bfrigon/alarm-clock-v3/pictures/decals/applying-decals-back-panel.jpg

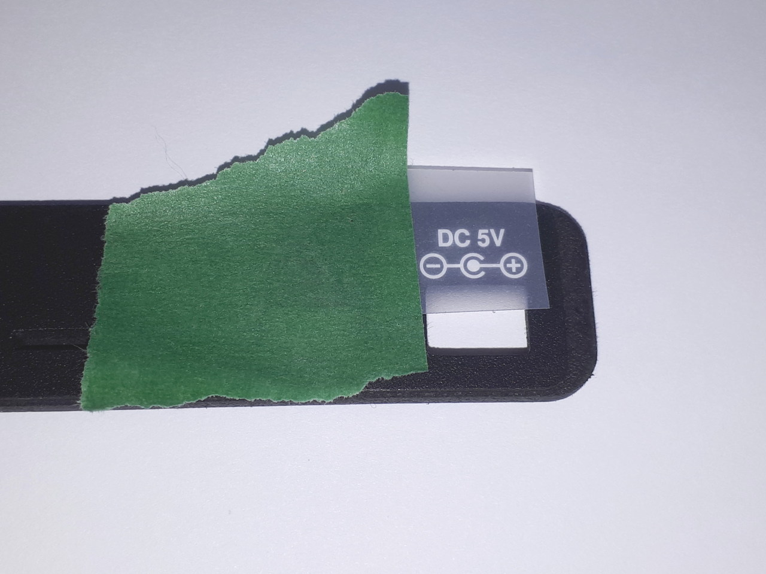
pictures/decals/applying-decals-back-panel.jpg
