bfrigon/alarm-clock-v3/pictures/decals/applying-decals-enclosure-bottom.jpg

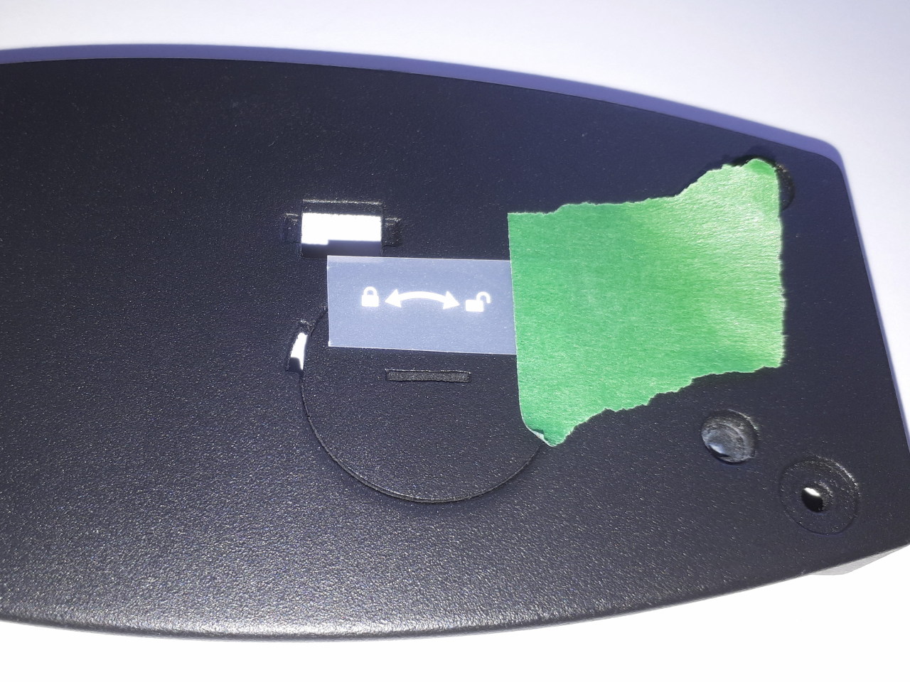
pictures/decals/applying-decals-enclosure-bottom.jpg
