bfrigon/alarm-clock-v3/pictures/decals/decals-back-panel-finished.jpg

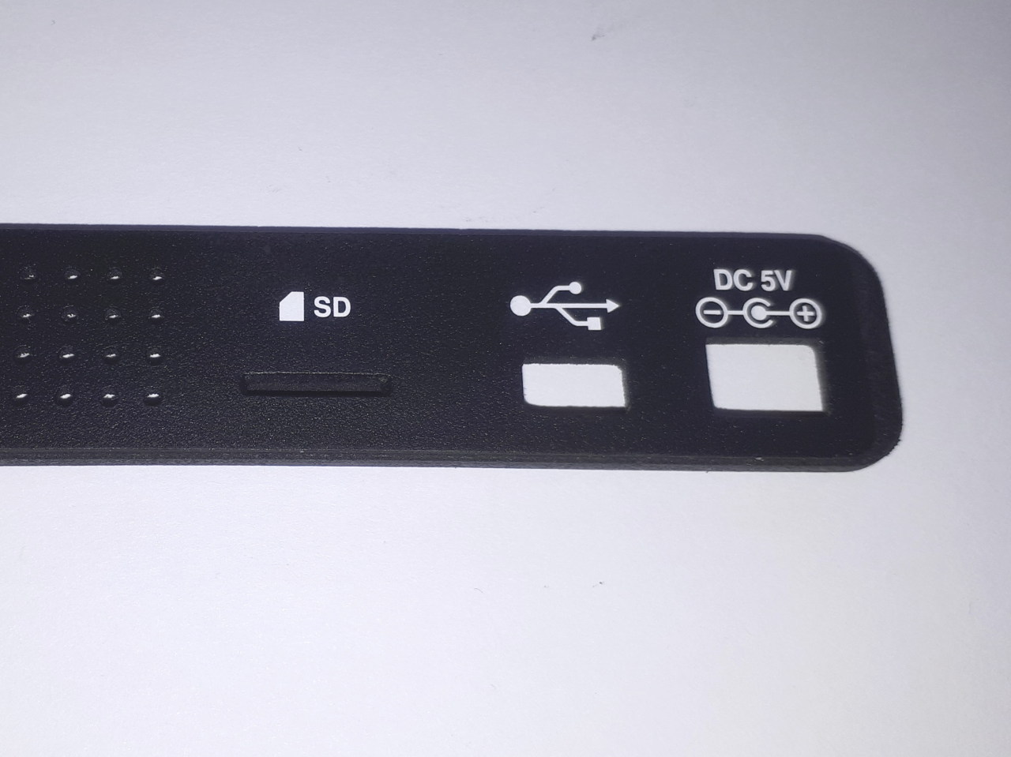
pictures/decals/decals-back-panel-finished.jpg
