bfrigon/alarm-clock-v3/pictures/decals/decals-back-panel.jpg

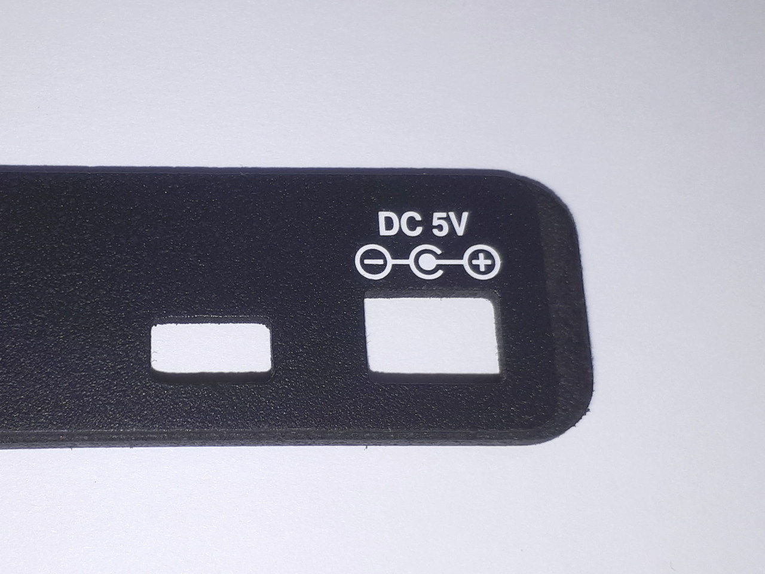
pictures/decals/decals-back-panel.jpg
