bfrigon/alarm-clock-v3/pictures/decals/decals-enclosure-back.jpg

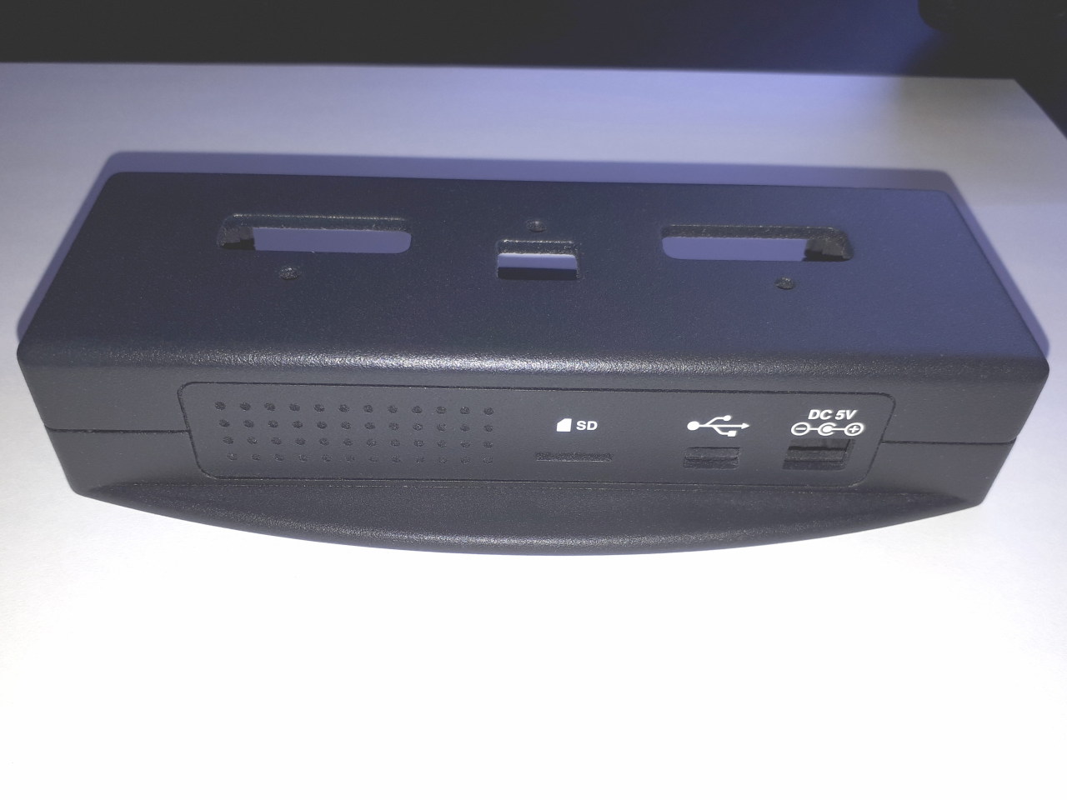
pictures/decals/decals-enclosure-back.jpg
