bfrigon/alarm-clock-v3/pictures/decals/decals-enclosure-bottom.jpg

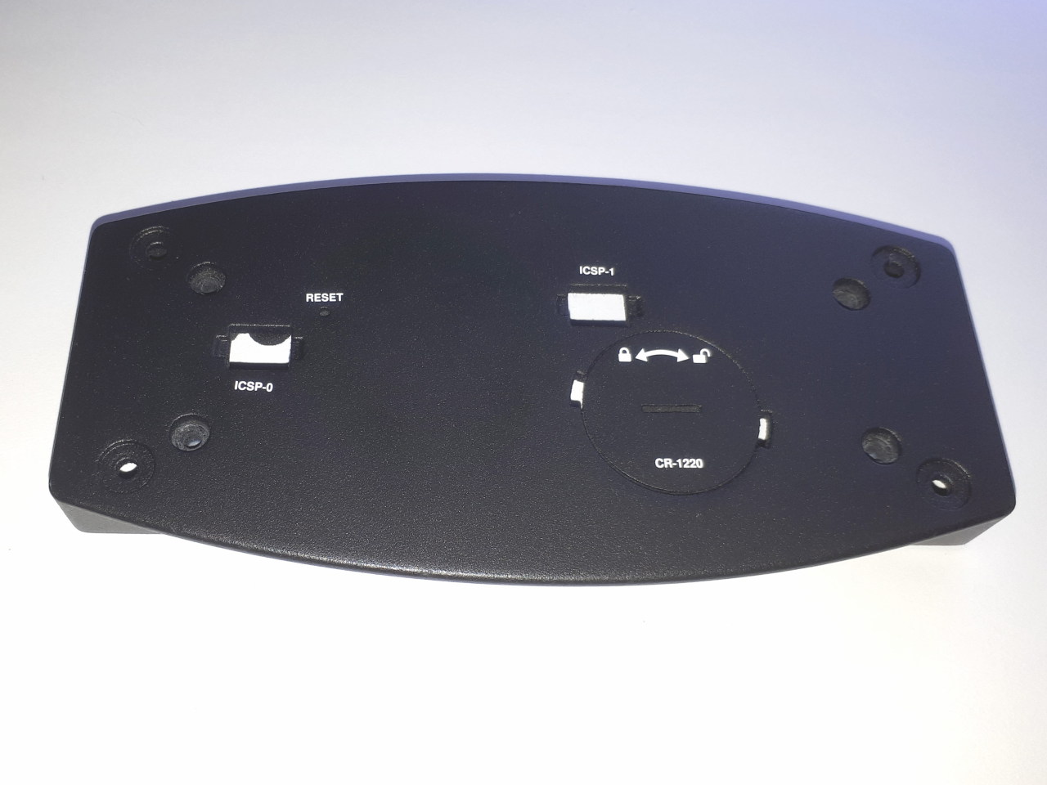
pictures/decals/decals-enclosure-bottom.jpg
