bfrigon/alarm-clock-v3/pictures/decals/decals-enclosure-io-openings.jpg

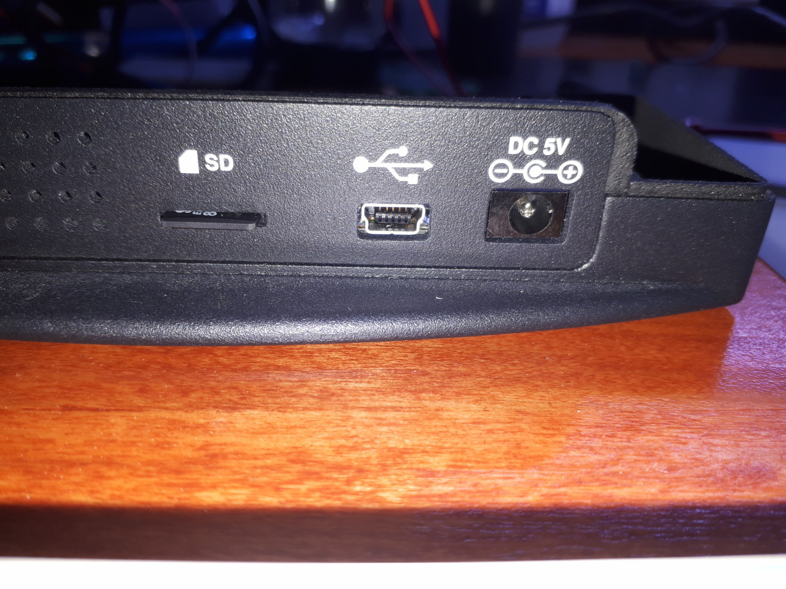
pictures/decals/decals-enclosure-io-openings.jpg
