bfrigon/alarm-clock-v3/pictures/decals/decals-enclosure-side.jpg

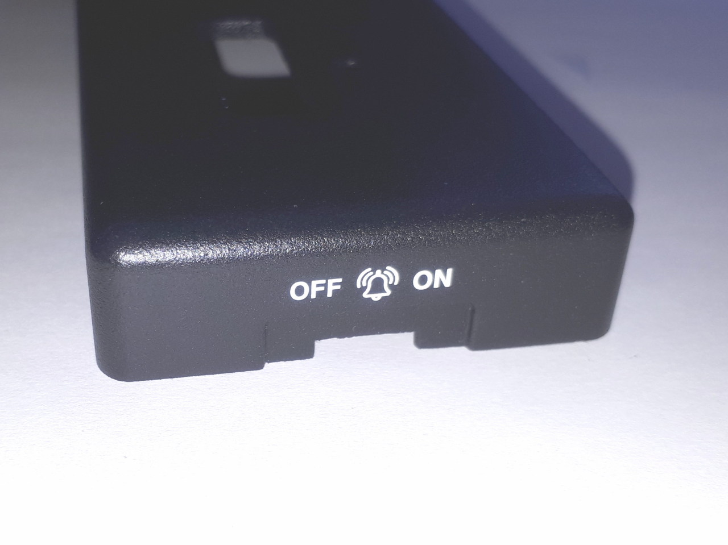
pictures/decals/decals-enclosure-side.jpg
