bfrigon/alarm-clock-v3/pictures/display-panel/diffuser-epoxy-finished.jpg

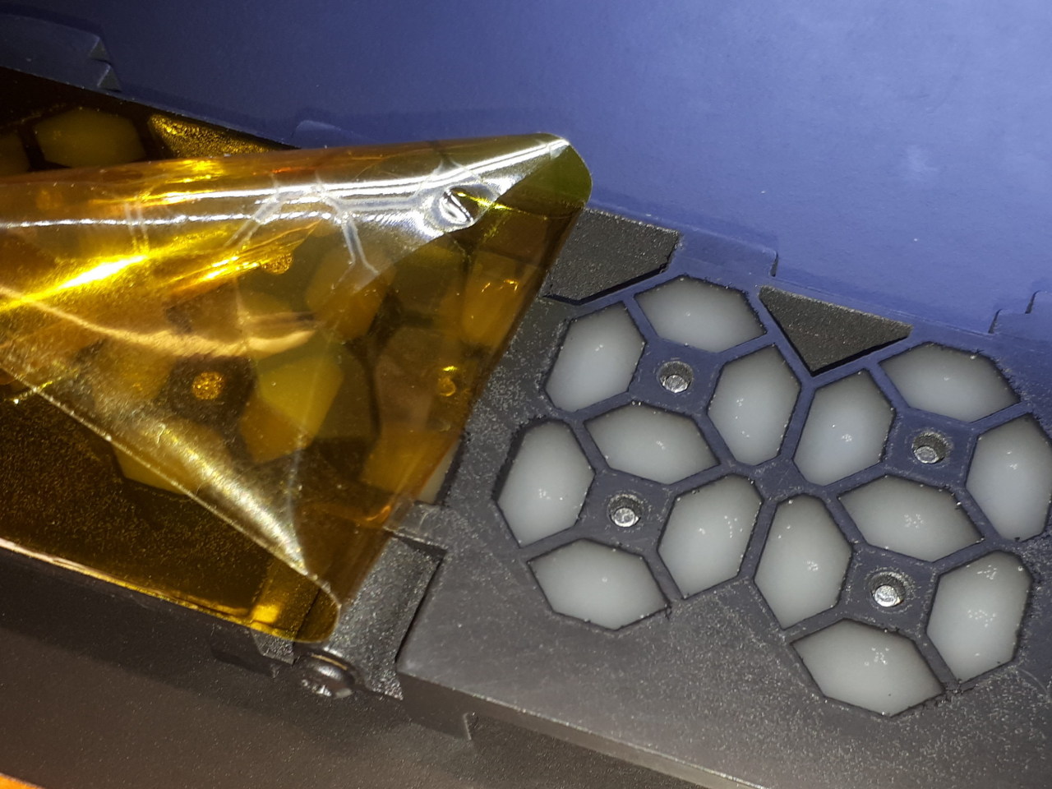
pictures/display-panel/diffuser-epoxy-finished.jpg
