bfrigon/alarm-clock-v3/pictures/display-panel/diffuser-epoxy-kapton-tape.jpg

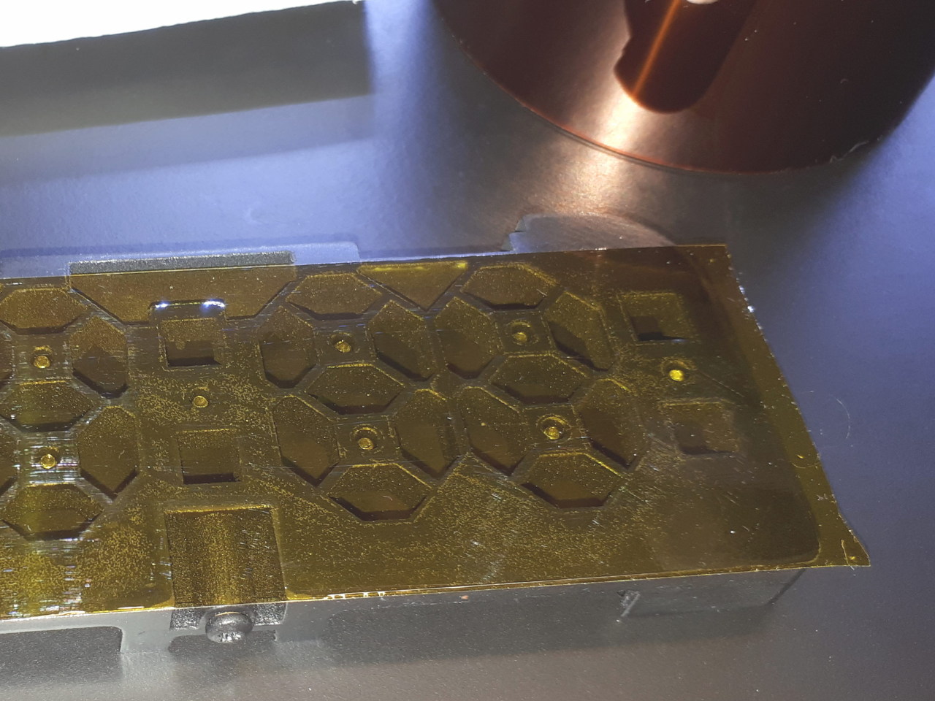
pictures/display-panel/diffuser-epoxy-kapton-tape.jpg
