bfrigon/alarm-clock-v3/pictures/display-panel/diffuser-epoxy-pour.jpg

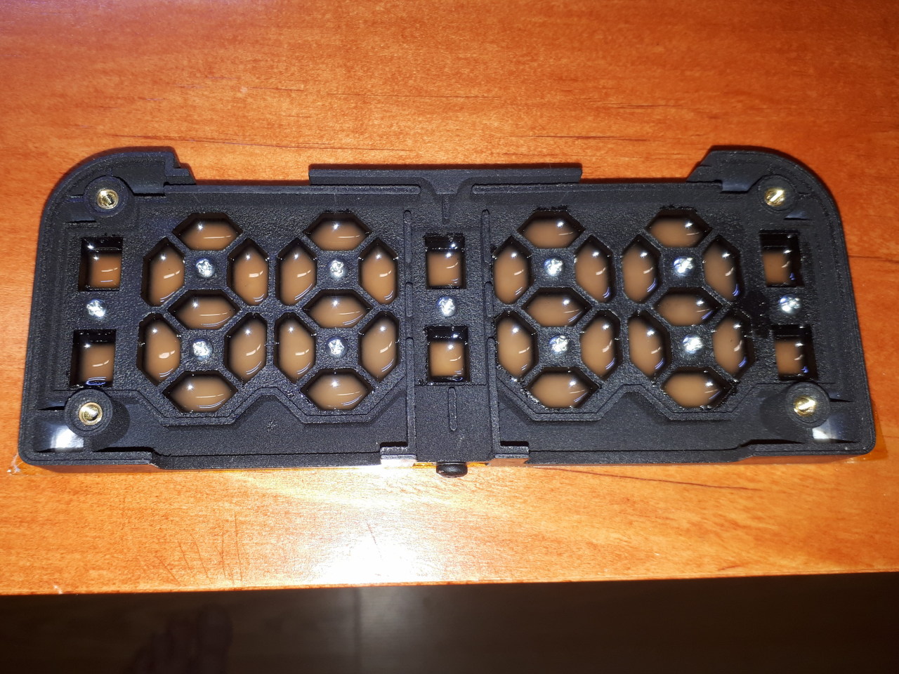
pictures/display-panel/diffuser-epoxy-pour.jpg
