bfrigon/alarm-clock-v3/pictures/display-panel/display-enclosure-first-sanding.jpg

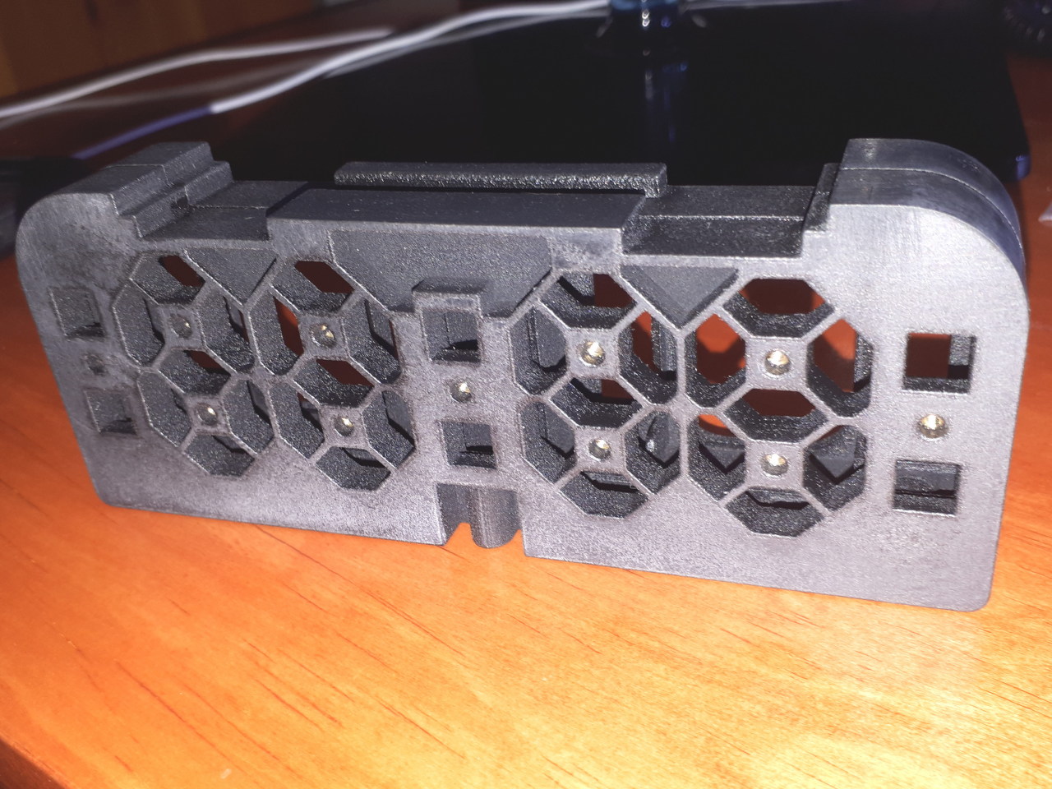
pictures/display-panel/display-enclosure-first-sanding.jpg
