bfrigon/alarm-clock-v3/pictures/display-panel/display-frame-back.jpg

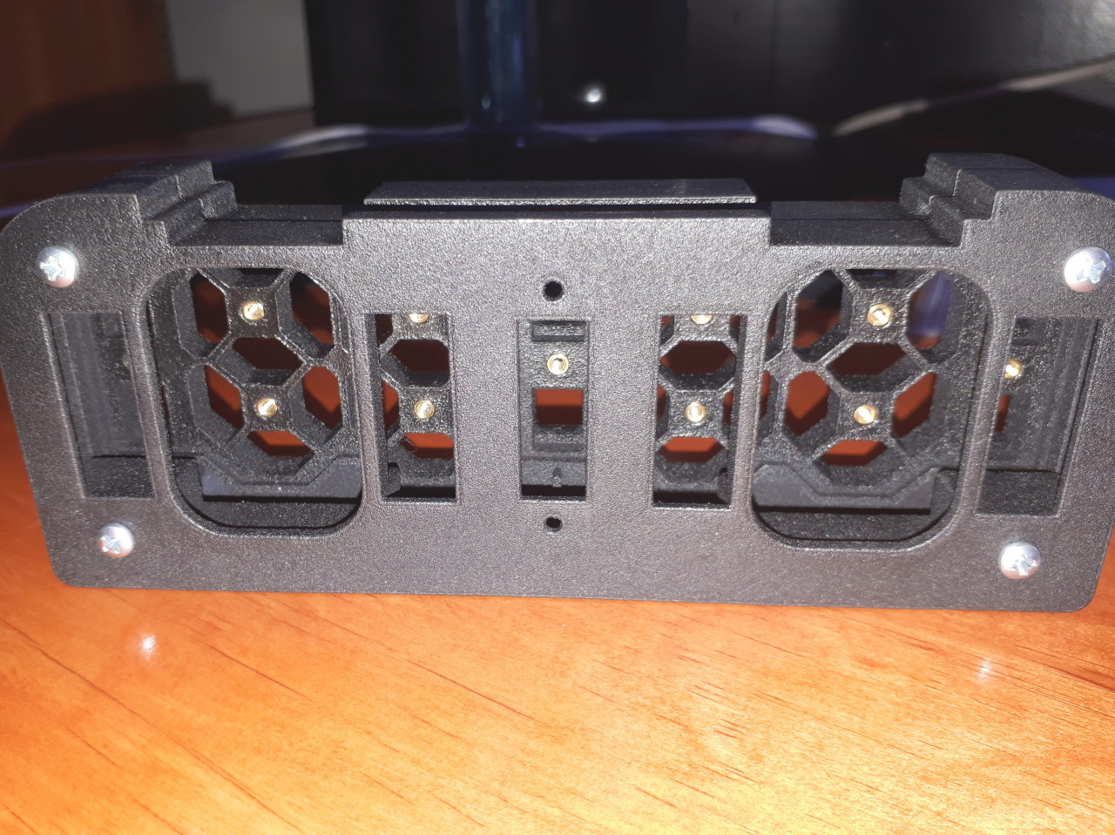
pictures/display-panel/display-frame-back.jpg
