bfrigon/alarm-clock-v3/pictures/display-panel/display-frame-final-sanding.jpg

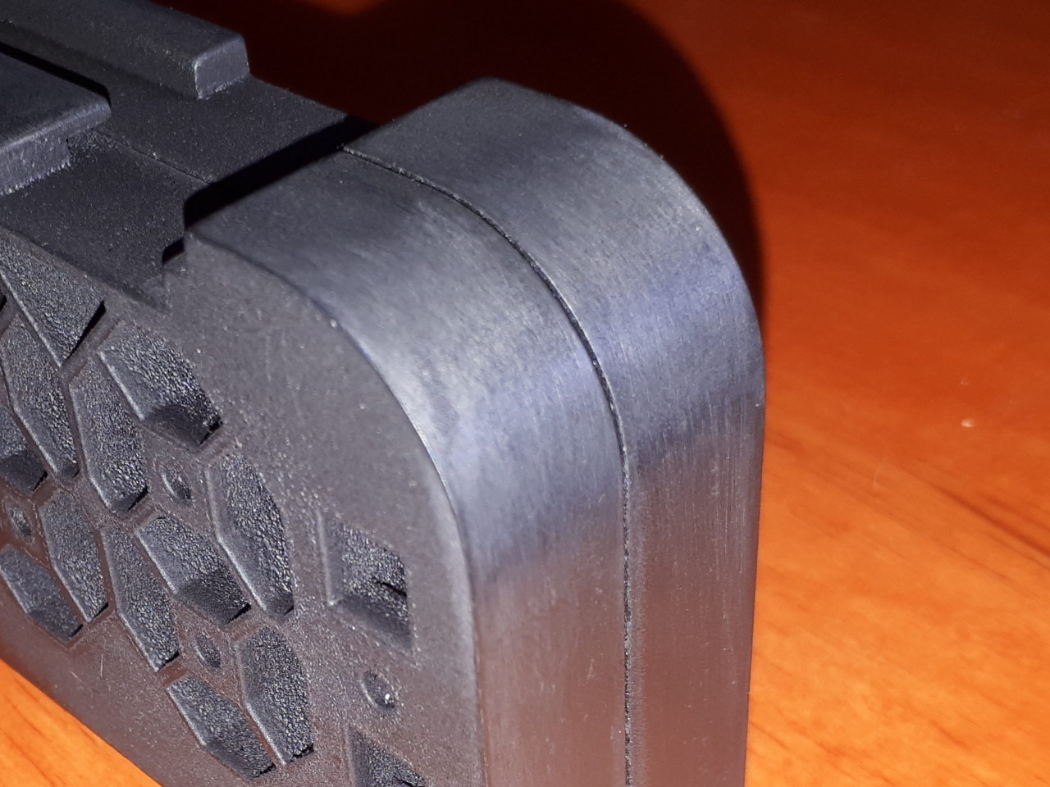
pictures/display-panel/display-frame-final-sanding.jpg
