bfrigon/alarm-clock-v3/pictures/display-panel/display-frame-first-sanding-closeup.jpg

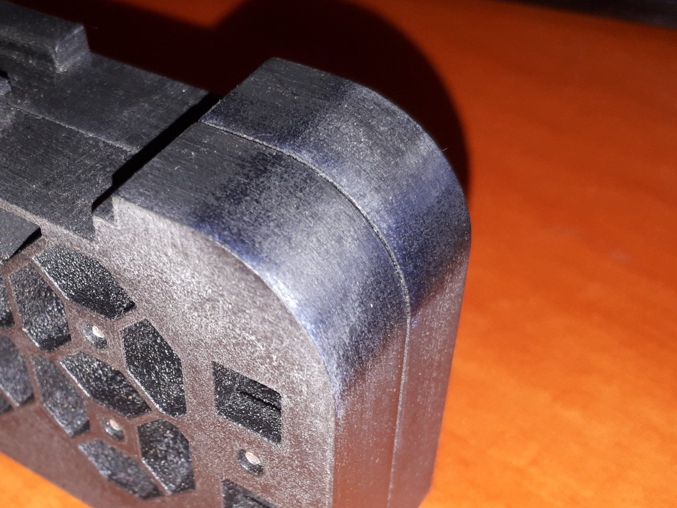
pictures/display-panel/display-frame-first-sanding-closeup.jpg
