bfrigon/alarm-clock-v3/pictures/display-panel/display-frame-front.jpg

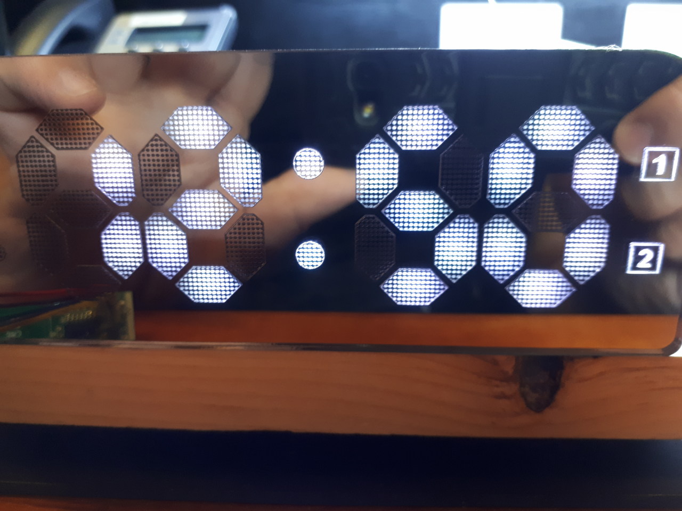
pictures/display-panel/display-frame-front.jpg
