bfrigon/alarm-clock-v3/pictures/display-panel/display-frame-paint-texture.jpg

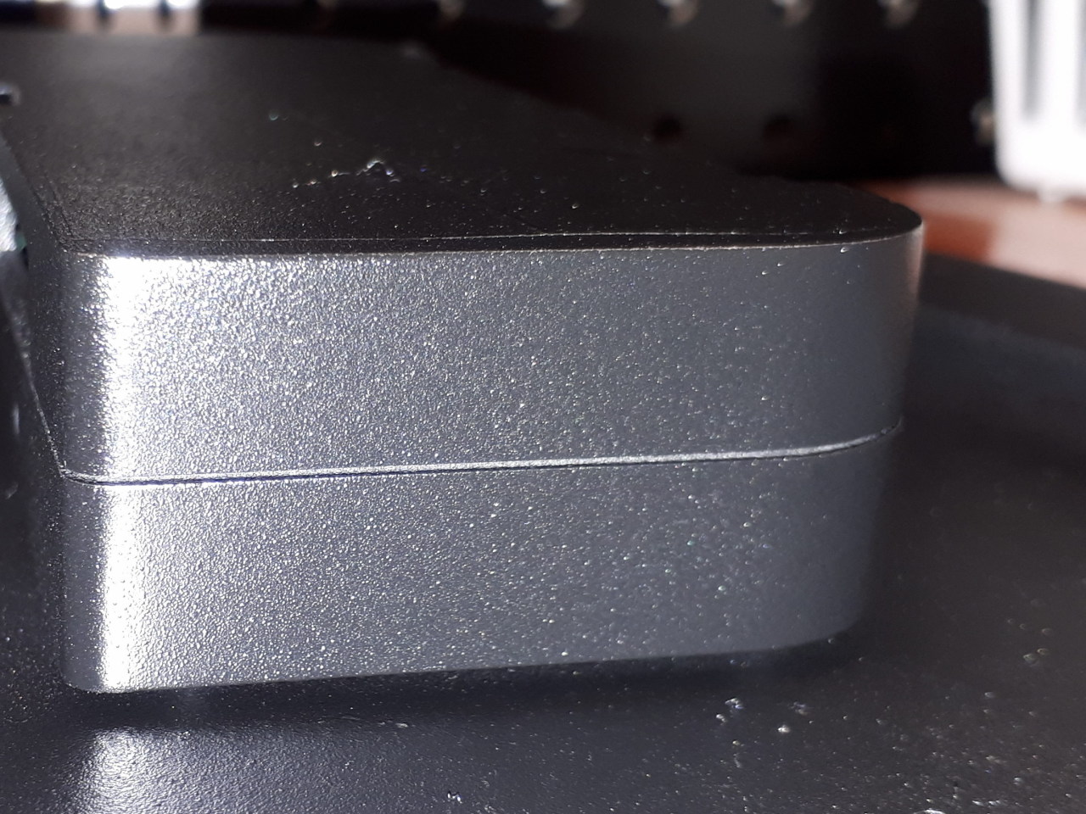
pictures/display-panel/display-frame-paint-texture.jpg
