bfrigon/alarm-clock-v3/pictures/display-panel/display-frame-raw-texture.jpg

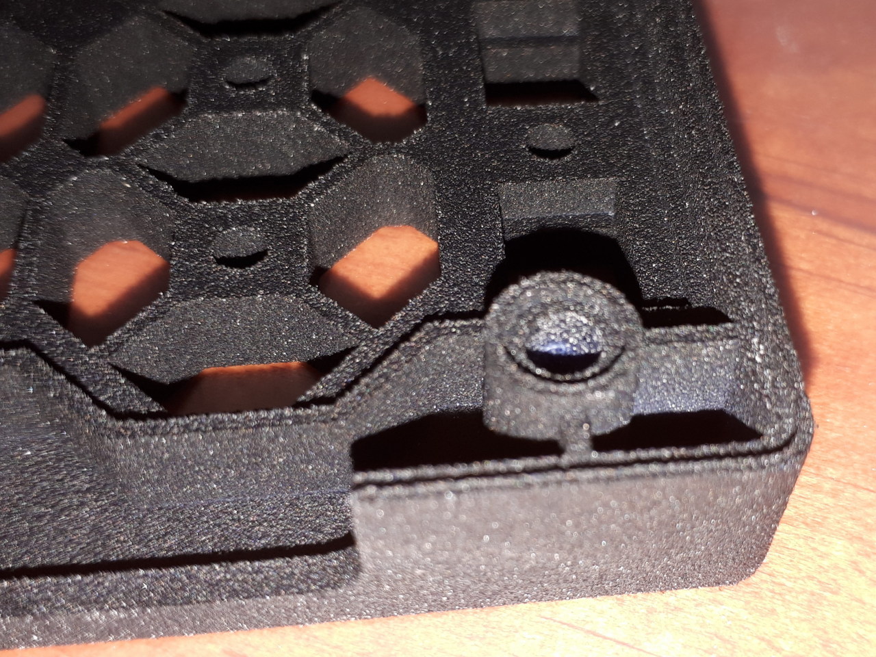
pictures/display-panel/display-frame-raw-texture.jpg
