bfrigon/alarm-clock-v3/pictures/display-panel/display-frame-shapeways.jpg

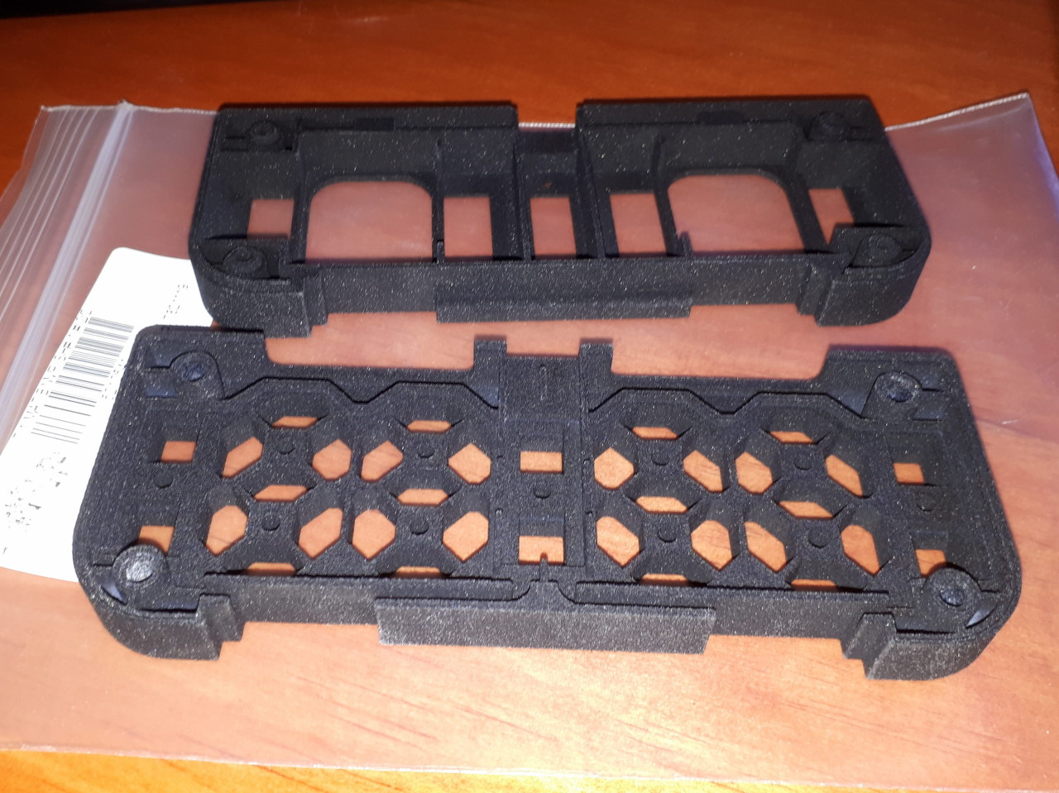
pictures/display-panel/display-frame-shapeways.jpg
