bfrigon/alarm-clock-v3/pictures/display-panel/display-touch-keypad.jpg

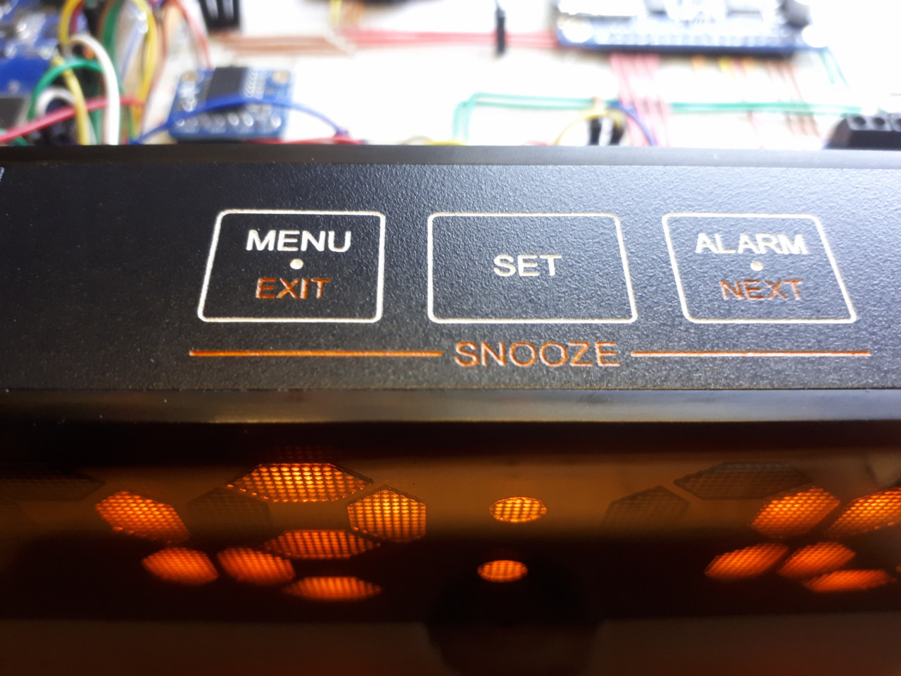
pictures/display-panel/display-touch-keypad.jpg
