bfrigon/alarm-clock-v3/pictures/display-panel/frame-front-with-touch-keypad.jpg

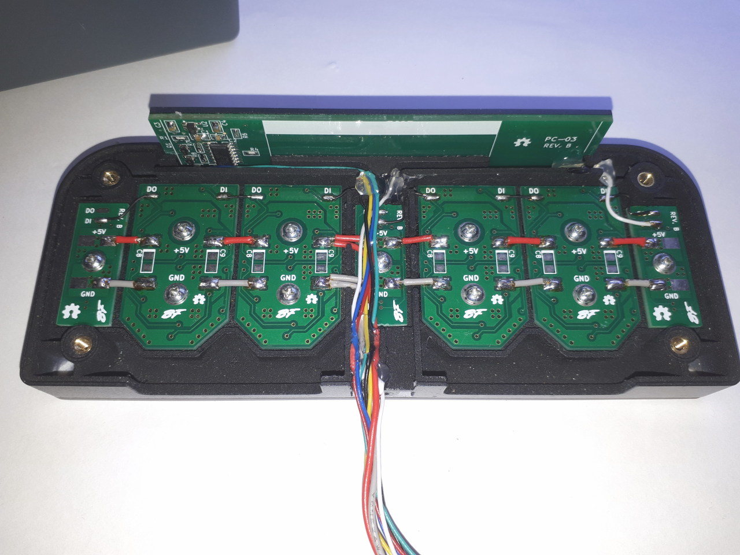
pictures/display-panel/frame-front-with-touch-keypad.jpg
