bfrigon/alarm-clock-v3/pictures/display-panel/front-frame-threaded-inserts.jpg

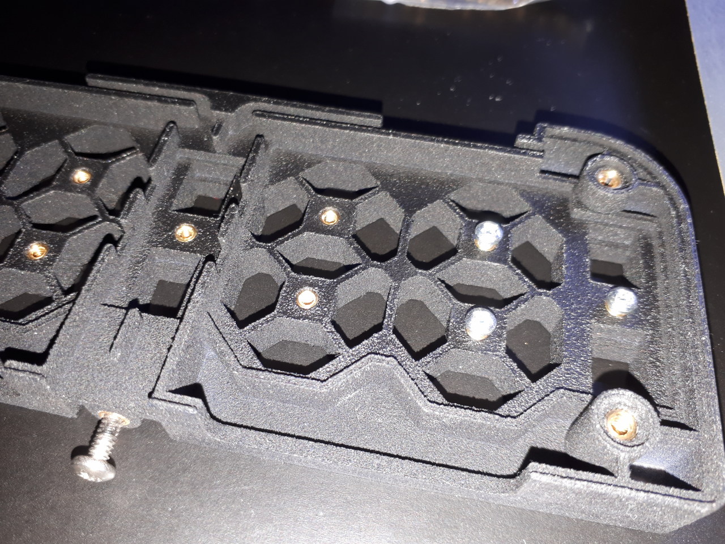
pictures/display-panel/front-frame-threaded-inserts.jpg
