bfrigon/alarm-clock-v3/pictures/display-panel/rgb-digits-pcb-panel.jpg

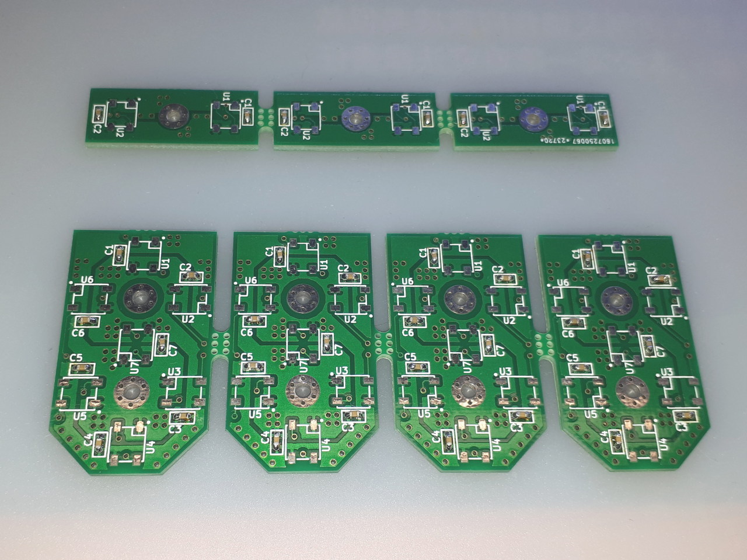
pictures/display-panel/rgb-digits-pcb-panel.jpg
