bfrigon/alarm-clock-v3/pictures/display-panel/rgb-lamp-pcb-back.jpg

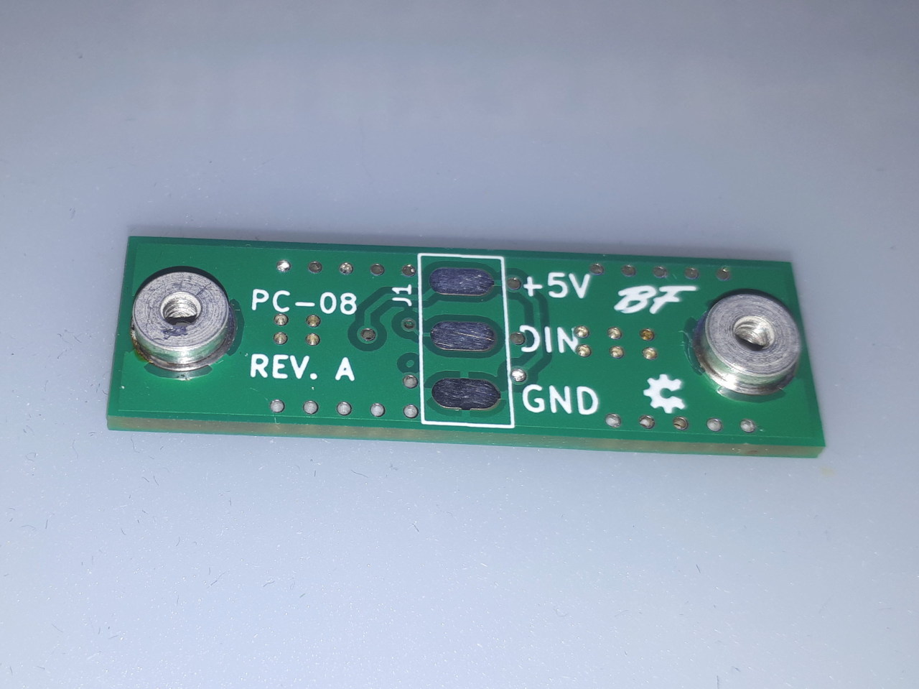
pictures/display-panel/rgb-lamp-pcb-back.jpg
