bfrigon/alarm-clock-v3/pictures/display-panel/rgb-lamp-pcb-front.jpg

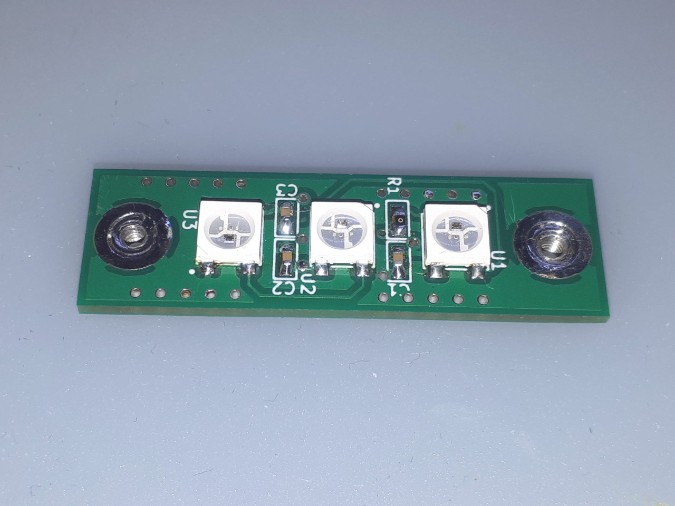
pictures/display-panel/rgb-lamp-pcb-front.jpg
