bfrigon/alarm-clock-v3/pictures/display-panel/touch-keypad-pcb.jpg

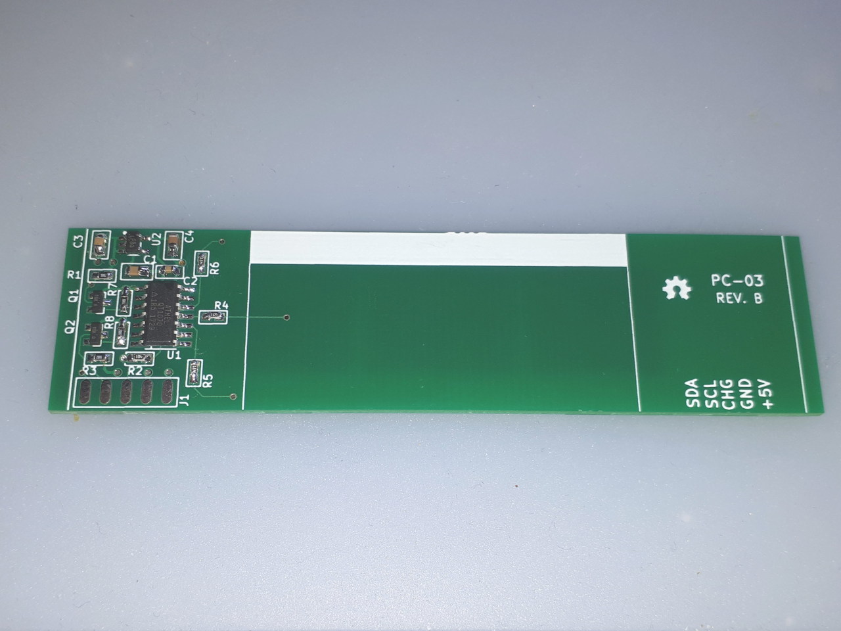
pictures/display-panel/touch-keypad-pcb.jpg
