bfrigon/alarm-clock-v3/pictures/enclosure/enclosure-first-sanding-bottom.jpg

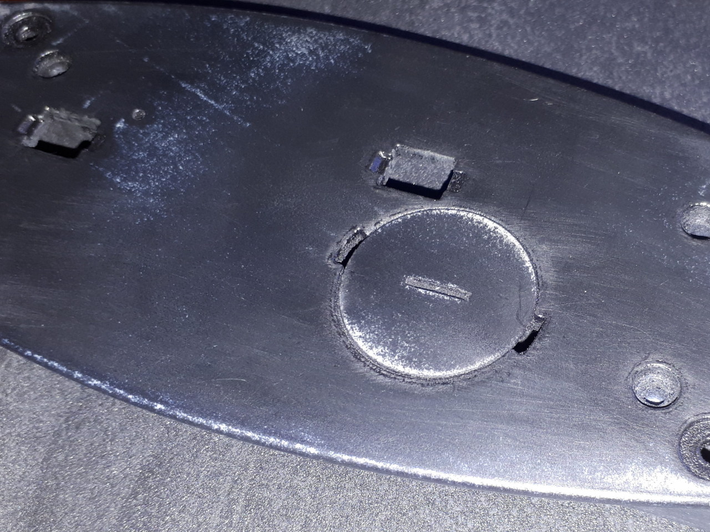
pictures/enclosure/enclosure-first-sanding-bottom.jpg
