bfrigon/alarm-clock-v3/pictures/enclosure/enclosure-first-sanding.jpg

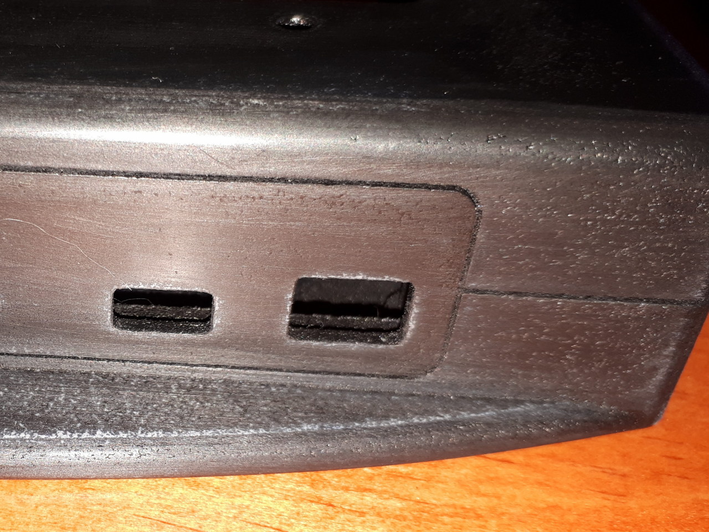
pictures/enclosure/enclosure-first-sanding.jpg
