bfrigon/alarm-clock-v3/pictures/enclosure/enclosure-raw-shapeways.jpg

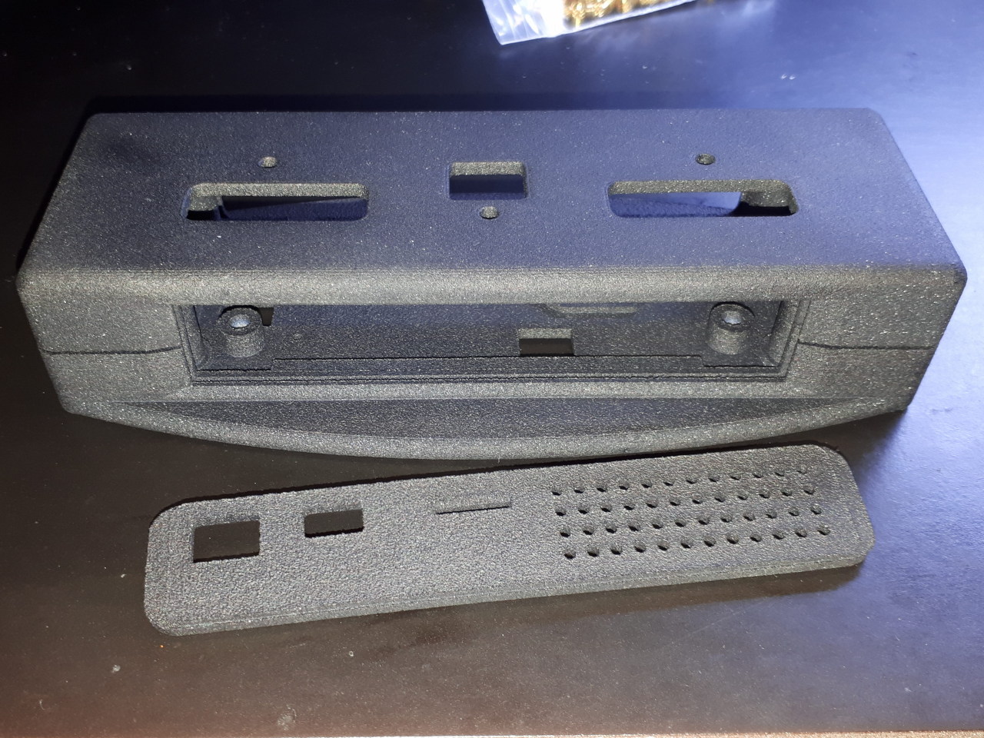
pictures/enclosure/enclosure-raw-shapeways.jpg
