bfrigon/alarm-clock-v3/pictures/enclosure/enclosure-varnish-layer-bottom.jpg

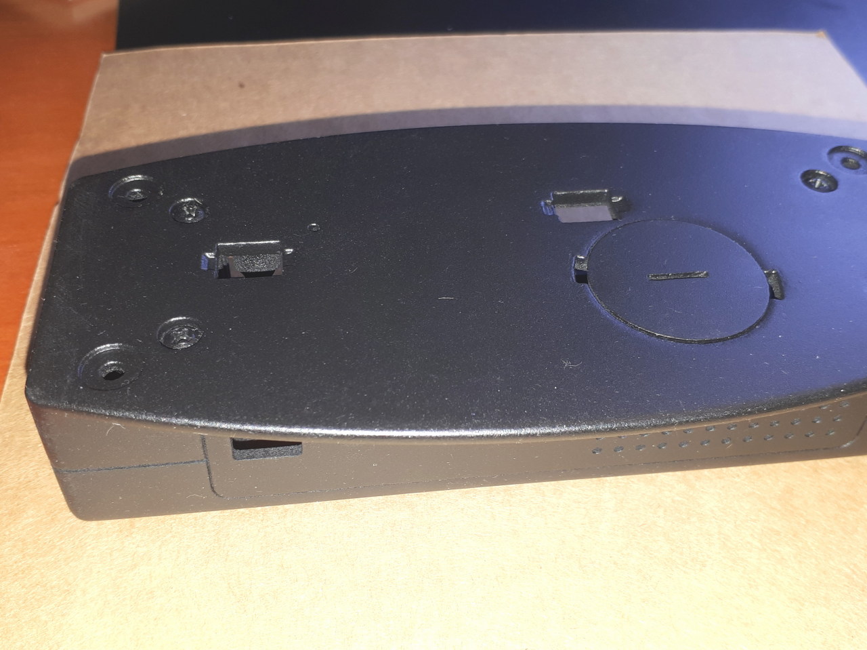
pictures/enclosure/enclosure-varnish-layer-bottom.jpg
