bfrigon/alarm-clock-v3/pictures/enclosure/enclosure-varnish-layer-front.jpg

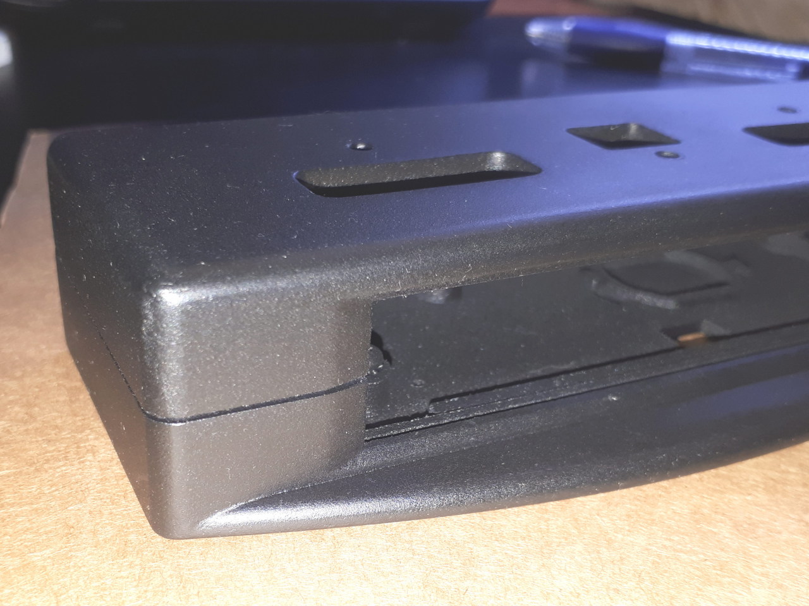
pictures/enclosure/enclosure-varnish-layer-front.jpg
