bfrigon/alarm-clock-v3/pictures/enclosure/threaded-inserts-fixing.jpg

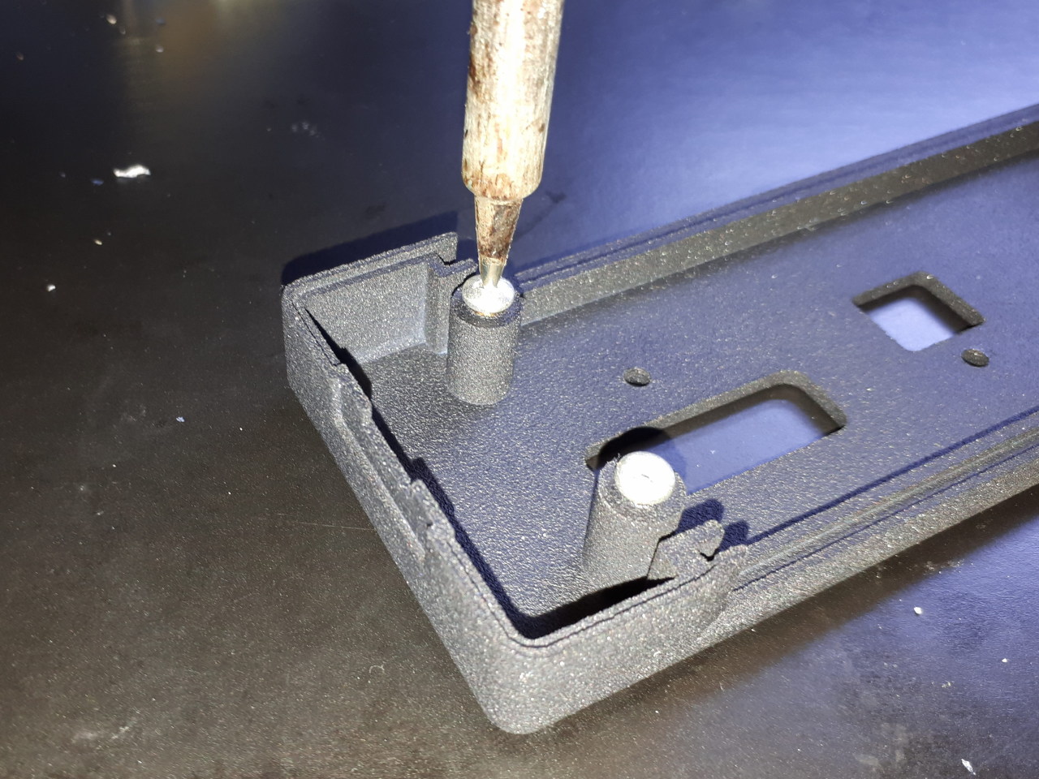
pictures/enclosure/threaded-inserts-fixing.jpg
