bfrigon/alarm-clock-v3/pictures/front-panel/20181004_022008.jpg

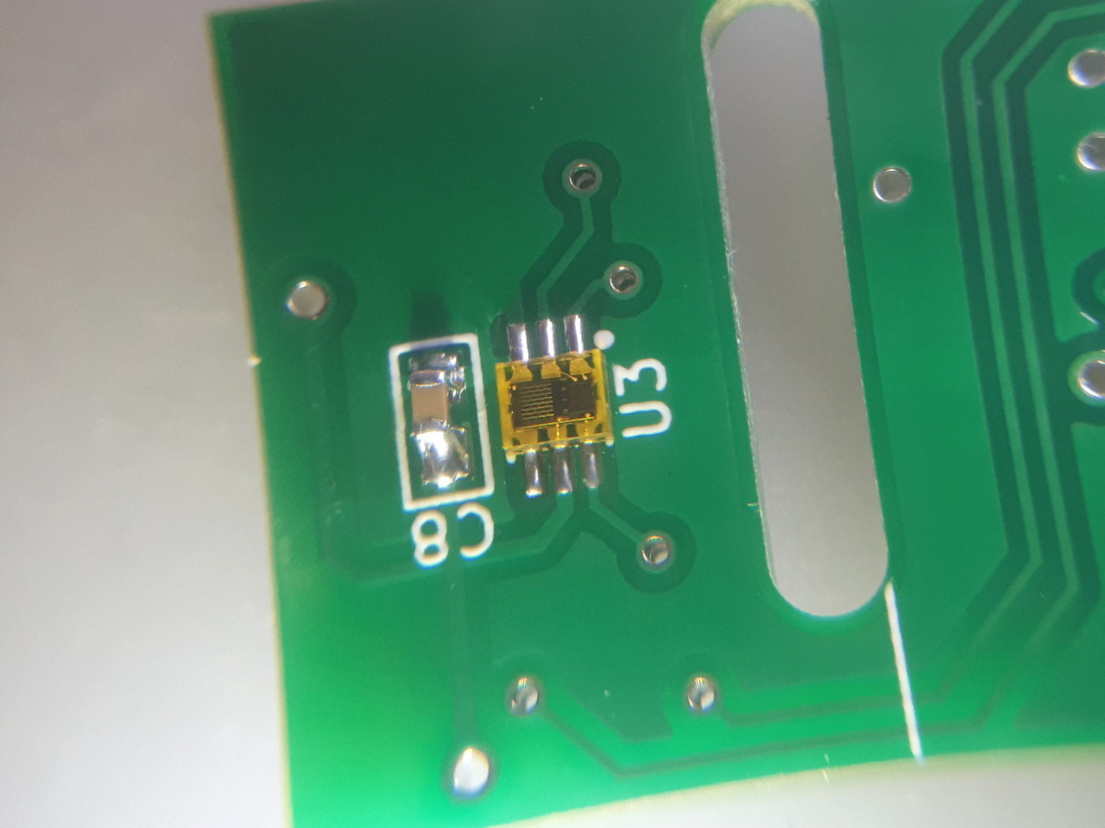
pictures/front-panel/20181004_022008.jpg
