bfrigon/alarm-clock-v3/pictures/front-panel/front-panel-pcb.jpg

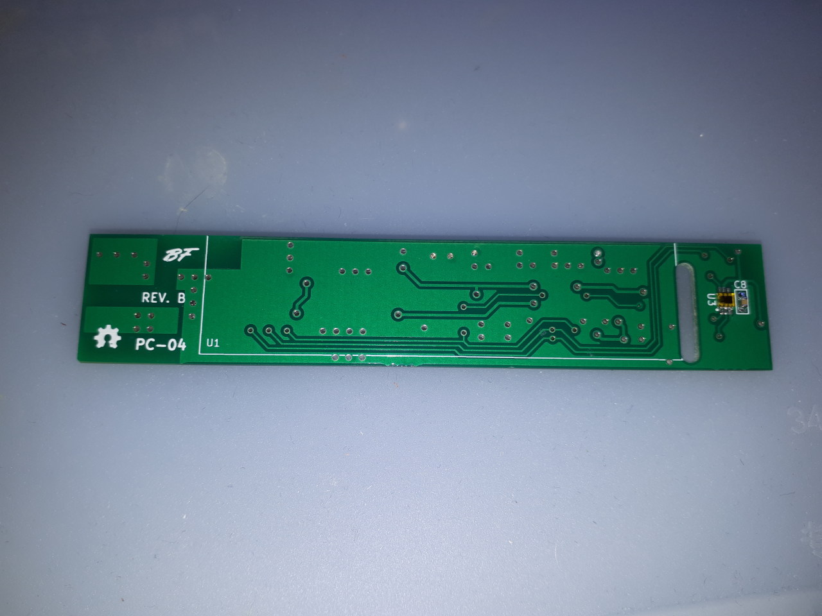
pictures/front-panel/front-panel-pcb.jpg
