bfrigon/alarm-clock-v3/pictures/keypad-overlay/acrylic-paint-orange.jpg

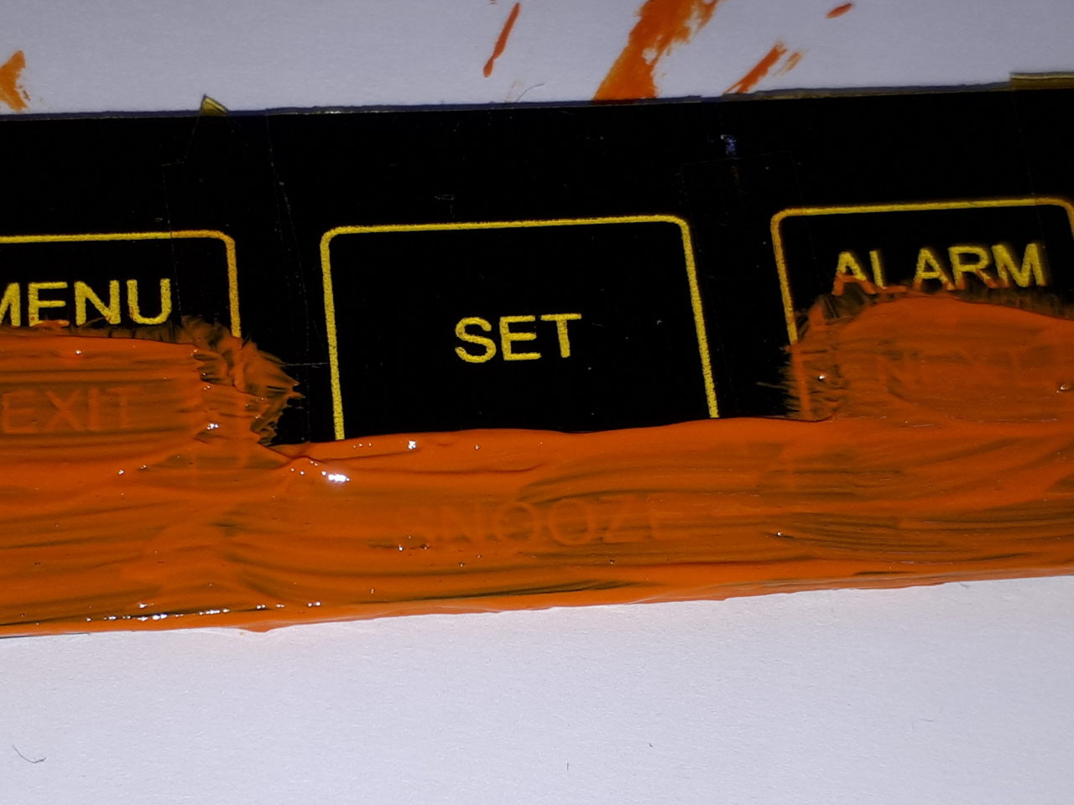
pictures/keypad-overlay/acrylic-paint-orange.jpg
