bfrigon/alarm-clock-v3/pictures/keypad-overlay/acrylic-paint-white.jpg

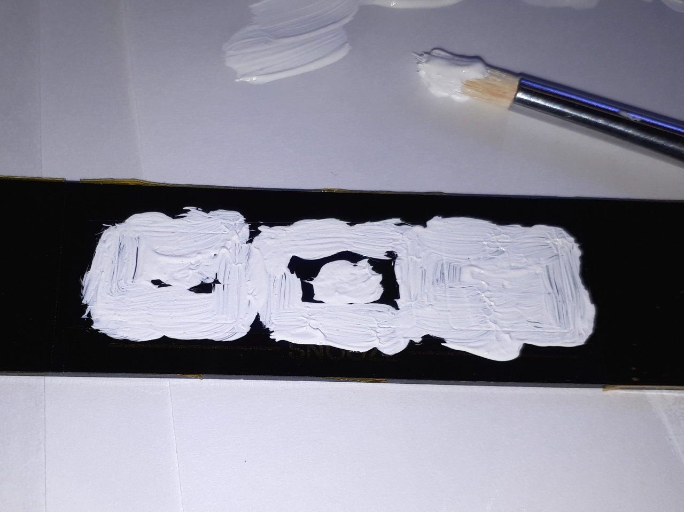
pictures/keypad-overlay/acrylic-paint-white.jpg
