bfrigon/alarm-clock-v3/pictures/keypad-overlay/clear-coated.jpg

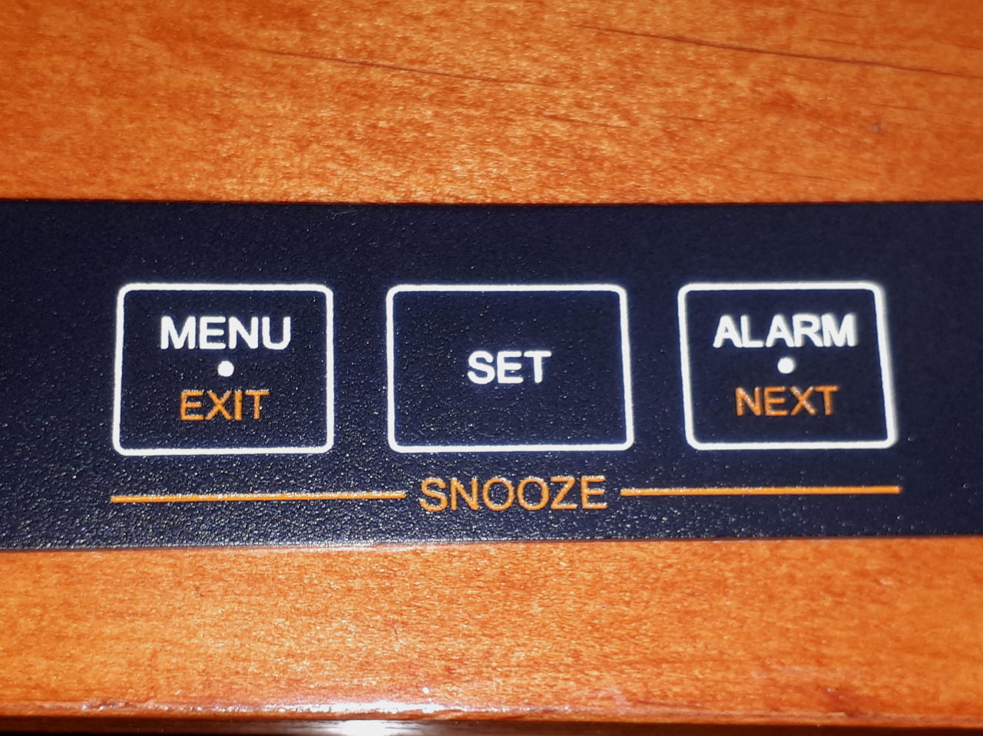
pictures/keypad-overlay/clear-coated.jpg
