bfrigon/alarm-clock-v3/pictures/keypad-overlay/dry-film-acrylic-paint.jpg

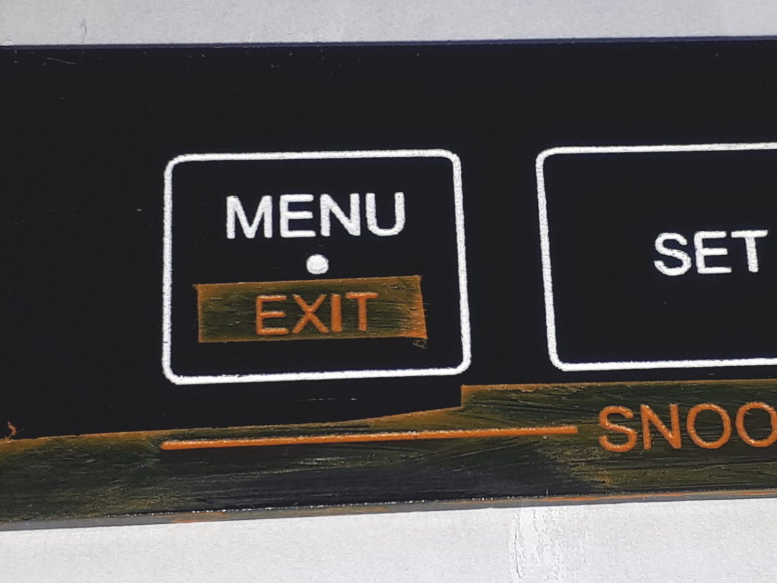
pictures/keypad-overlay/dry-film-acrylic-paint.jpg
