bfrigon/alarm-clock-v3/pictures/keypad-overlay/engraving-filled.jpg

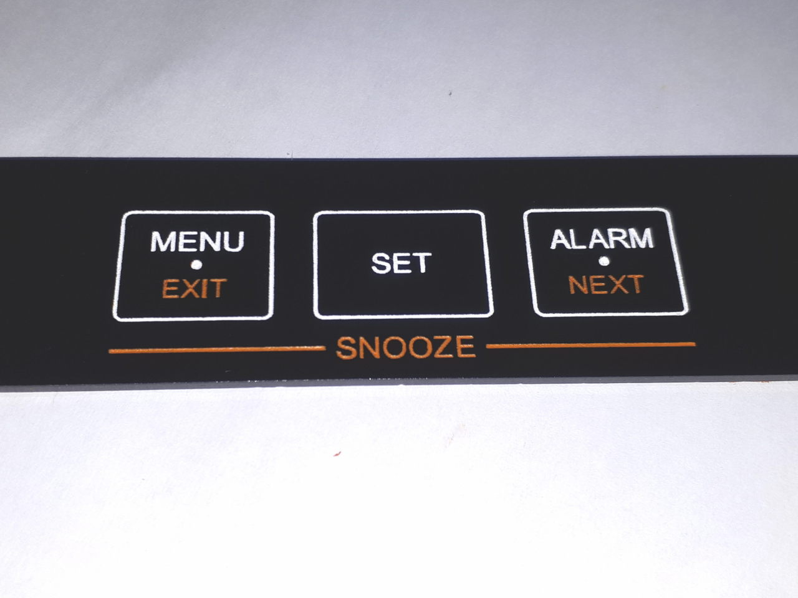
pictures/keypad-overlay/engraving-filled.jpg
