bfrigon/alarm-clock-v3/pictures/keypad-overlay/laser-engraving-overlay.jpg

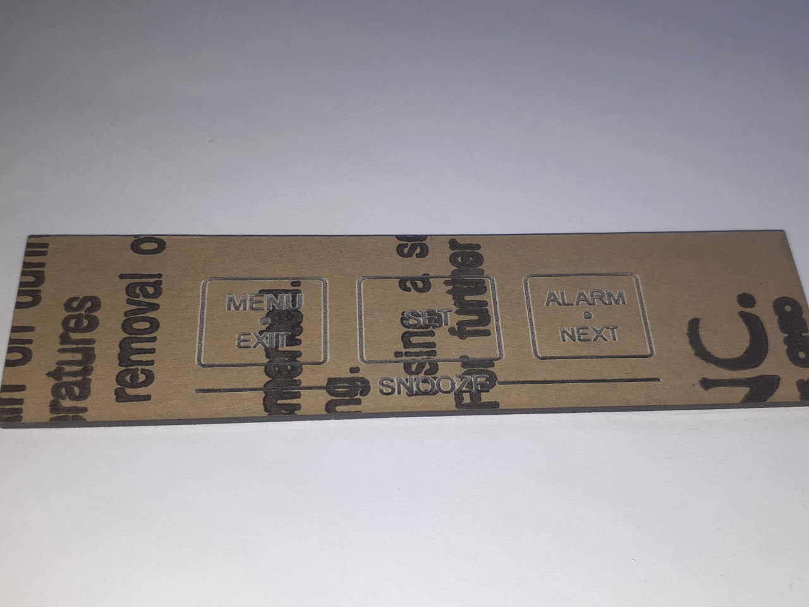
pictures/keypad-overlay/laser-engraving-overlay.jpg
