bfrigon/alarm-clock-v3/pictures/keypad-overlay/masking-orange-color.jpg

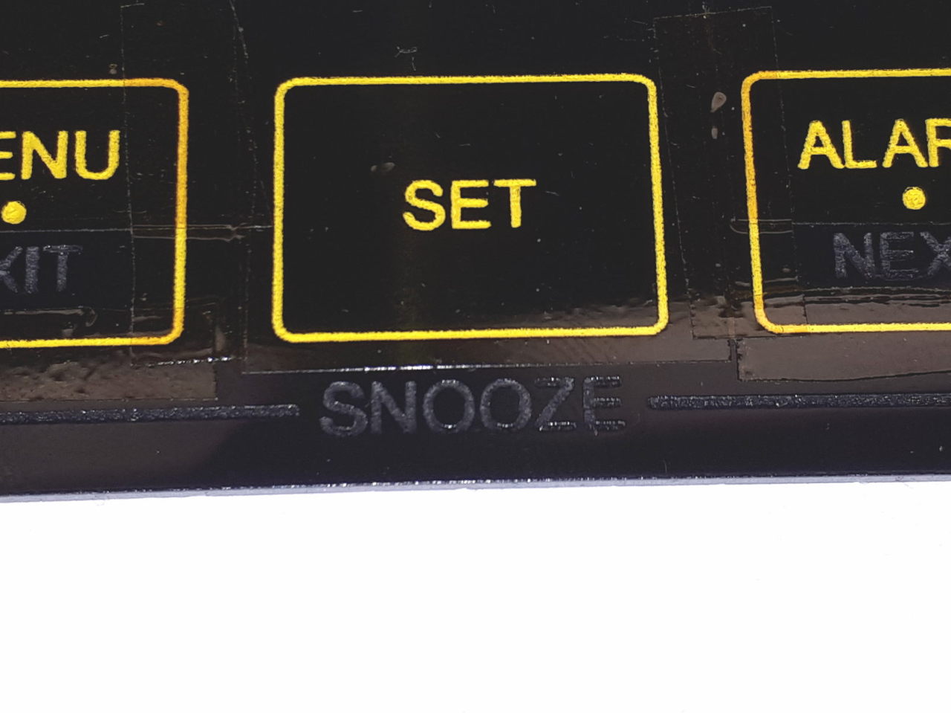
pictures/keypad-overlay/masking-orange-color.jpg
