bfrigon/alarm-clock-v3/pictures/keypad-overlay/masking-white-color.jpg

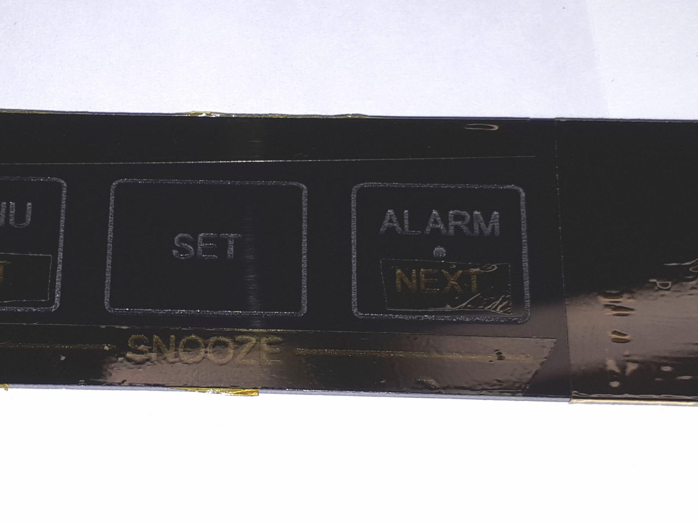
pictures/keypad-overlay/masking-white-color.jpg
