bfrigon/alarm-clock-v3/pictures/keypad-overlay/white-color-applied.jpg

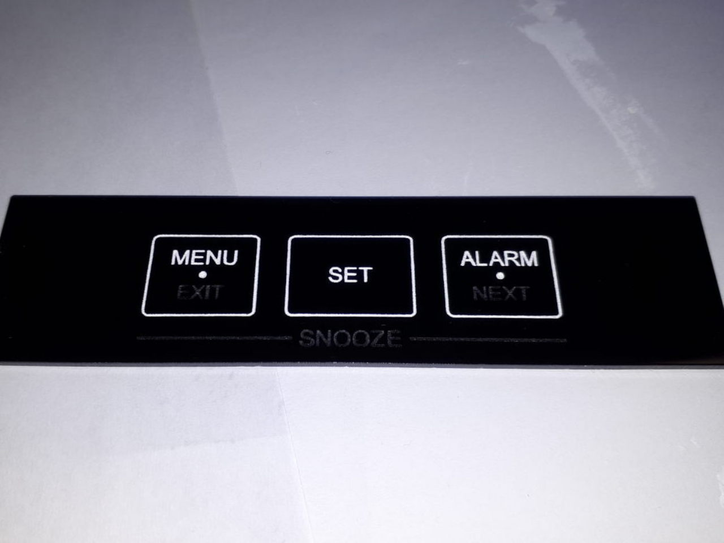
pictures/keypad-overlay/white-color-applied.jpg
