bfrigon/alarm-clock-v3/pictures/model-render/back.jpg

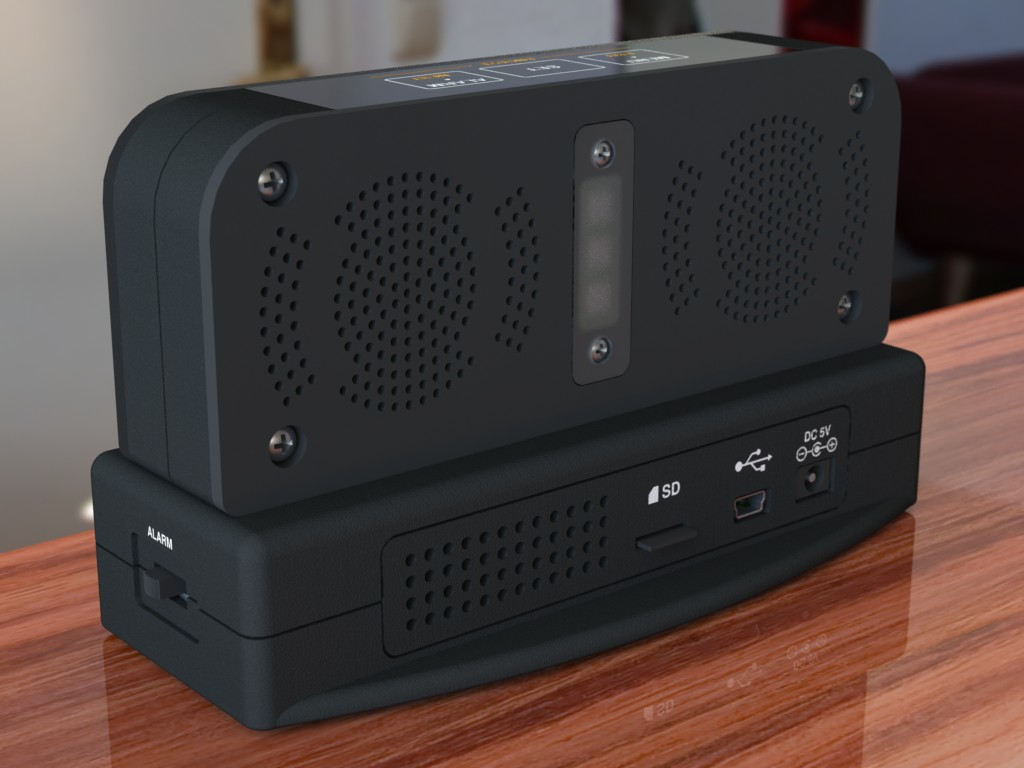
pictures/model-render/back.jpg
