bfrigon/alarm-clock-v3/pictures/model-render/front.jpg

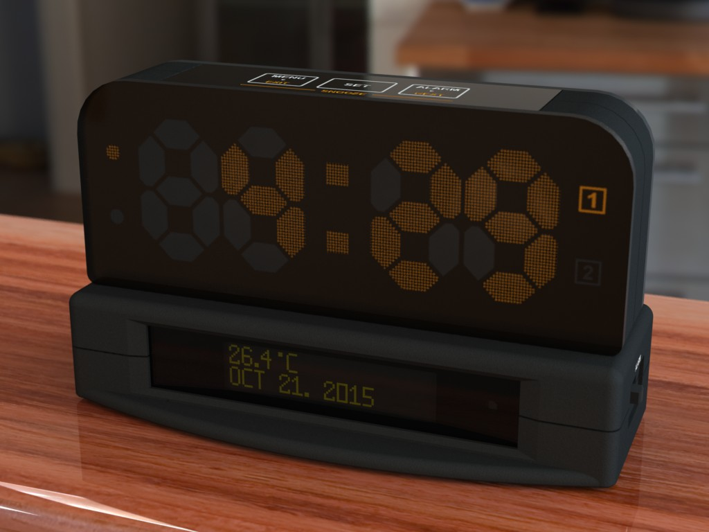
pictures/model-render/front.jpg
