bfrigon/alarm-clock-v3/pictures/model-render/mb.jpg

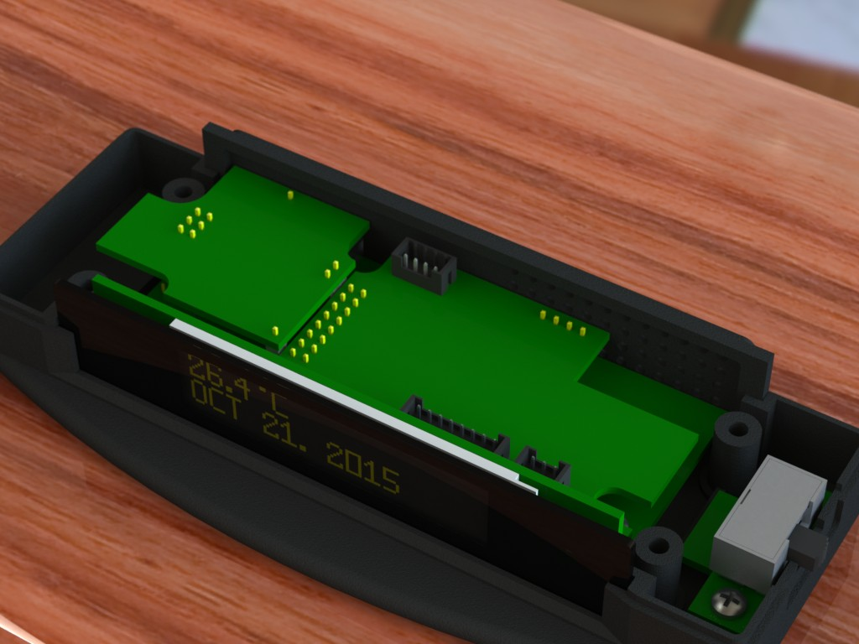
pictures/model-render/mb.jpg
