bfrigon/alarm-clock-v3/pictures/model-render/side.jpg

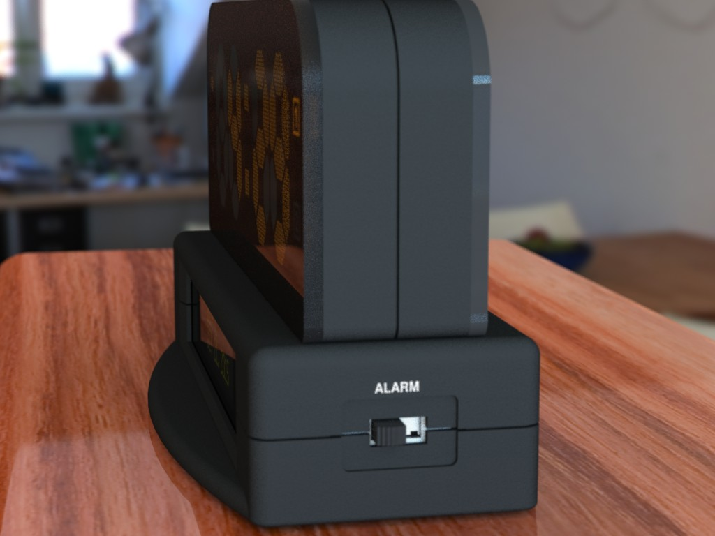
pictures/model-render/side.jpg
