bfrigon/alarm-clock-v3/pictures/psu/battery-holder.jpg

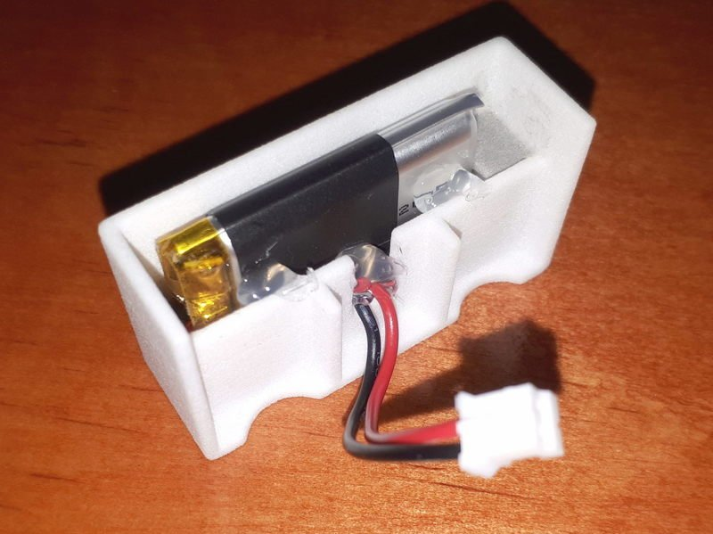
pictures/psu/battery-holder.jpg
