bfrigon/alarm-clock-v3/pictures/psu/psu-pcs-reflowed.jpg

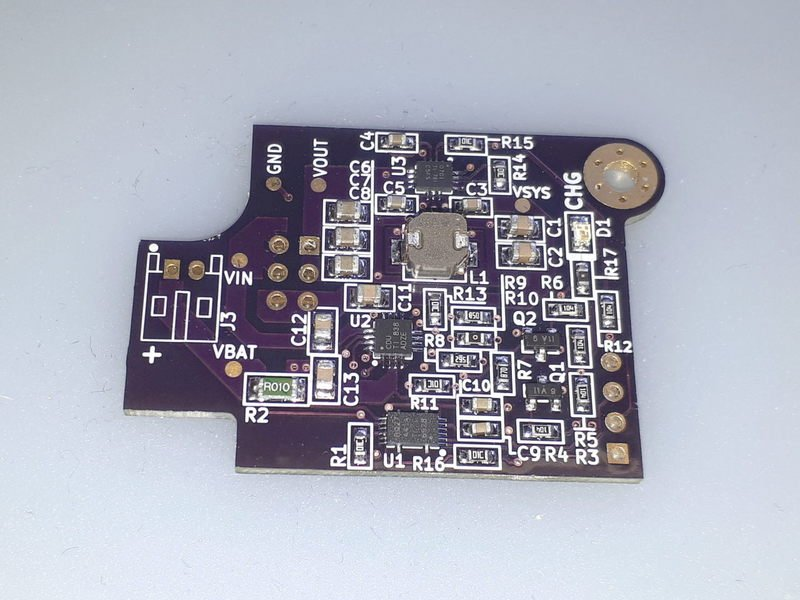
pictures/psu/psu-pcs-reflowed.jpg
