bfrigon/alarm-clock-v3/pictures/enclosure/enclosure-parts-washed.jpg

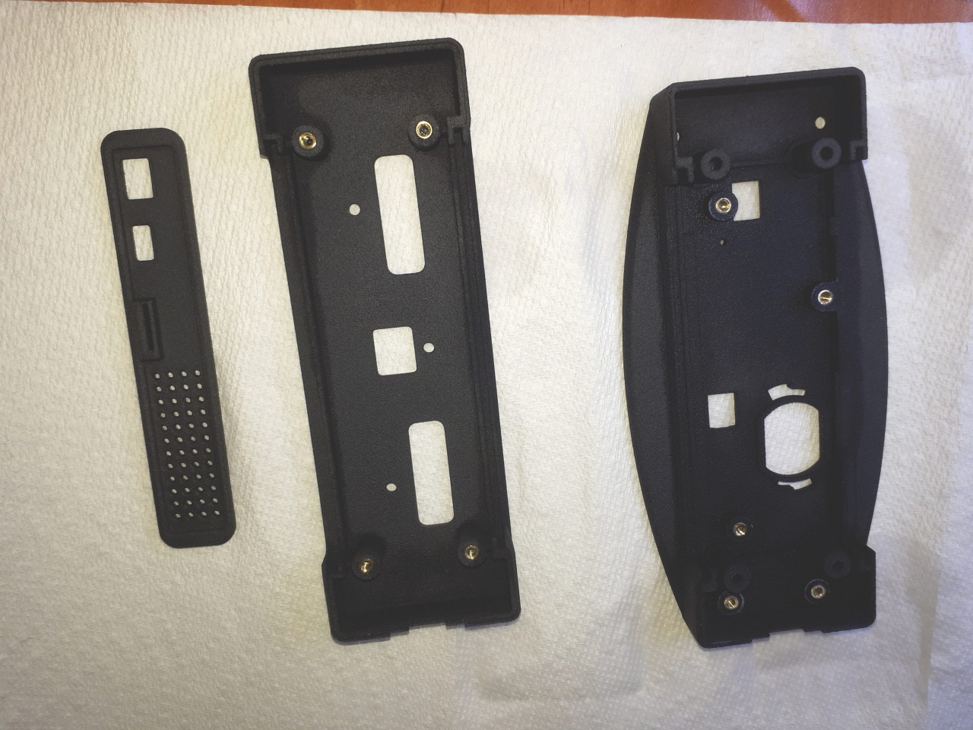
pictures/enclosure/enclosure-parts-washed.jpg
