bfrigon/alarm-clock-v3/pictures/motherboard/motherboard-parts.jpg

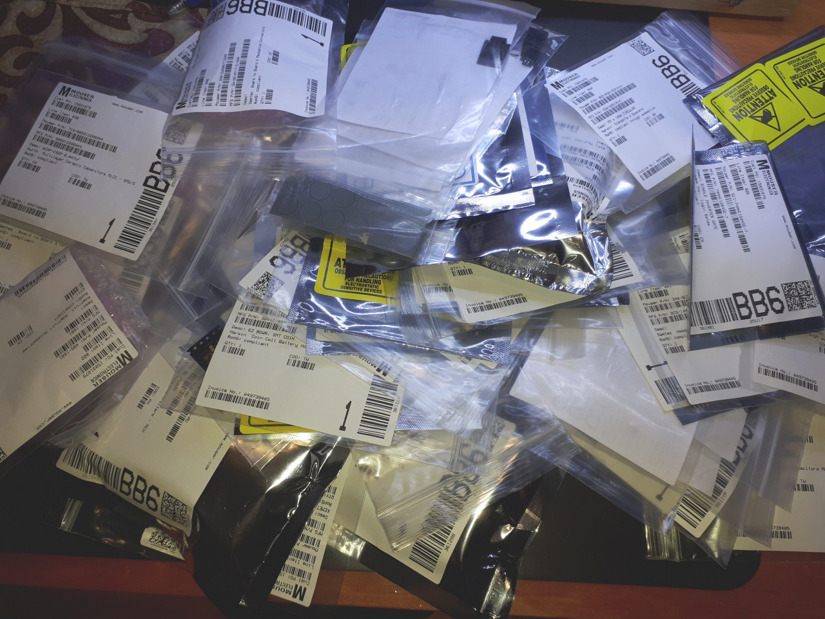
pictures/motherboard/motherboard-parts.jpg
