bfrigon/alarm-clock-v3/drawings/mechanical/clkv3-dwg-35_final-assembly.pdf

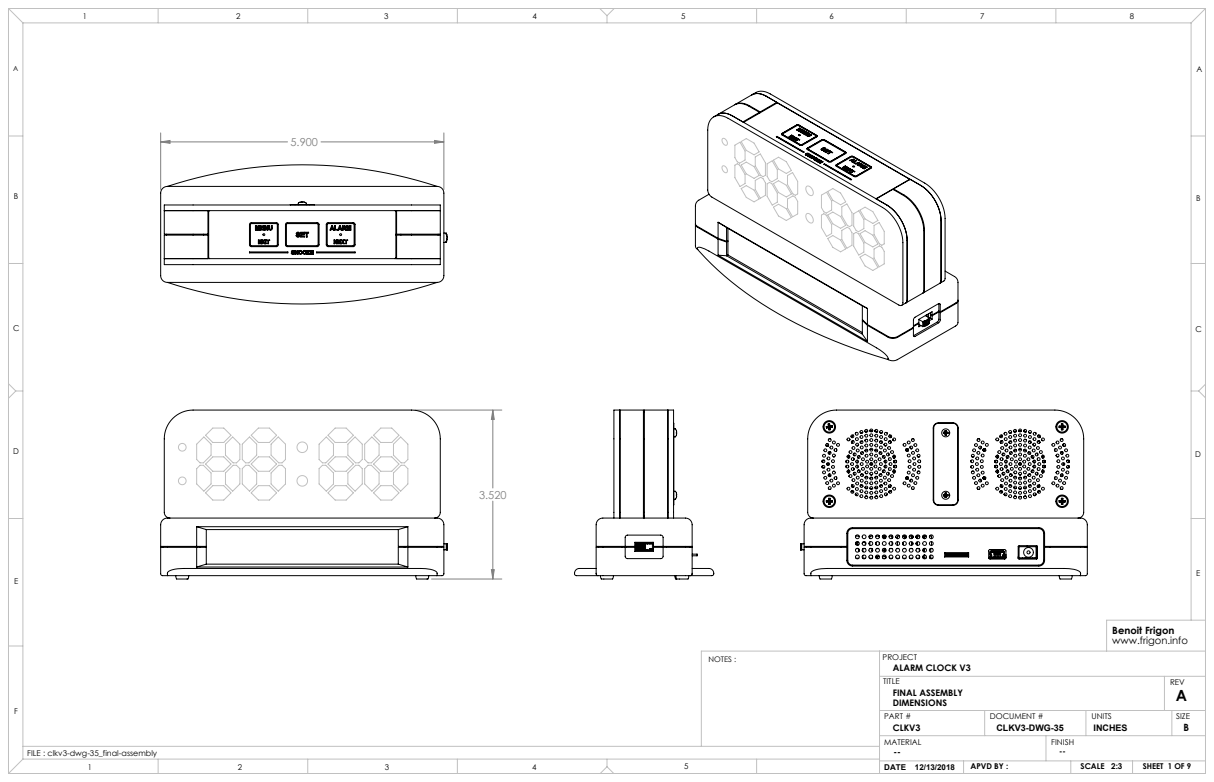
[picture p64: page 1]
SHEET 1 OF 9; ALARM CLOCK V3; FINAL ASSEMBLY; PART #; DOCUMENT #; UNITS; DATE 12/13/2018; SCALE 2:3; NOTES :; APVD BY :

Benoit Frigon
www.frigon.info

FILE : clkv3-dwg-35_final-assembly

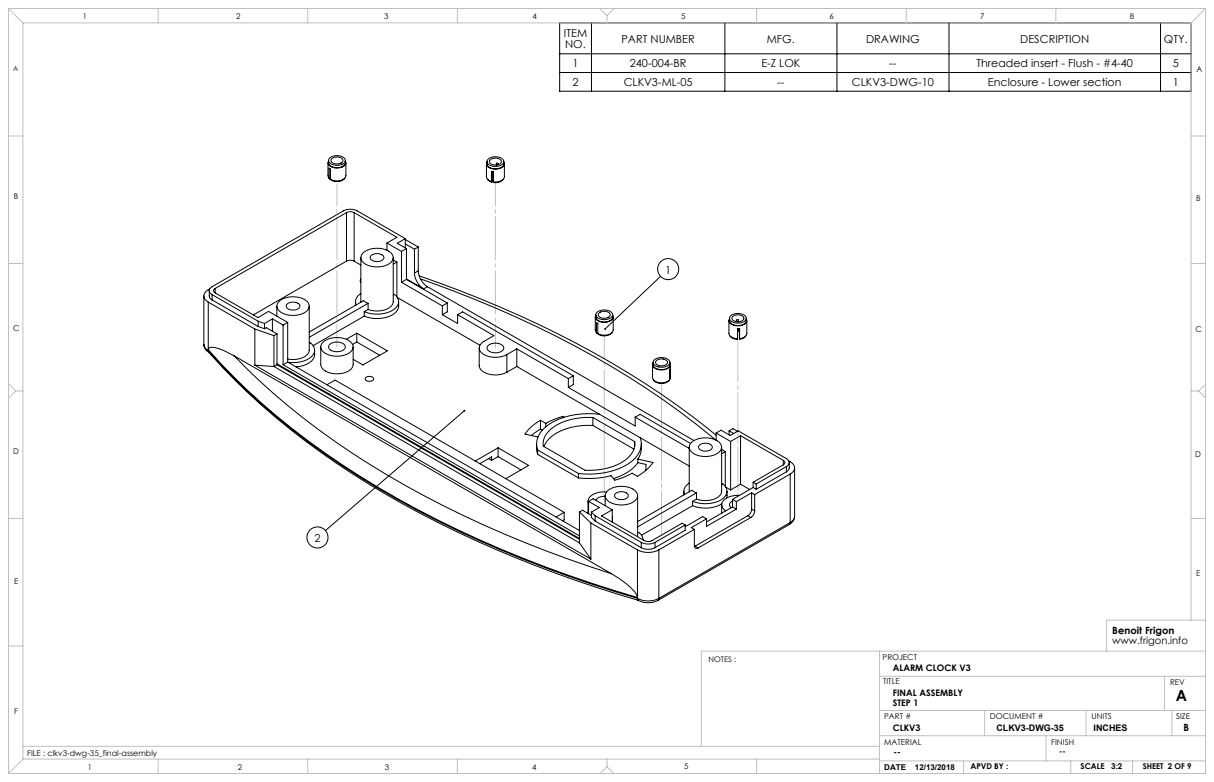
[picture p65: page 2]
SHEET 2 OF 9; ALARM CLOCK V3; FINAL ASSEMBLY; PART #; DOCUMENT #; UNITS; SCALE 3:2; NOTES :; STEP 1

ITEM NO. | PART NUMBER | MFG. | DRAWING | DESCRIPTION | QTY.

1 | 240-004-BR | E-Z LOK | -- | Threaded insert - Flush - #4-40 | 5
2 | CLKV3-ML-05 | -- | CLKV3-DWG-10 | Enclosure - Lower section | 1

Benoit Frigon
www.frigon.info

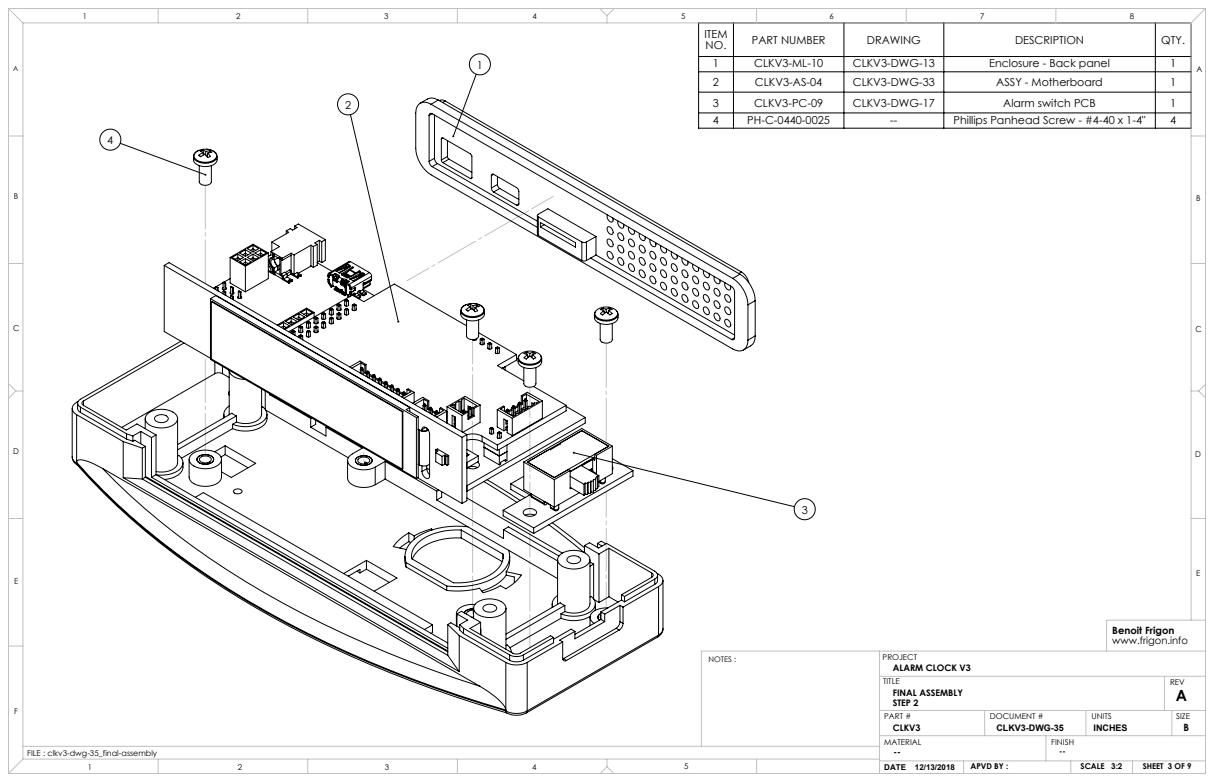
[picture p66: page 3]
SHEET 3 OF 9; ALARM CLOCK V3; FINAL ASSEMBLY; PART #; DOCUMENT #; UNITS; NOTES :; STEP 2

NO. | PART NUMBER | DRAWING | DESCRIPTION | QTY.
1 | CLKV3-ML-10 | CLKV3-DWG-13 | Enclosure - Back panel | 1
2 | CLKV3-AS-04 | CLKV3-DWG-33 | ASSY - Motherboard | 1
3 | CLKV3-PC-09 | CLKV3-DWG-17 | Alarm switch PCB | 1
4 | PH-C-0440-0025 | -- | Phillips Panhead Screw - #4-40 x 1-4" | 4

Benoit Frigon
www.frigon.info

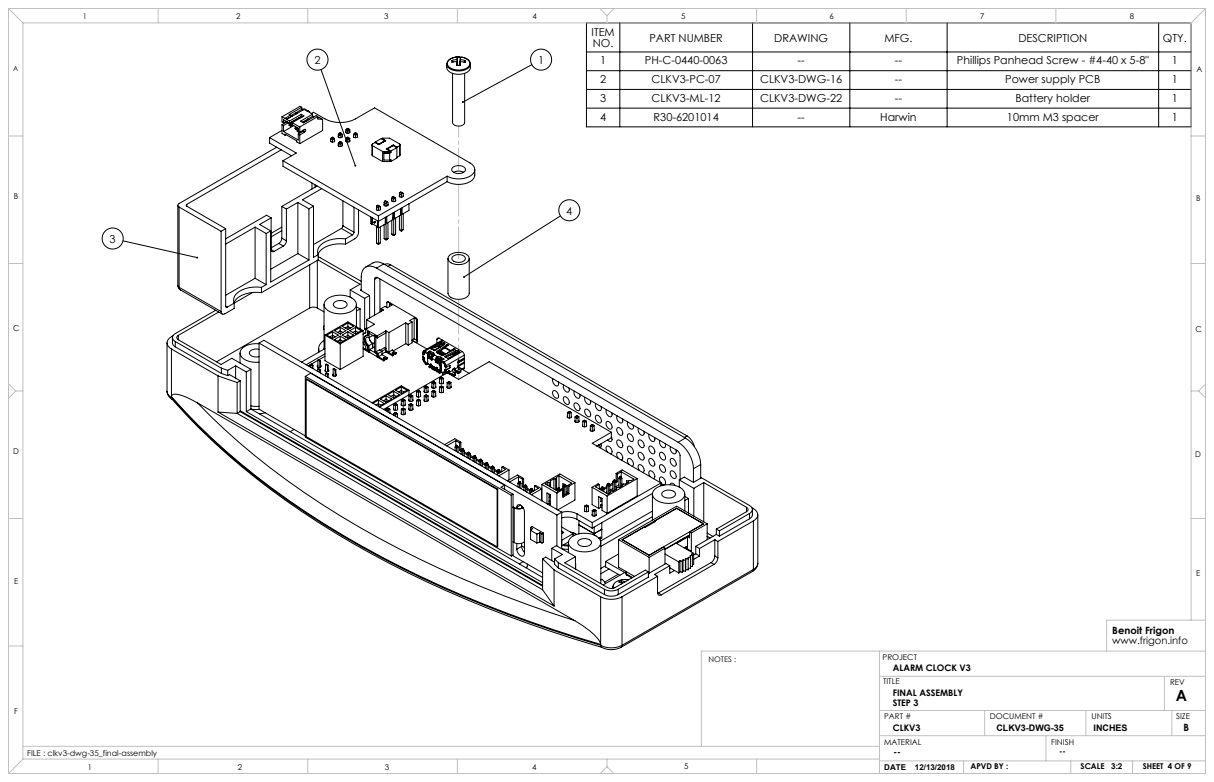
[picture p67: page 4]
SHEET 4 OF 9; ALARM CLOCK V3; FINAL ASSEMBLY; PART #; DOCUMENT #; UNITS; NOTES :; STEP 3

NO. | PART NUMBER | DRAWING | MFG. | DESCRIPTION | QTY.
1 | PH-C-0440-0063 | -- | -- | Phillips Panhead Screw - #4-40 x 5-8" | 1
2 | CLKV3-PC-07 | CLKV3-DWG-16 | -- | Power supply PCB | 1
3 | CLKV3-ML-12 | CLKV3-DWG-22 | -- | Battery holder | 1
4 | R30-6201014 | -- | Harwin | 10mm M3 spacer | 1

Benoit Frigon
www.frigon.info

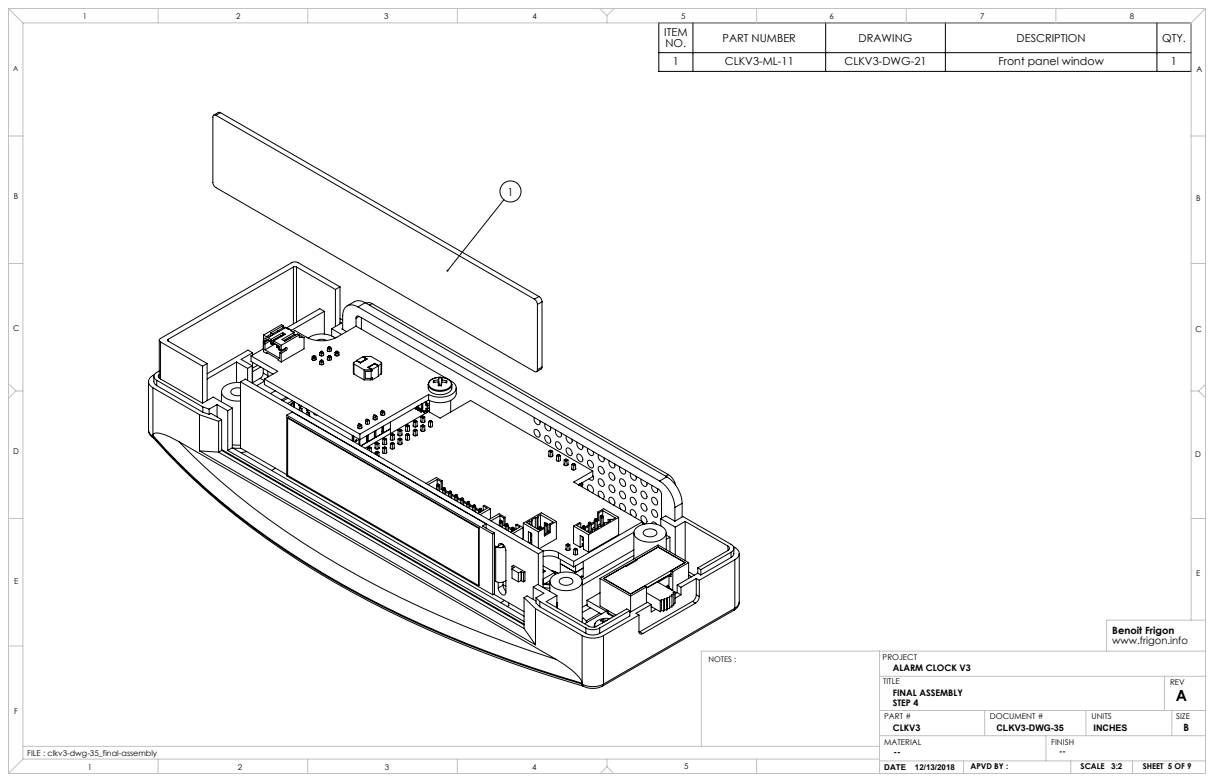
[picture p68: page 5]
SHEET 5 OF 9; ALARM CLOCK V3; FINAL ASSEMBLY; PART #; DOCUMENT #; UNITS; NOTES :; STEP 4

NO. | PART NUMBER | DRAWING | DESCRIPTION | QTY.
1 | CLKV3-ML-11 | CLKV3-DWG-21 | Front panel window | 1

Benoit Frigon
www.frigon.info

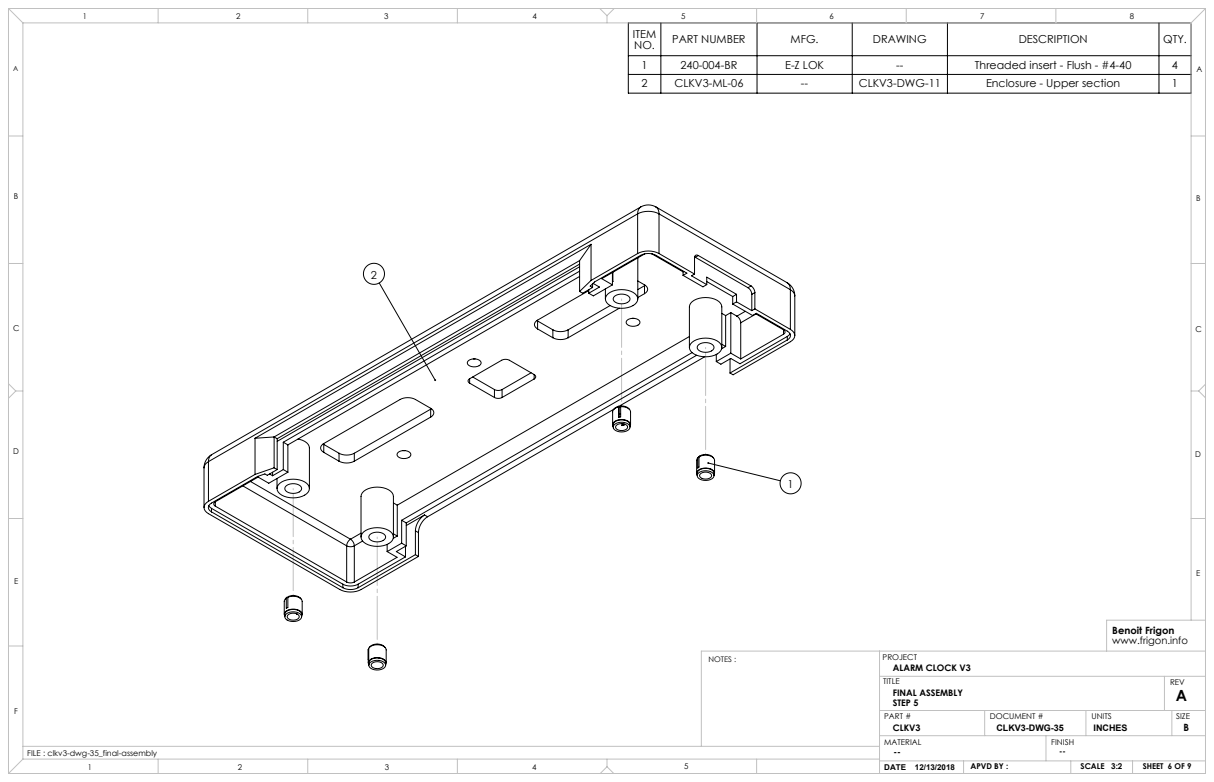
[picture p69: page 6]
SHEET 6 OF 9; ALARM CLOCK V3; FINAL ASSEMBLY; PART #; DOCUMENT #; UNITS; NOTES :; STEP 5

NO. | PART NUMBER | MFG. | DRAWING | DESCRIPTION | QTY.
1 | 240-004-BR | E-Z LOK | -- | Threaded insert - Flush - #4-40 | 4
2 | CLKV3-ML-06 | -- | CLKV3-DWG-11 | Enclosure - Upper section | 1

Benoit Frigon
www.frigon.info

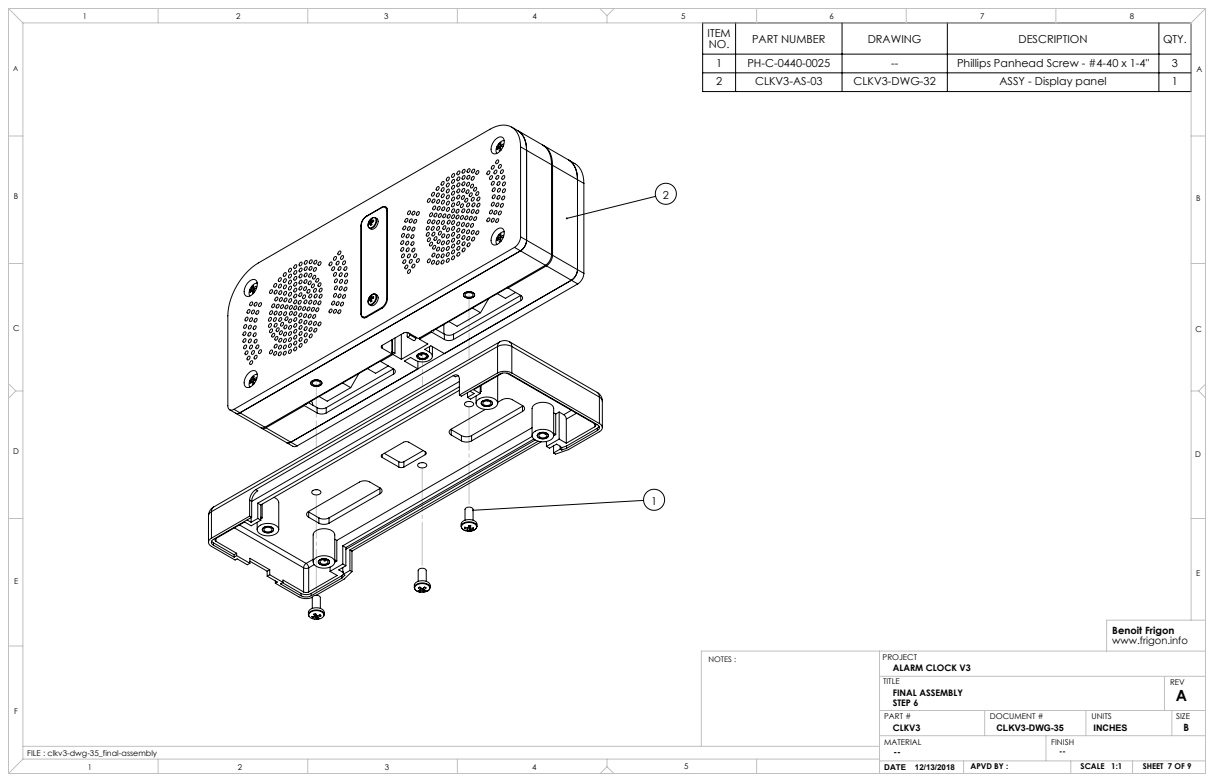
[picture p70: page 7]
SHEET 7 OF 9; ALARM CLOCK V3; FINAL ASSEMBLY; PART #; DOCUMENT #; UNITS; SCALE 1:1; NOTES :; STEP 6

NO. | PART NUMBER | DRAWING | DESCRIPTION | QTY.
1 | PH-C-0440-0025 | -- | Phillips Panhead Screw - #4-40 x 1-4" | 3
2 | CLKV3-AS-03 | CLKV3-DWG-32 | ASSY - Display panel | 1

Benoit Frigon
www.frigon.info

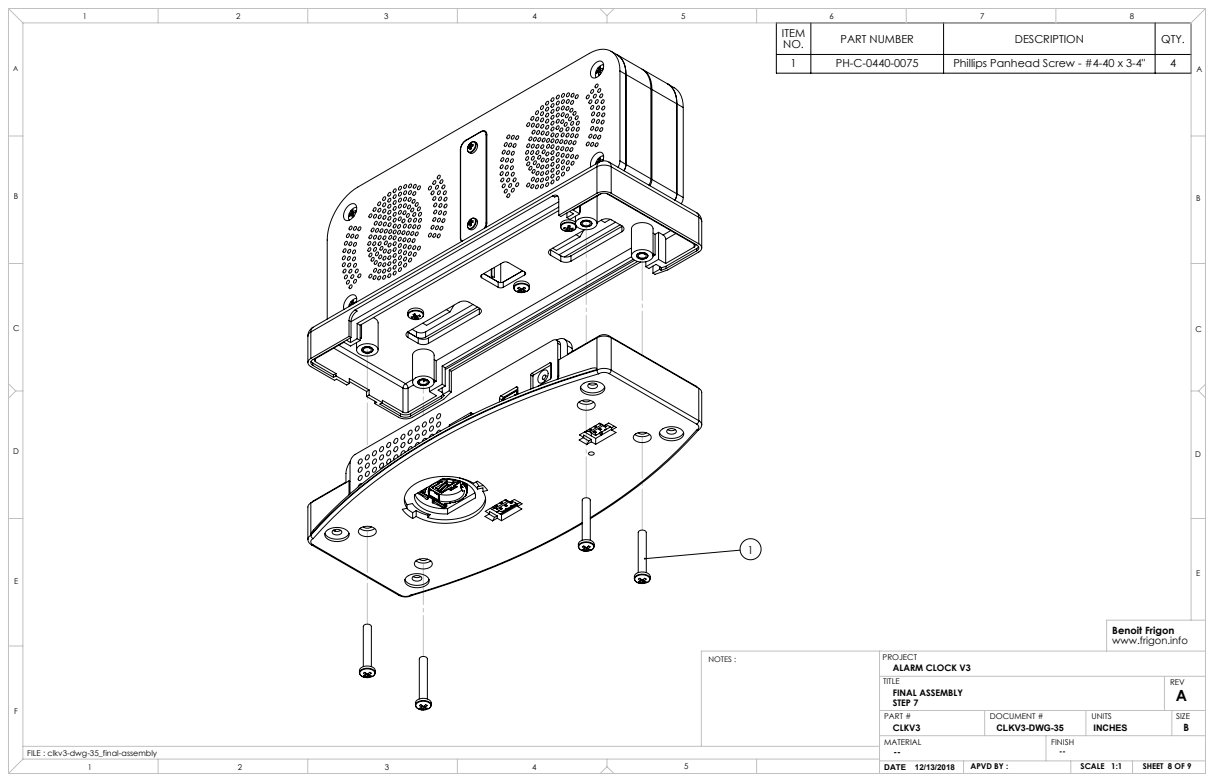
[picture p71: page 8]
SHEET 8 OF 9; ALARM CLOCK V3; FINAL ASSEMBLY; PART #; DOCUMENT #; UNITS; SCALE 1:1; NOTES :; STEP 7

NO. | PART NUMBER | DESCRIPTION | QTY.
1 | PH-C-0440-0075 | Phillips Panhead Screw - #4-40 x 3-4" | 4

Benoit Frigon
www.frigon.info

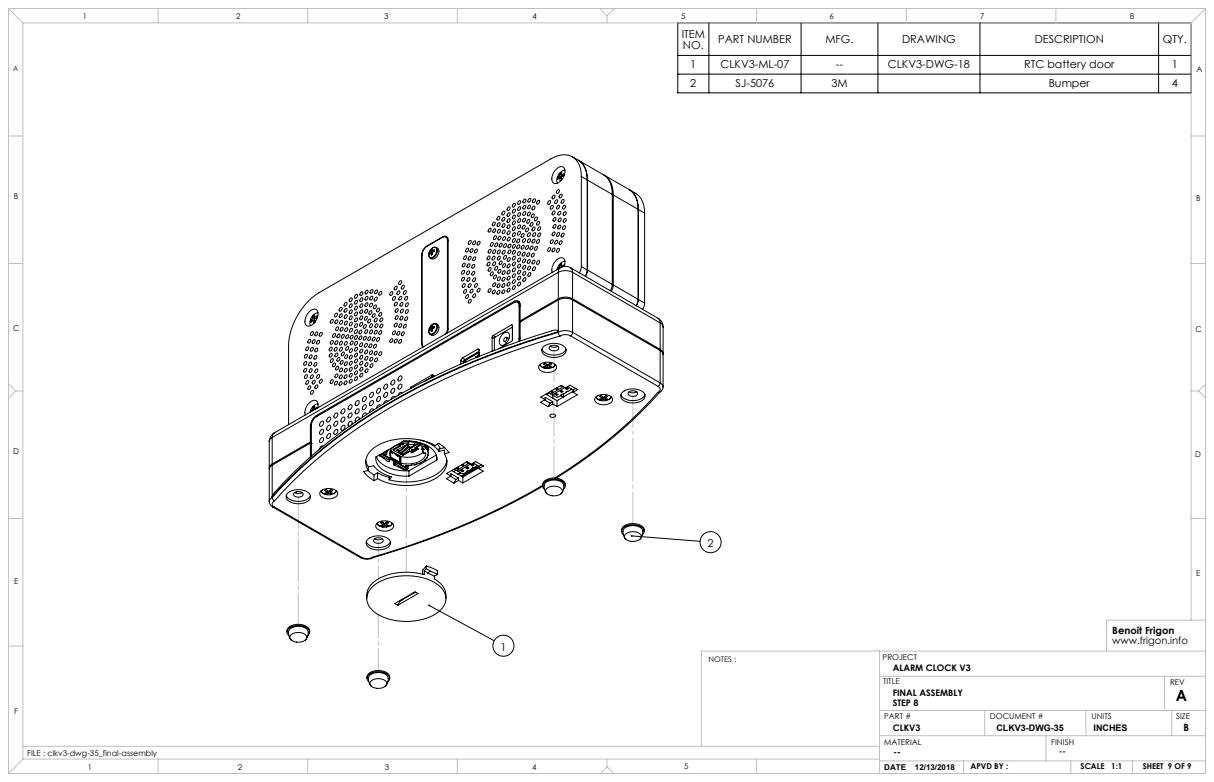
[picture p72: page 9]
SHEET 9 OF 9; ALARM CLOCK V3; FINAL ASSEMBLY; PART #; DOCUMENT #; UNITS; SCALE 1:1; NOTES :; STEP 8

NO. | PART NUMBER | MFG. | DRAWING | DESCRIPTION | QTY.
1 | CLKV3-ML-07 | -- | CLKV3-DWG-18 | RTC battery door | 1
2 | SJ-5076 | 3M | | Bumper | 4

Benoit Frigon
www.frigon.info
