bfrigon/alarm-clock-v3/pictures/display-panel/display-frame-assembly.jpg

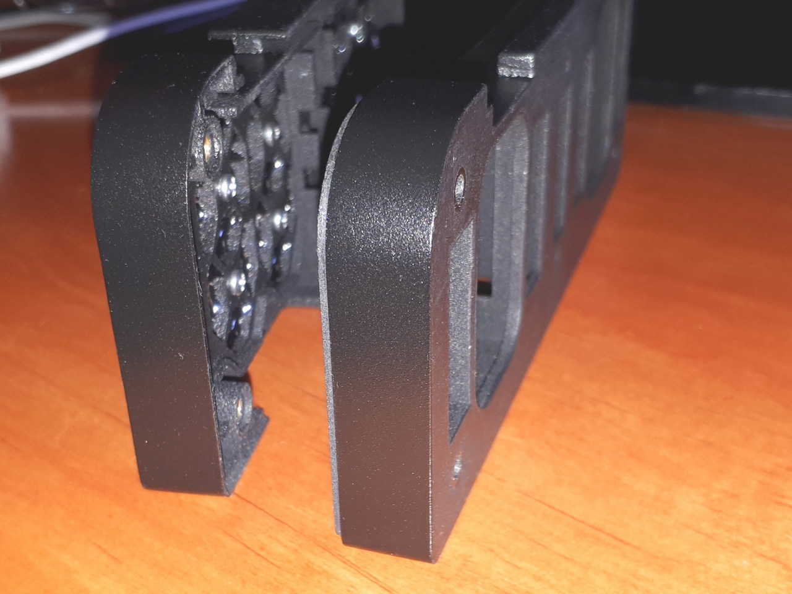
pictures/display-panel/display-frame-assembly.jpg
