bfrigon/alarm-clock-v3/pictures/display-panel/display-panel-assembled.jpg

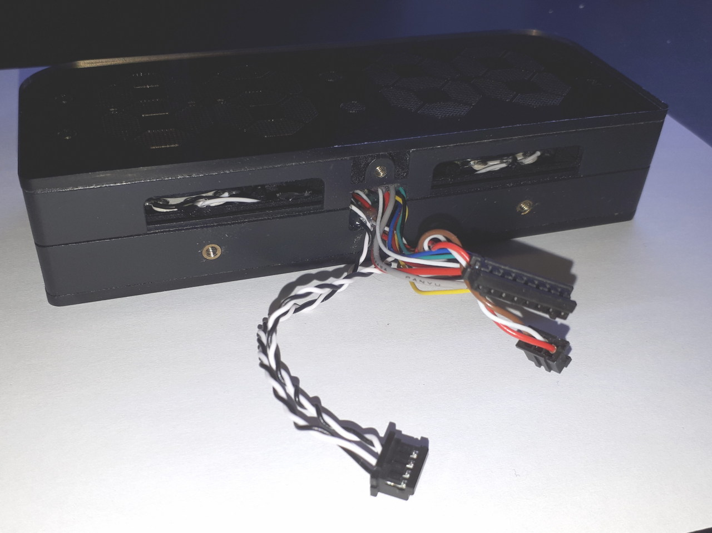
pictures/display-panel/display-panel-assembled.jpg
