bfrigon/alarm-clock-v3/pictures/display-panel/frame-back-assembled.jpg

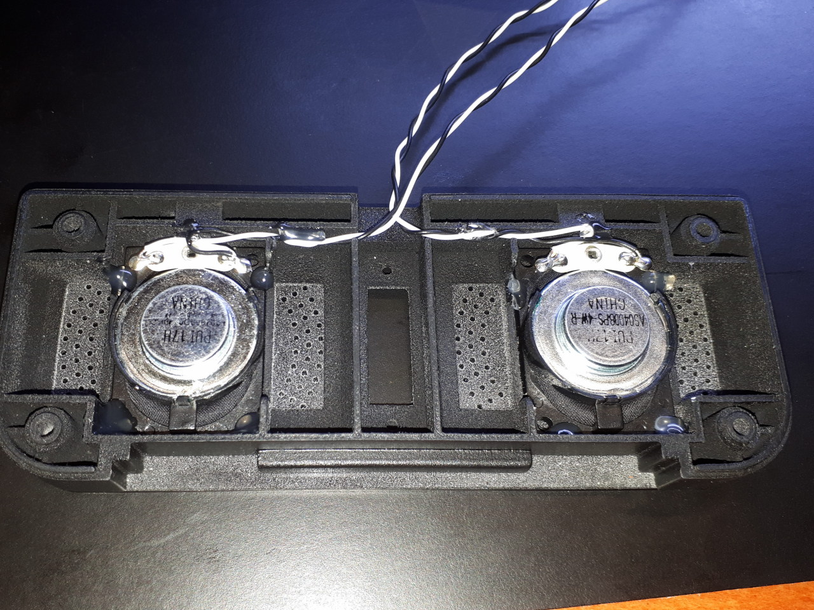
pictures/display-panel/frame-back-assembled.jpg
