bfrigon/alarm-clock-v3/pictures/display-panel/frame-back-cover-assembly-glue.jpg

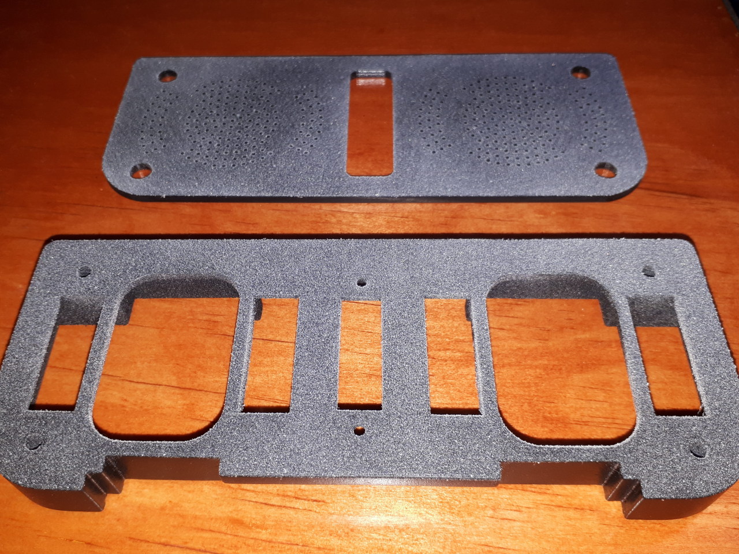
pictures/display-panel/frame-back-cover-assembly-glue.jpg
