bfrigon/alarm-clock-v3/pictures/display-panel/frame-front-assembled.jpg

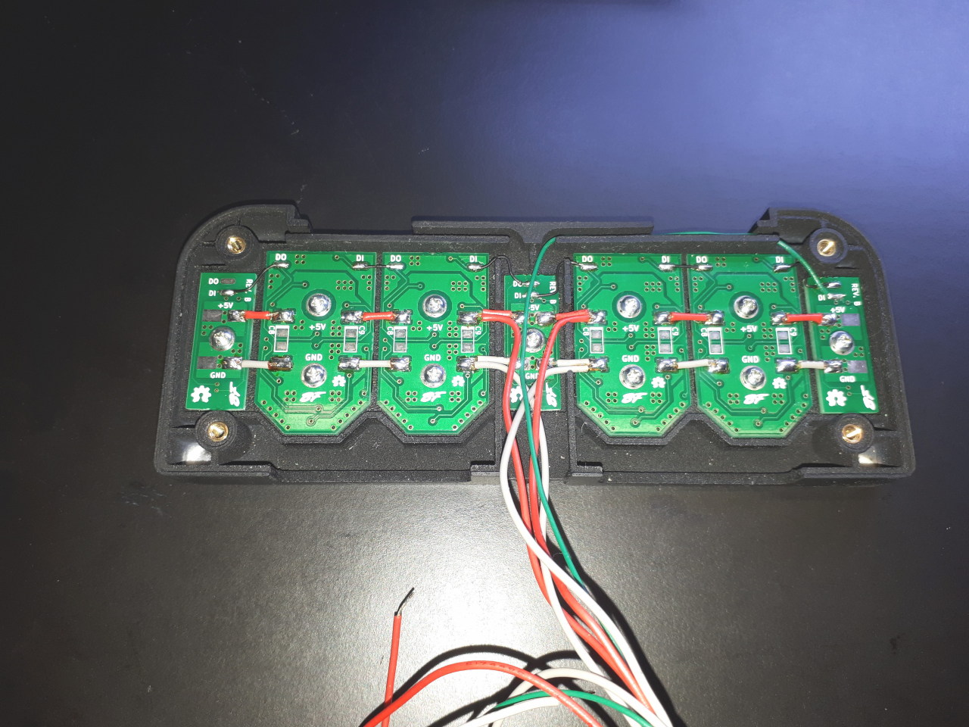
pictures/display-panel/frame-front-assembled.jpg
