bfrigon/alarm-clock-v3/pictures/display-panel/frame-front-assembly-glue.jpg

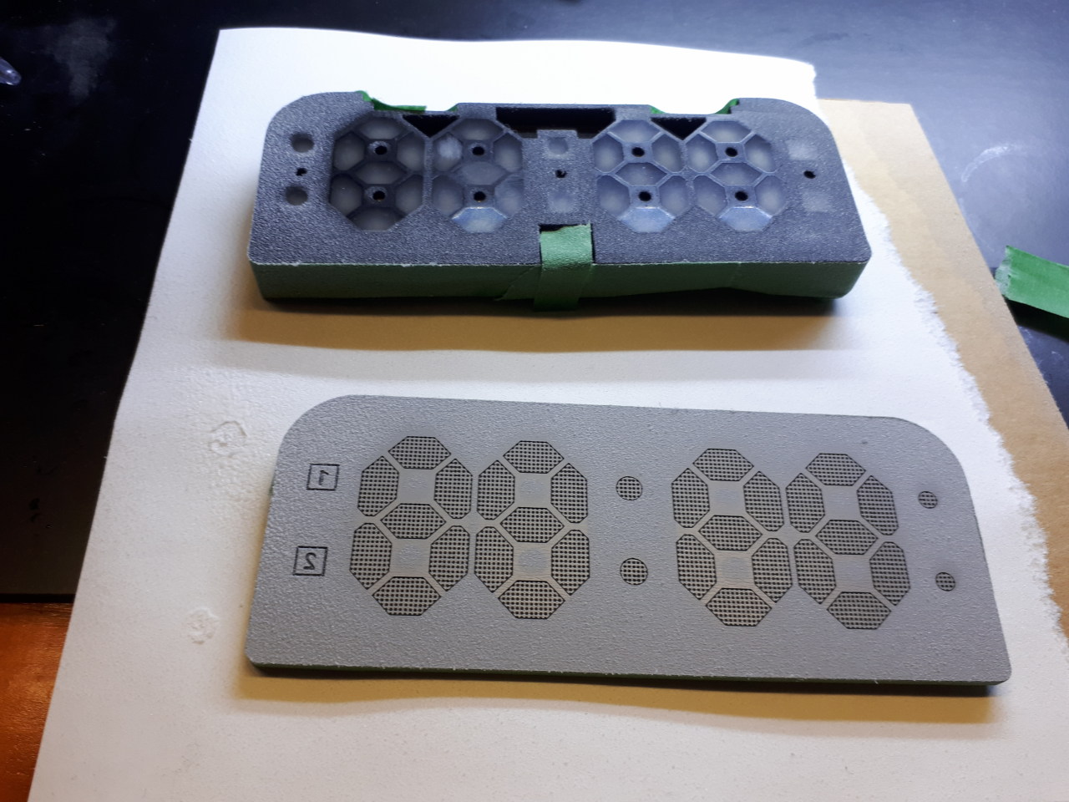
pictures/display-panel/frame-front-assembly-glue.jpg
