bfrigon/alarm-clock-v3/pictures/display-panel/rgb-digit-pcb-assembled.jpg

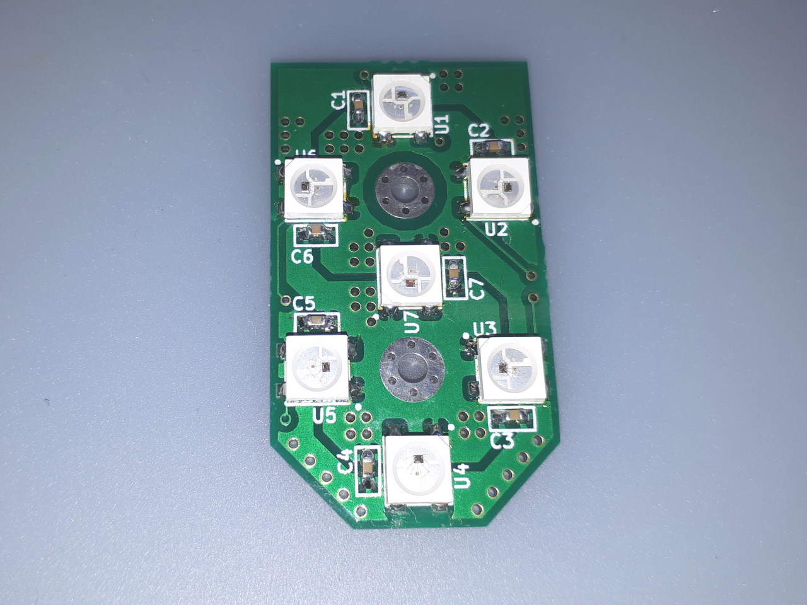
pictures/display-panel/rgb-digit-pcb-assembled.jpg
