bfrigon/alarm-clock-v3/pictures/enclosure/threaded-insert-installed.jpg

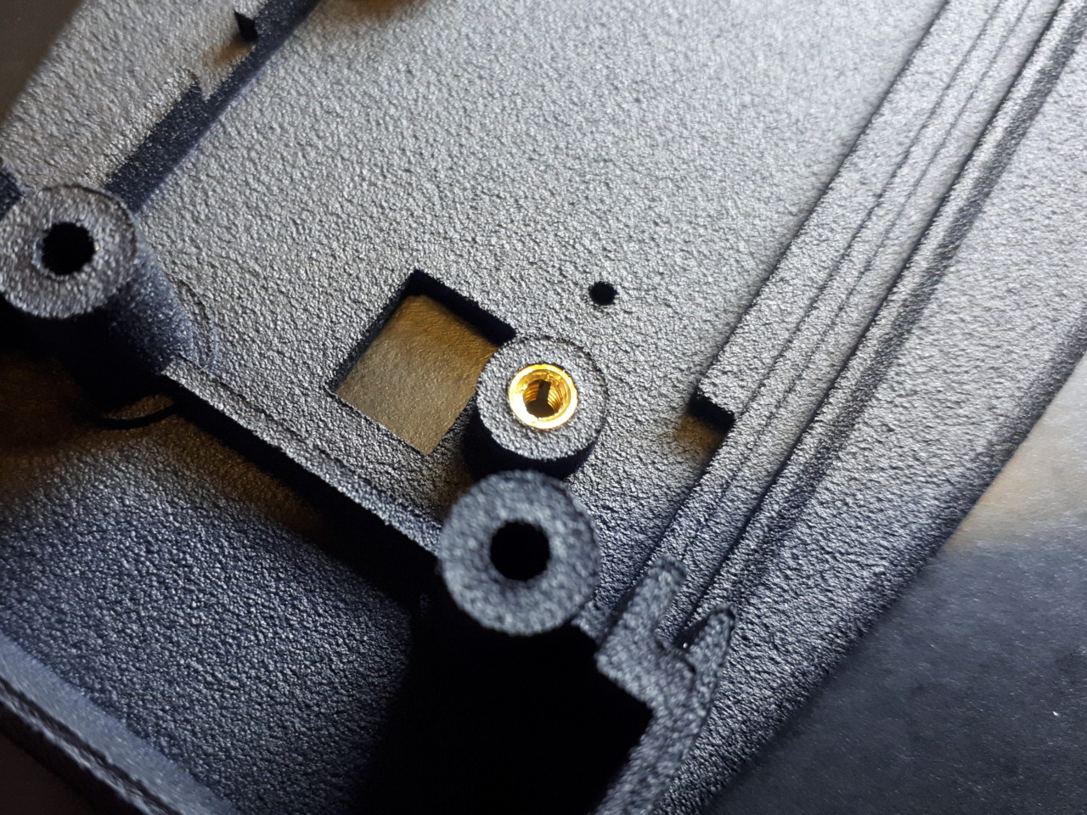
pictures/enclosure/threaded-insert-installed.jpg
