bfrigon/alarm-clock-v3/pictures/final-assembly/assembly-final.jpg

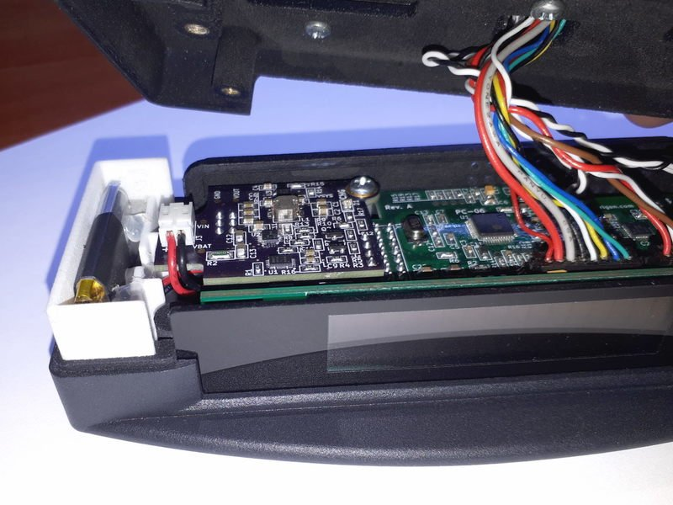
pictures/final-assembly/assembly-final.jpg
