bfrigon/alarm-clock-v3/pictures/front-panel/front-panel-lcd-installation.jpg

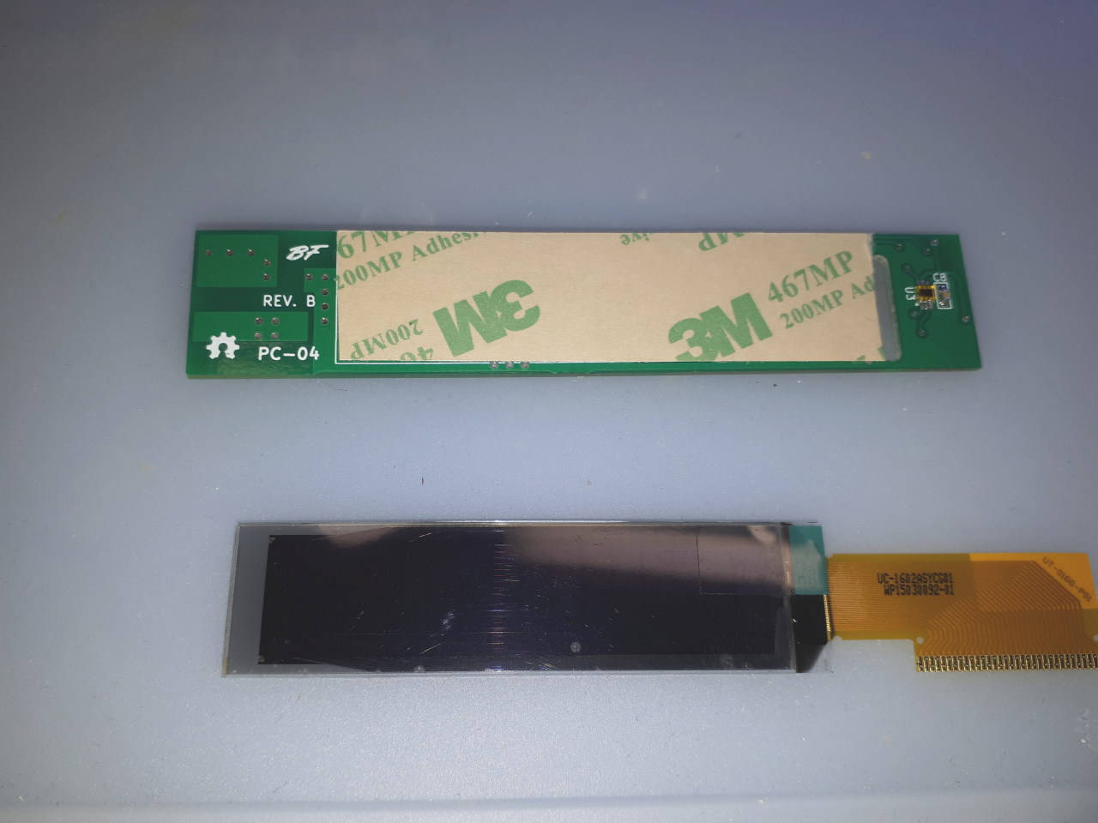
pictures/front-panel/front-panel-lcd-installation.jpg
