bfrigon/alarm-clock-v3/pictures/front-panel/front-panel-lcd-installed.jpg

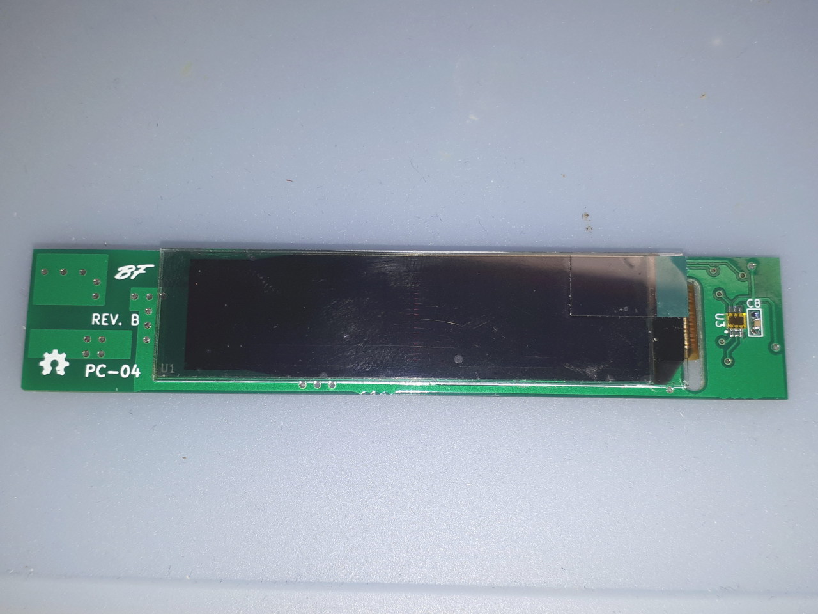
pictures/front-panel/front-panel-lcd-installed.jpg
