bfrigon/alarm-clock-v3/pictures/front-panel/front-panel-pcb-assembled.jpg

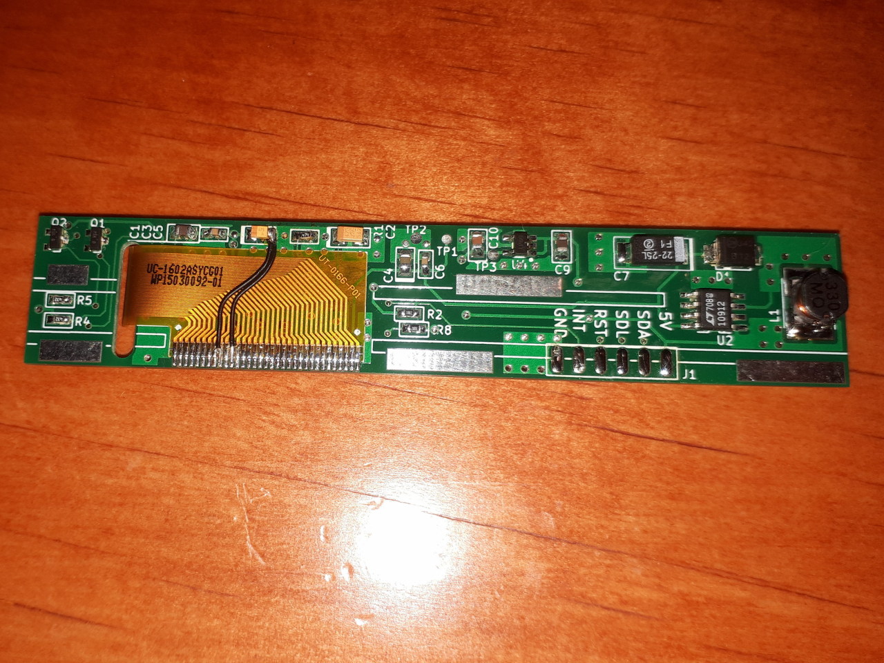
pictures/front-panel/front-panel-pcb-assembled.jpg
