bfrigon/alarm-clock-v3/pictures/motherboard/daughterboard-assembled-top.jpg

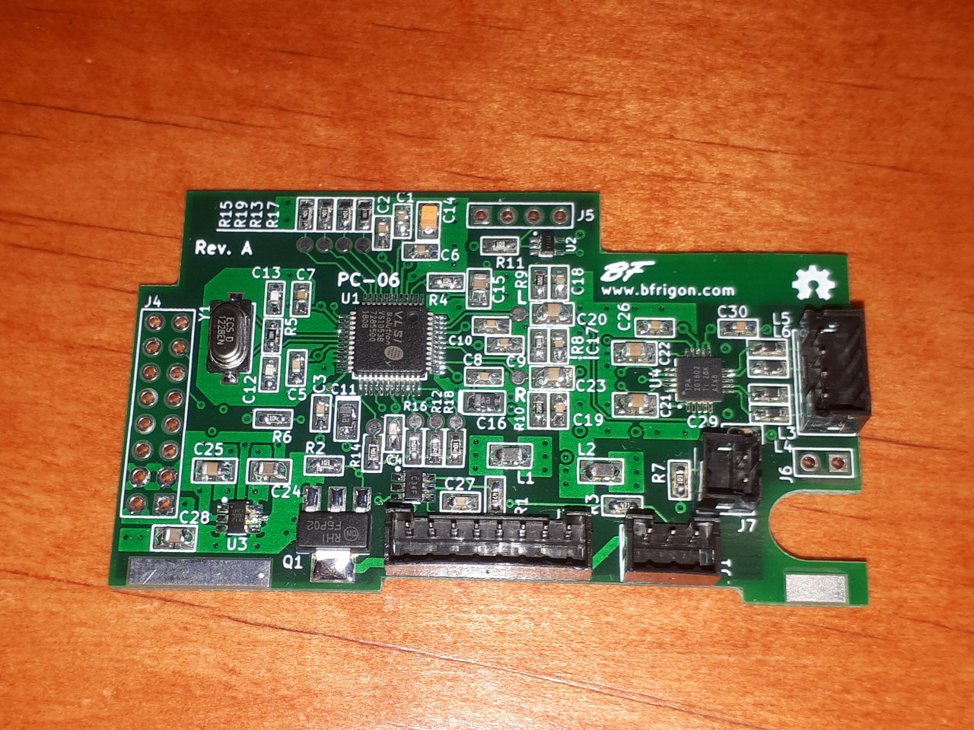
pictures/motherboard/daughterboard-assembled-top.jpg
