bfrigon/alarm-clock-v3/pictures/motherboard/motherboard-final-assembly-back.jpg

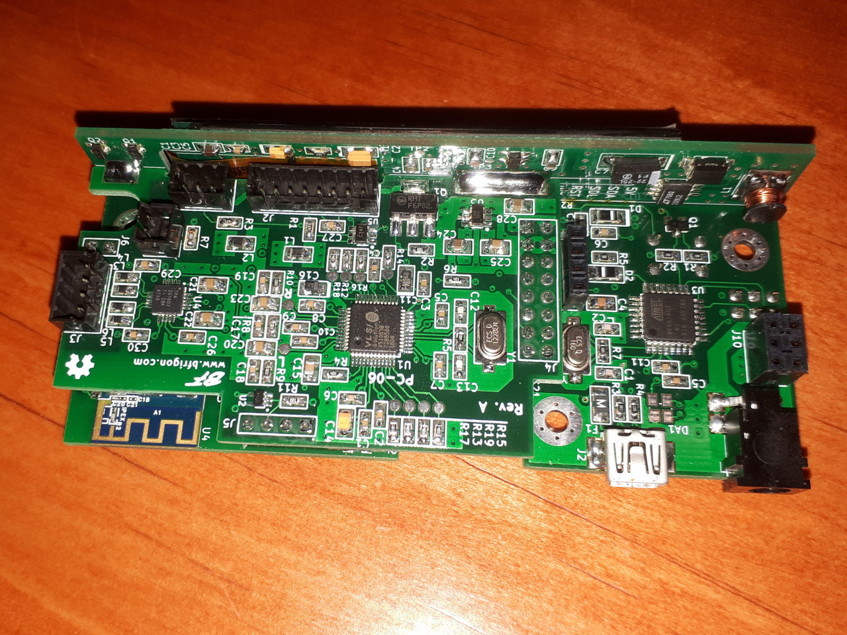
pictures/motherboard/motherboard-final-assembly-back.jpg
