bfrigon/alarm-clock-v3/pictures/psu/battery-holder-installed.jpg

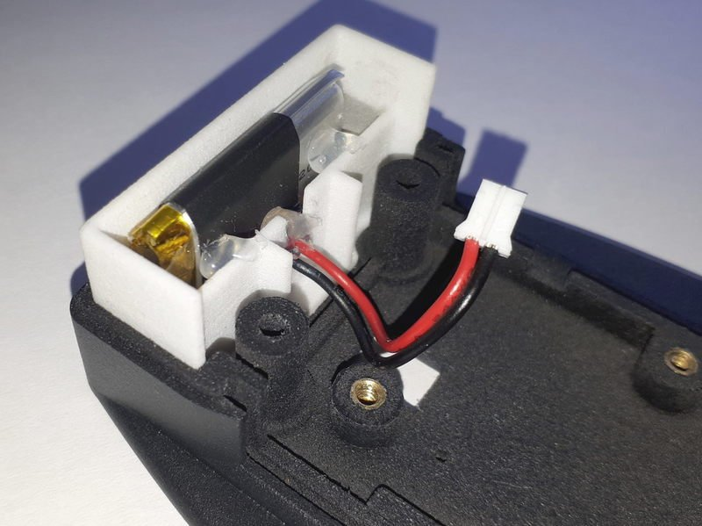
pictures/psu/battery-holder-installed.jpg
