bfrigon/alarm-clock-v3/pictures/psu/psu-pcb-assembled.jpg

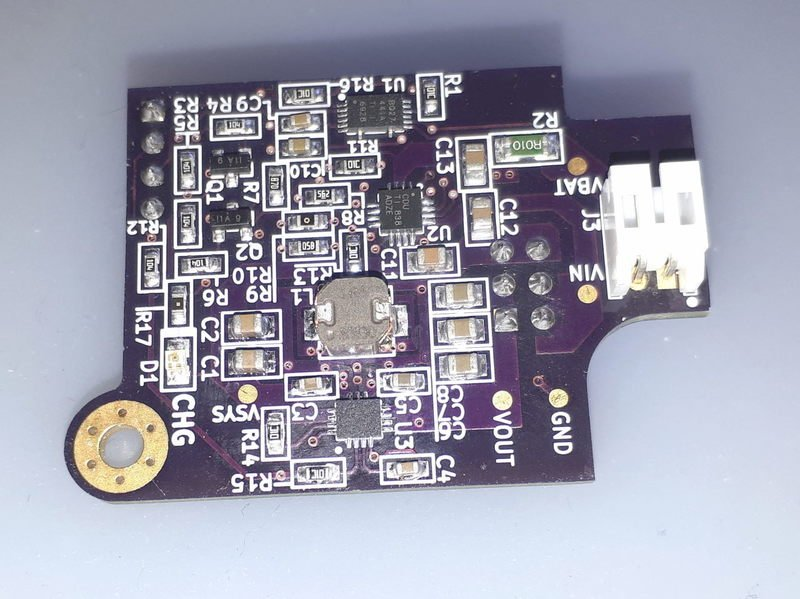
pictures/psu/psu-pcb-assembled.jpg
