bfrigon/alarm-clock-v3/pictures/psu/psu-pcb-installed.jpg

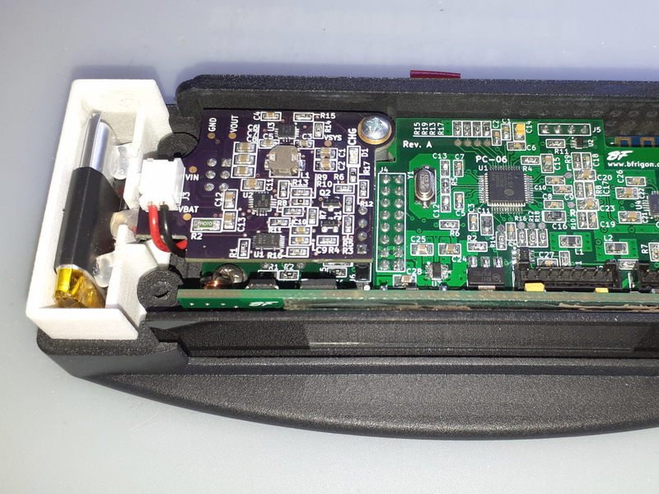
pictures/psu/psu-pcb-installed.jpg
