bfrigon/alarm-clock-v3/pictures/psu/psu-pcb-solder-paste.jpg

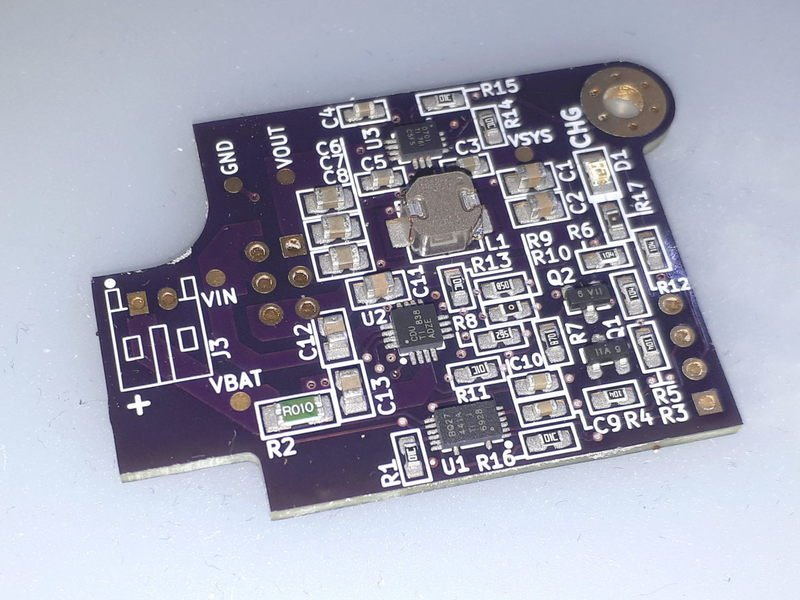
pictures/psu/psu-pcb-solder-paste.jpg
