bfrigon/alarm-clock-v3/drawings/mechanical/clkv3-dwg-12_front-panel-pcb.pdf

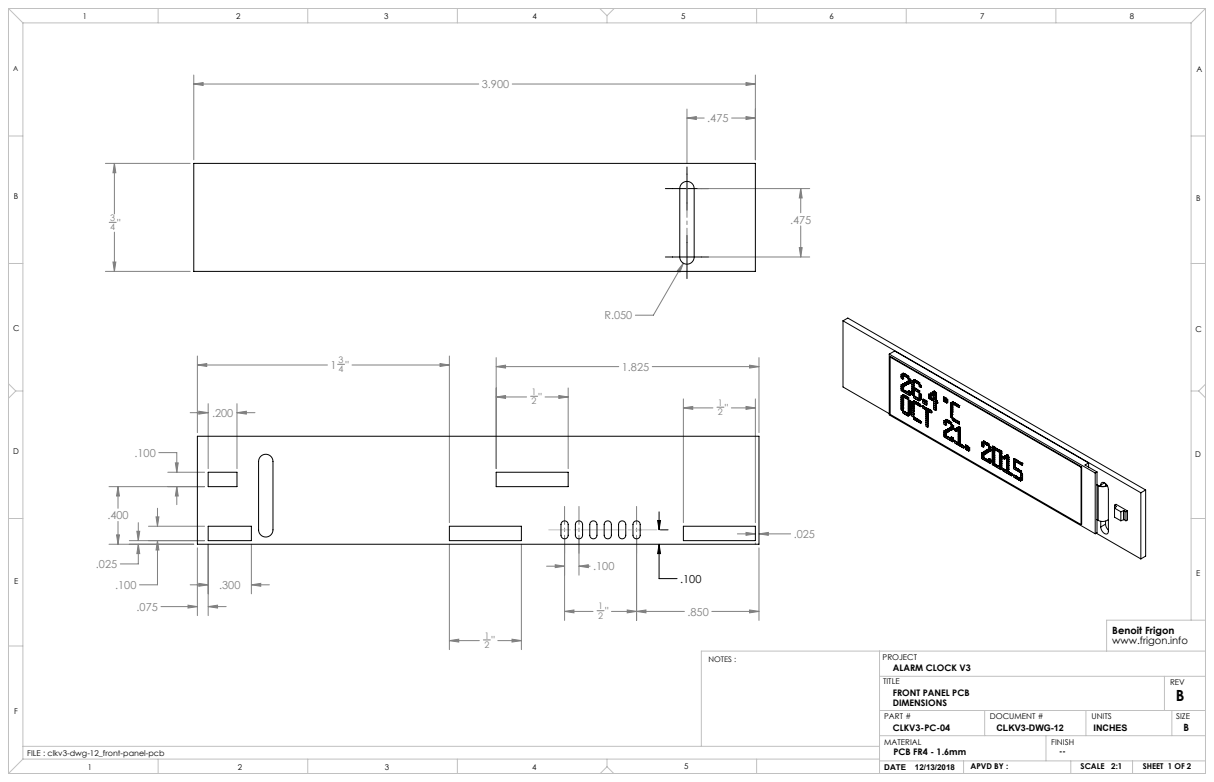
[picture p113: page 1]
SHEET 1 OF 2; ALARM CLOCK V3; FRONT PANEL PCB; PART #; DOCUMENT #; UNITS; DATE 12/13/2018; SCALE 2:1; PCB FR4 - 1.6mm; NOTES :; APVD BY :

Benoit Frigon
www.frigon.info

FILE : clkv3-dwg-12_front-panel-pcb

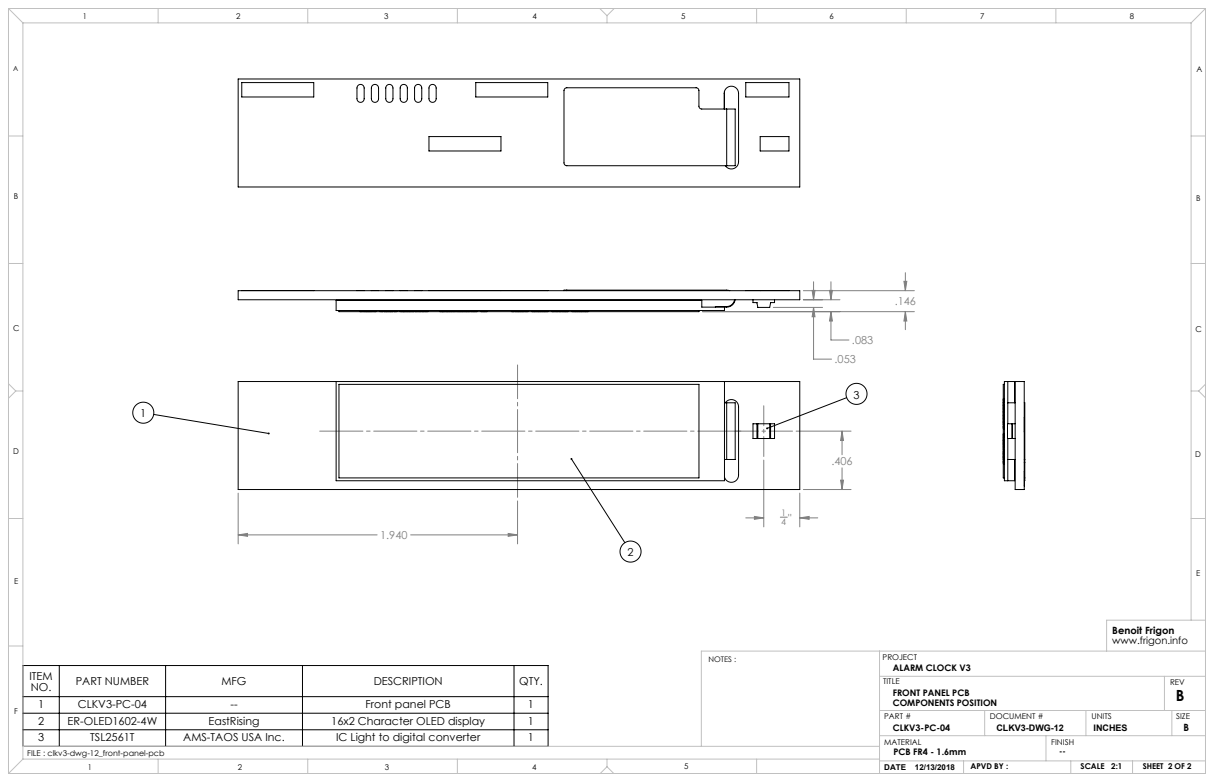
[picture p114: page 2]
SHEET 2 OF 2; ALARM CLOCK V3; FRONT PANEL PCB; PART #; DOCUMENT #; UNITS; DATE 12/13/2018; SCALE 2:1; PCB FR4 - 1.6mm; NOTES :; COMPONENTS POSITION; APVD BY :

Benoit Frigon
www.frigon.info

ITEM NO. | PART NUMBER | MFG | DESCRIPTION | QTY.
1 | CLKV3-PC-04 | -- | Front panel PCB | 1
2 | ER-OLED1602-4W | EastRising | 16x2 Character OLED display | 1
3 | TSL2561T | AMS-TAOS USA Inc. | IC Light to digital converter | 1

FILE : clkv3-dwg-12_front-panel-pcb
