bfrigon/alarm-clock-v3/drawings/mechanical/clkv3-dwg-13_enclosure-back-panel.pdf

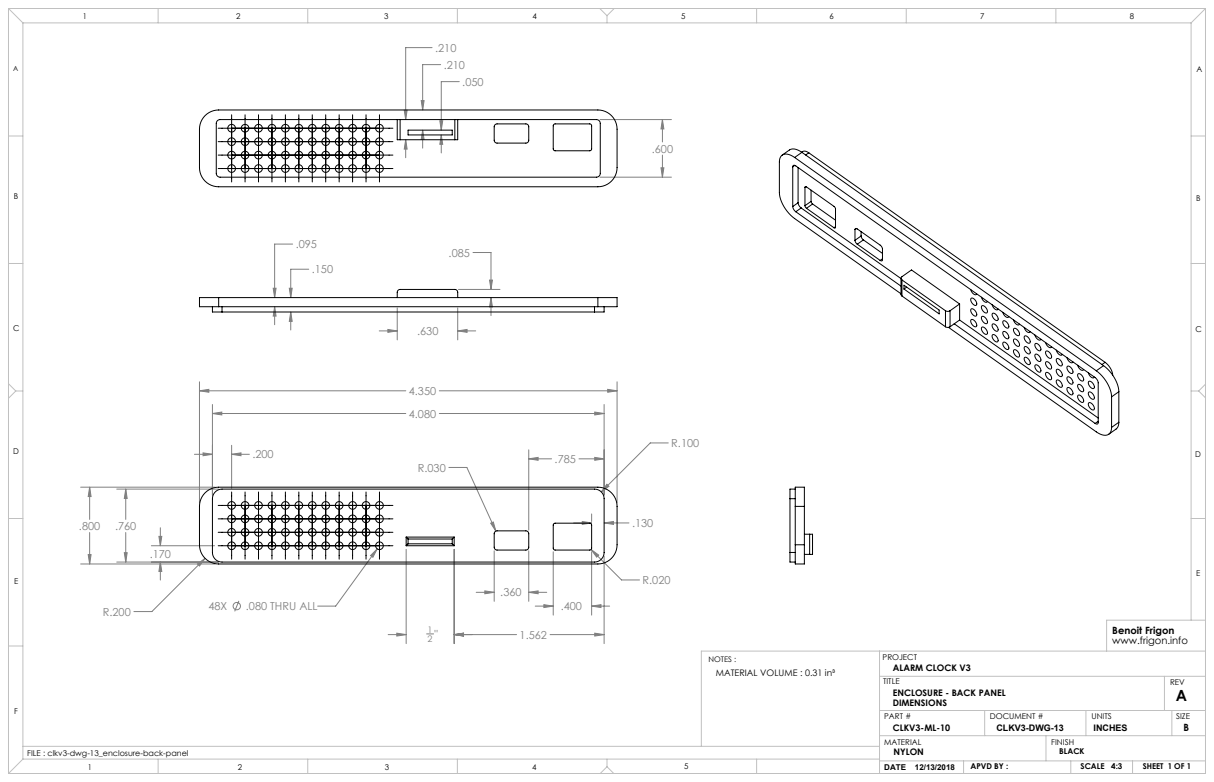
[picture p115: page 1]
.080 THRU ALL; SHEET 1 OF 1; ALARM CLOCK V3; ENCLOSURE - BACK PANEL; PART #; DOCUMENT #; UNITS; DATE 12/13/2018; SCALE 4:3; APVD BY :

Benoit Frigon
www.frigon.info

NOTES :
MATERIAL VOLUME : 0.31 in³

FILE : clkv3-dwg-13_enclosure-back-panel
