bfrigon/alarm-clock-v3/drawings/mechanical/clkv3-dwg-14_motherboard-pcb.pdf

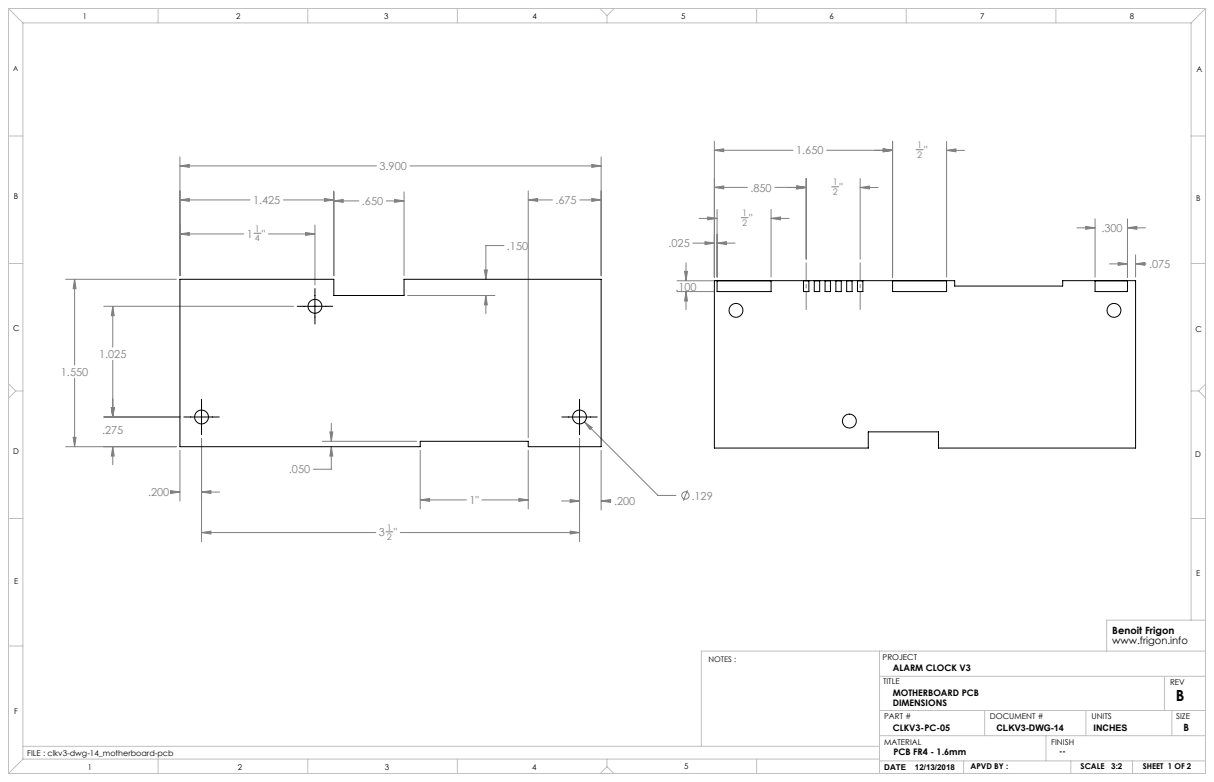
[picture p116: page 1]
SHEET 1 OF 2; ALARM CLOCK V3; MOTHERBOARD PCB; PART #; DOCUMENT #; UNITS; DATE 12/13/2018; SCALE 3:2; PCB FR4 - 1.6mm; NOTES :; APVD BY :

Benoit Frigon
www.frigon.info

FILE : clkv3-dwg-14_motherboard-pcb

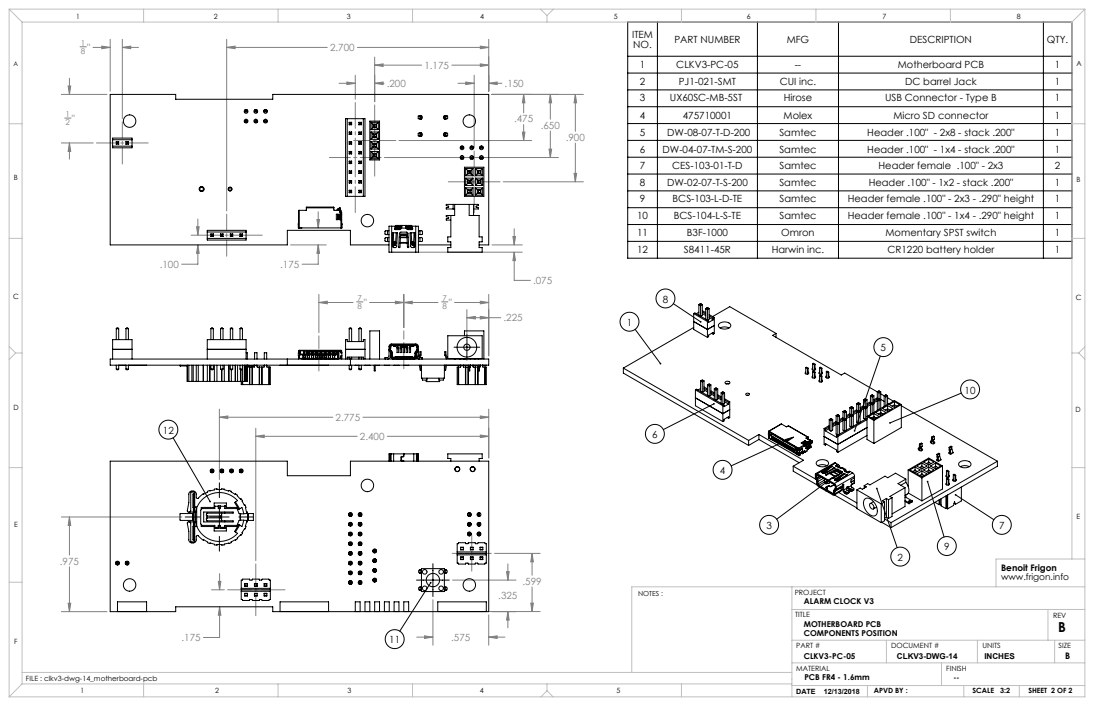
[picture p117: page 2]
SHEET 2 OF 2; ALARM CLOCK V3; MOTHERBOARD PCB; PART #; DOCUMENT #; UNITS; DATE 12/13/2018; SCALE 3:2; PCB FR4 - 1.6mm; NOTES :; COMPONENTS POSITION; APVD BY :

ITEM NO. | PART NUMBER | MFG | DESCRIPTION | QTY.

1 | CLKV3-PC-05 | -- | Motherboard PCB | 1
2 | PJ1-021-SMT | CUI inc. | DC barrel Jack | 1
3 | UX60SC-MB-5ST | Hirose | USB Connector - Type B | 1
4 | 475710001 | Molex | Micro SD connector | 1
5 | DW-08-07-T-D-200 | Samtec | Header .100" - 2x8 - stack .200" | 1
6 | DW-04-07-TM-S-200 | Samtec | Header .100" - 1x4 - stack .200" | 1
7 | CES-103-01-T-D | Samtec | Header female .100" - 2x3 | 2
8 | DW-02-07-T-S-200 | Samtec | Header .100" - 1x2 - stack .200" | 1
9 | BCS-103-L-D-TE | Samtec | Header female .100" - 2x3 - .290" height | 1
10 | BCS-104-L-S-TE | Samtec | Header female .100" - 1x4 - .290" height | 1
11 | B3F-1000 | Omron | Momentary SPST switch | 1
12 | S8411-45R | Harwin inc. | CR1220 battery holder | 1

Benoit Frigon
www.frigon.info

FILE : clkv3-dwg-14_motherboard-pcb
