bfrigon/alarm-clock-v3/drawings/mechanical/clkv3-dwg-15_daughterboard-pcb.pdf

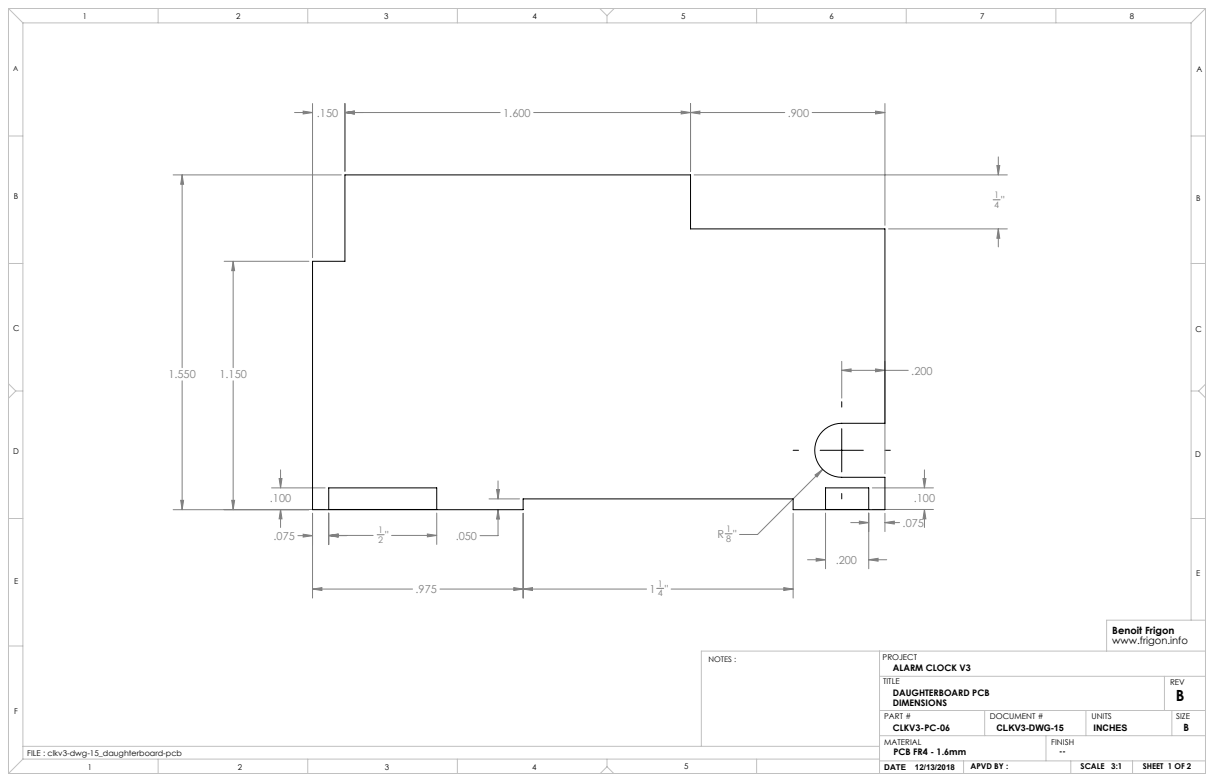
[picture p118: page 1]
SHEET 1 OF 2; ALARM CLOCK V3; DAUGHTERBOARD PCB; PART #; DOCUMENT #; UNITS; DATE 12/13/2018; SCALE 3:1; PCB FR4 - 1.6mm; NOTES :; APVD BY :

Benoit Frigon
www.frigon.info

FILE : clkv3-dwg-15_daughterboard-pcb

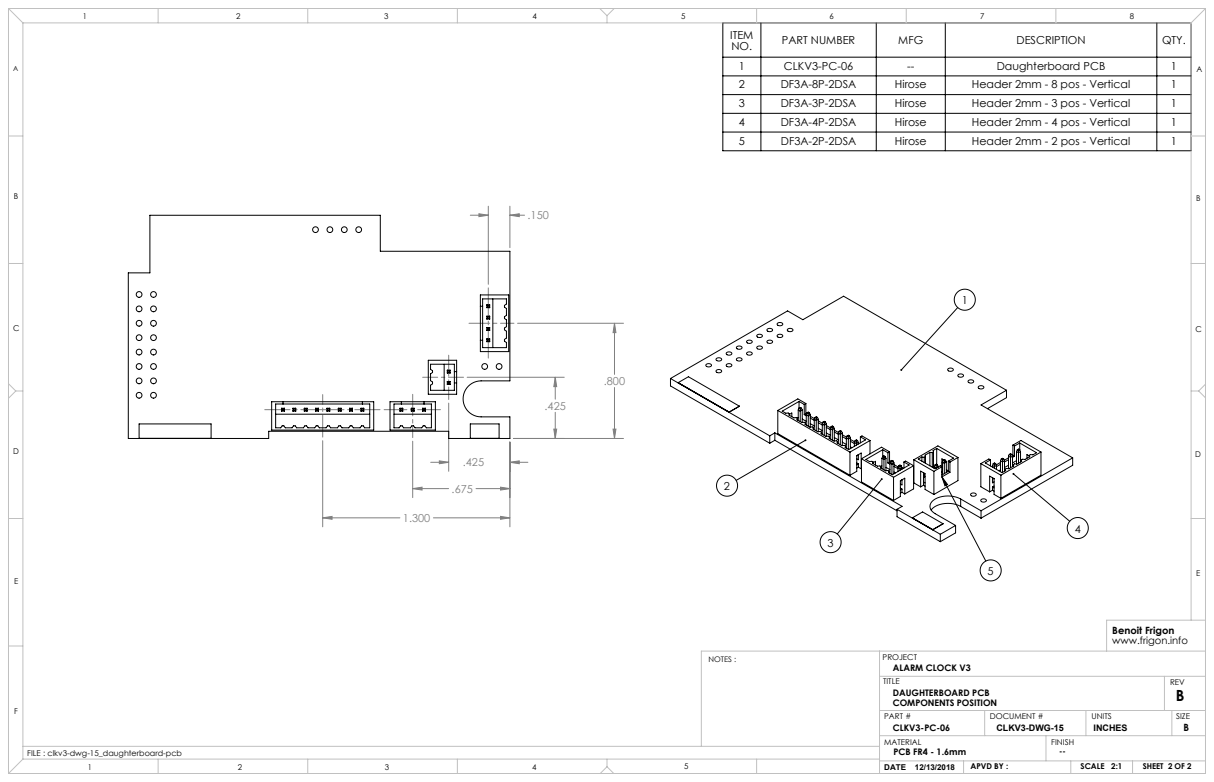
[picture p119: page 2]
SHEET 2 OF 2; ALARM CLOCK V3; DAUGHTERBOARD PCB; PART #; DOCUMENT #; UNITS; DATE 12/13/2018; SCALE 2:1; PCB FR4 - 1.6mm; NOTES :; COMPONENTS POSITION; APVD BY :

ITEM NO. | PART NUMBER | MFG | DESCRIPTION | QTY.

1 | CLKV3-PC-06 | -- | Daughterboard PCB | 1
2 | DF3A-8P-2DSA | Hirose | Header 2mm - 8 pos - Vertical | 1
3 | DF3A-3P-2DSA | Hirose | Header 2mm - 3 pos - Vertical | 1
4 | DF3A-4P-2DSA | Hirose | Header 2mm - 4 pos - Vertical | 1
5 | DF3A-2P-2DSA | Hirose | Header 2mm - 2 pos - Vertical | 1

Benoit Frigon
www.frigon.info

FILE : clkv3-dwg-15_daughterboard-pcb
