bfrigon/alarm-clock-v3/drawings/mechanical/clkv3-dwg-16_psu-pcb.pdf

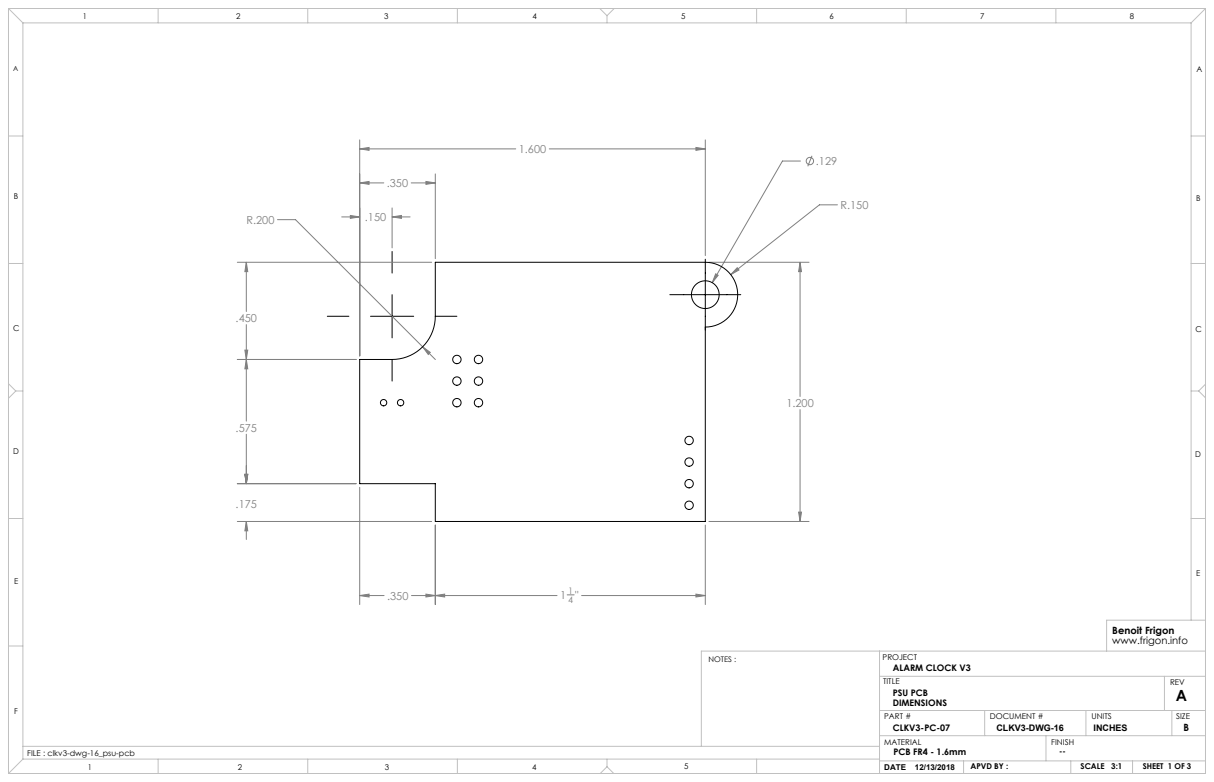
[picture p120: page 1]
SHEET 1 OF 3; ALARM CLOCK V3; PSU PCB; PART #; DOCUMENT #; UNITS; DATE 12/13/2018; SCALE 3:1; PCB FR4 - 1.6mm; NOTES :; APVD BY :

Benoit Frigon
www.frigon.info

FILE : clkv3-dwg-16_psu-pcb

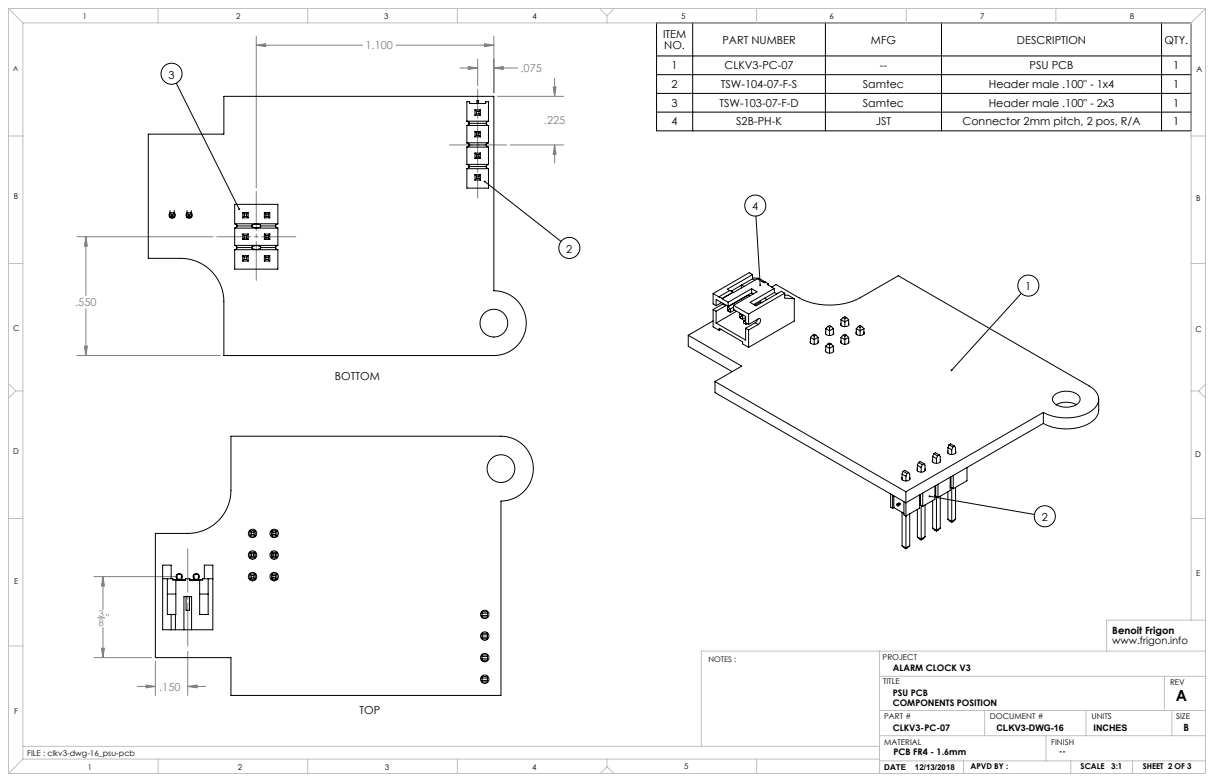
[picture p121: page 2]
SHEET 2 OF 3; ALARM CLOCK V3; PSU PCB; PART #; DOCUMENT #; UNITS; SCALE 3:1; NOTES :; COMPONENTS POSITION

ITEM NO. | PART NUMBER | MFG | DESCRIPTION | QTY.

1 | CLKV3-PC-07 | -- | PSU PCB | 1
2 | TSW-104-07-F-S | Samtec | Header male .100" - 1x4 | 1
3 | TSW-103-07-F-D | Samtec | Header male .100" - 2x3 | 1
4 | S2B-PH-K | JST | Connector 2mm pitch, 2 pos, R/A | 1

Benoit Frigon
www.frigon.info

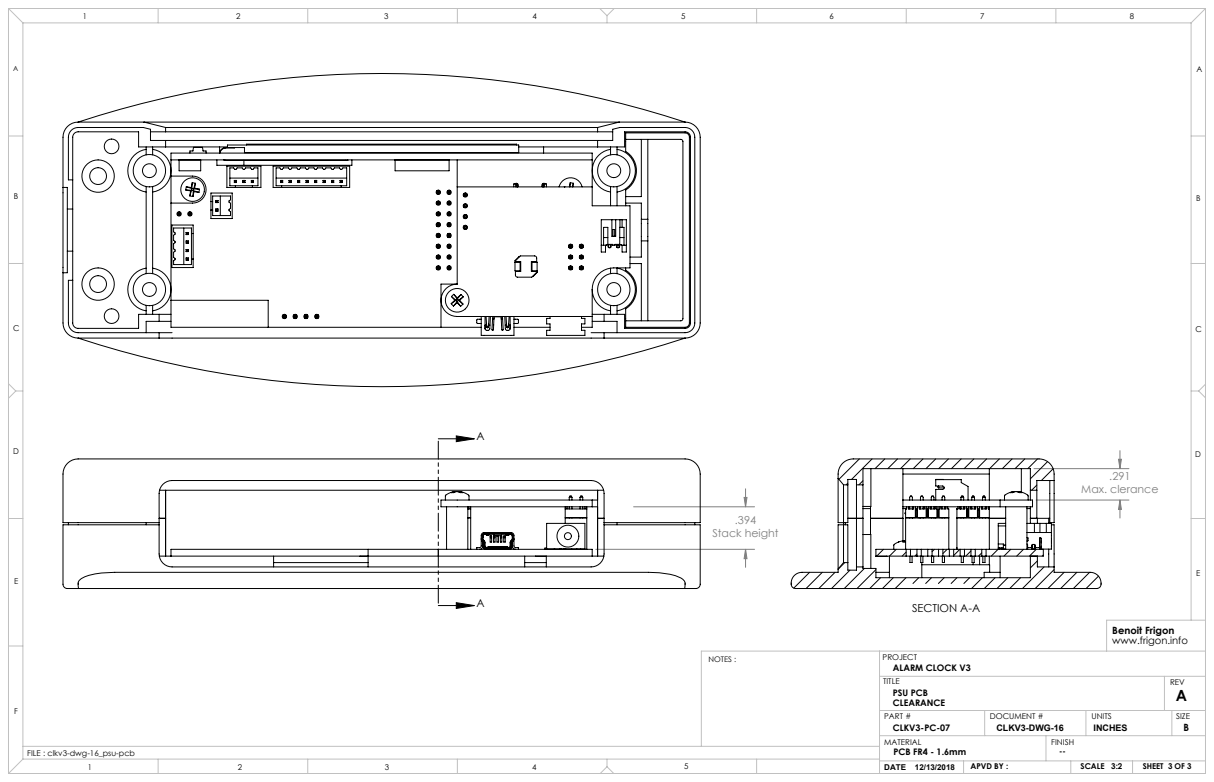
[picture p122: page 3]
Stack height; Max. clerance; SECTION A-A; SHEET 3 OF 3; ALARM CLOCK V3; PSU PCB; PART #; DOCUMENT #; UNITS; SCALE 3:2; NOTES :

Benoit Frigon
www.frigon.info
