bfrigon/alarm-clock-v3/drawings/mechanical/clkv3-dwg-17_alarm-switch-pcb.pdf

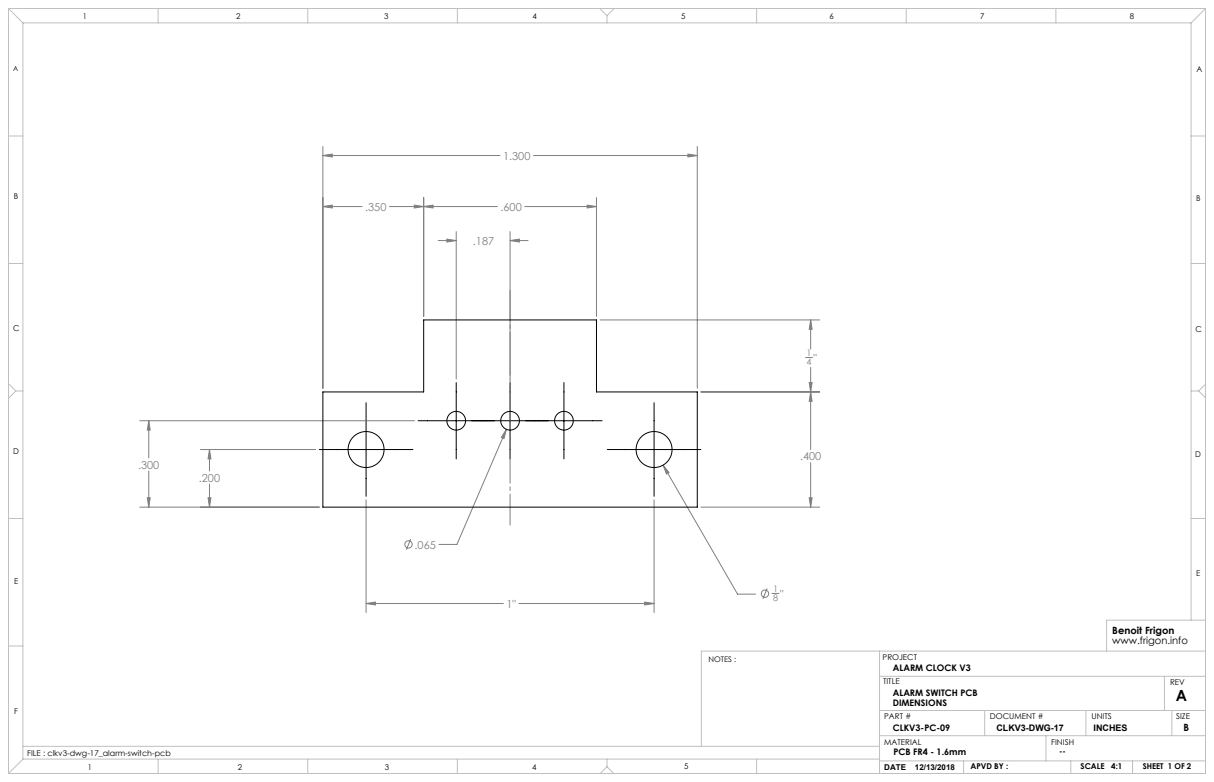
[picture p123: page 1]
SHEET 1 OF 2; ALARM CLOCK V3; ALARM SWITCH PCB; PART #; DOCUMENT #; UNITS; DATE 12/13/2018; SCALE 4:1; PCB FR4 - 1.6mm; NOTES :; APVD BY :

Benoit Frigon
www.frigon.info

FILE : clkv3-dwg-17_alarm-switch-pcb

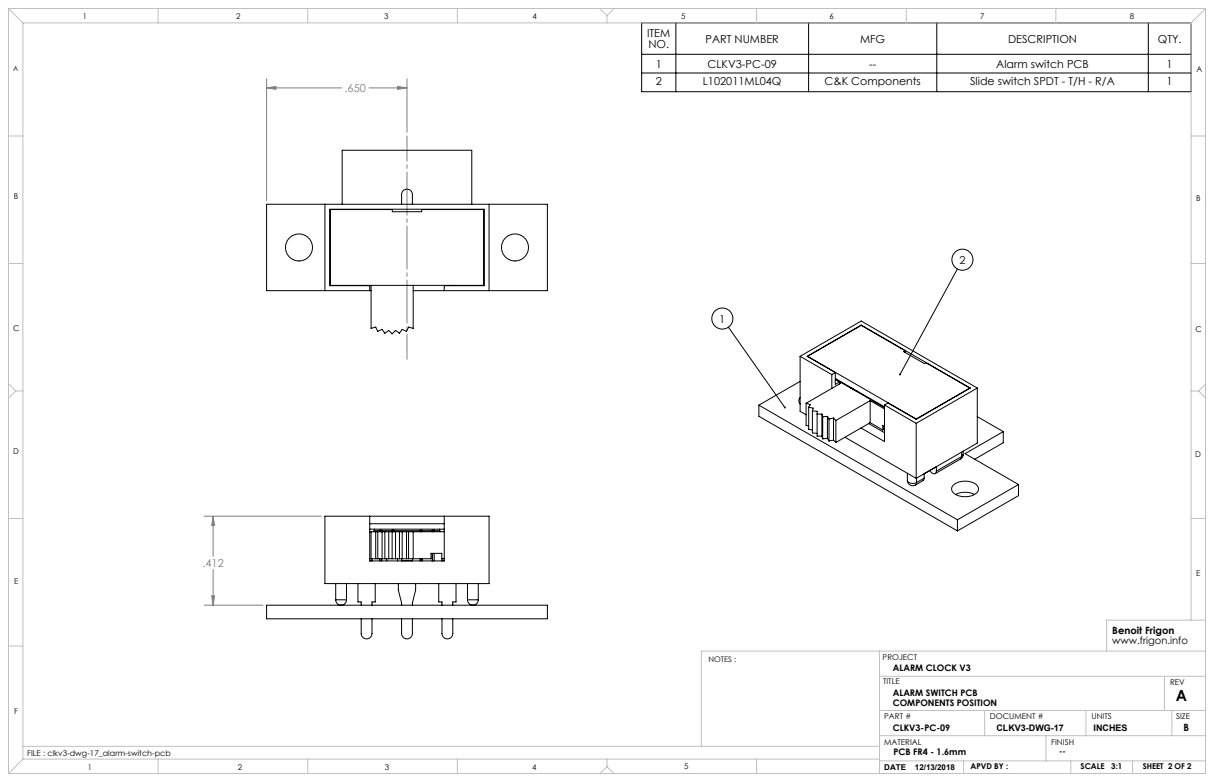
[picture p124: page 2]
SHEET 2 OF 2; ALARM CLOCK V3; ALARM SWITCH PCB; PART #; DOCUMENT #; UNITS; DATE 12/13/2018; SCALE 3:1; PCB FR4 - 1.6mm; NOTES :; COMPONENTS POSITION; APVD BY :

ITEM NO. | PART NUMBER | MFG | DESCRIPTION | QTY.

1 | CLKV3-PC-09 | -- | Alarm switch PCB | 1
2 | L102011ML04Q | C&K Components | Slide switch SPDT - T/H - R/A | 1

Benoit Frigon
www.frigon.info

FILE : clkv3-dwg-17_alarm-switch-pcb
