bfrigon/alarm-clock-v3/drawings/mechanical/clkv3-dwg-18_rtc-battery-door.pdf

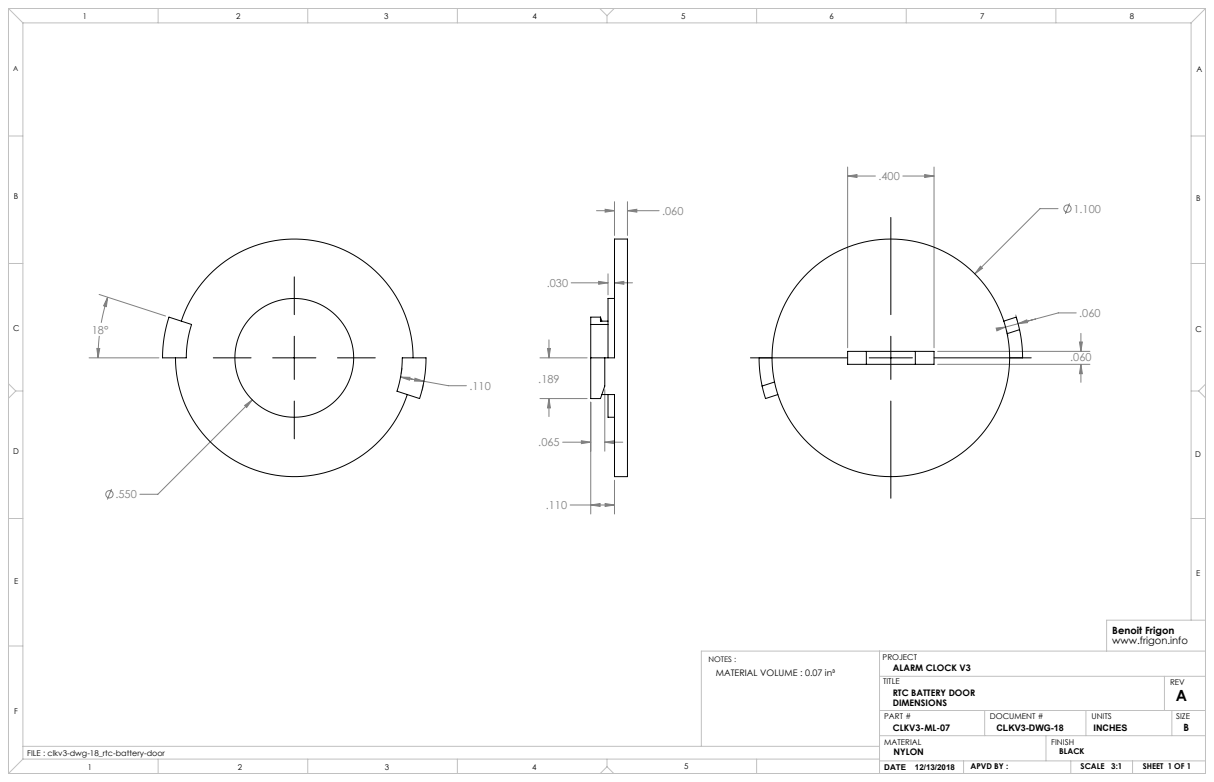
[picture p125: page 1]
SHEET 1 OF 1; ALARM CLOCK V3; RTC BATTERY DOOR; PART #; DOCUMENT #; UNITS; DATE 12/13/2018; SCALE 3:1; APVD BY :

Benoit Frigon
www.frigon.info

NOTES :
MATERIAL VOLUME : 0.07 in³

FILE : clkv3-dwg-18_rtc-battery-door
