bfrigon/alarm-clock-v3/drawings/mechanical/clkv3-dwg-20_rgb-lamp-window-cover.pdf

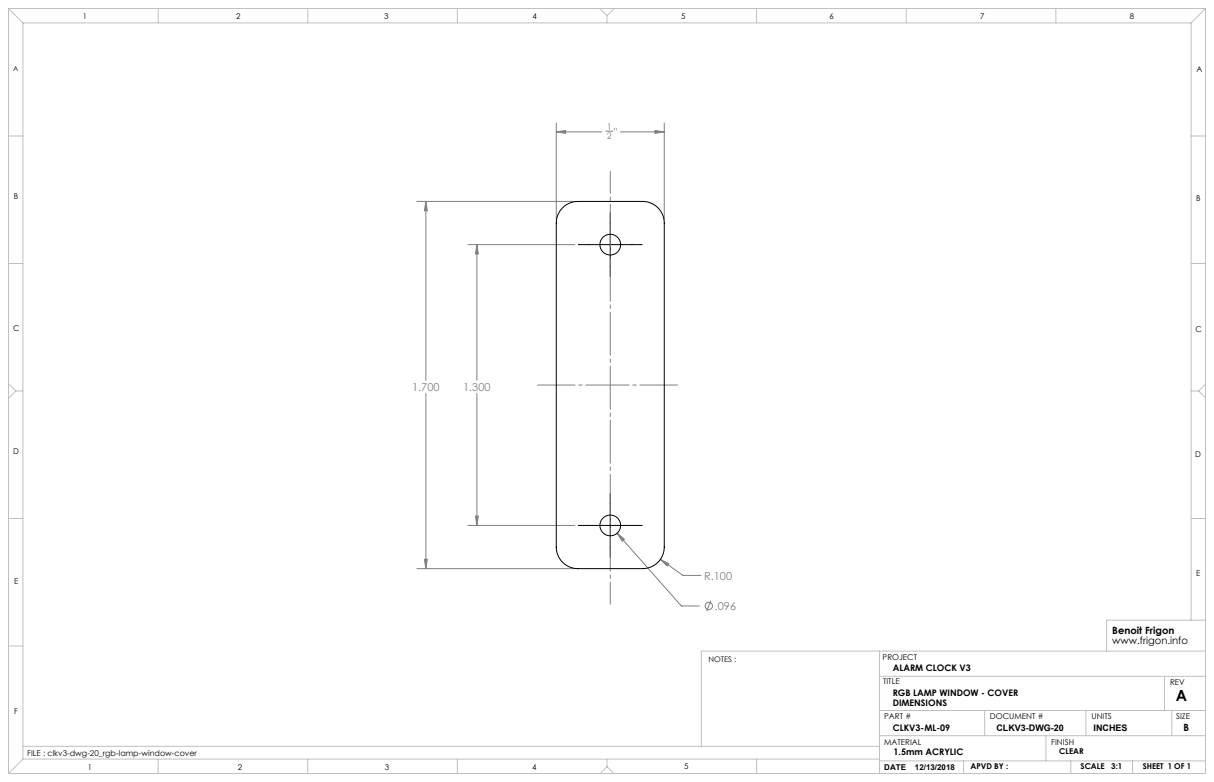
[picture p127: page 1]
SHEET 1 OF 1; ALARM CLOCK V3; RGB LAMP WINDOW - COVER; PART #; DOCUMENT #; UNITS; DATE 12/13/2018; SCALE 3:1; 1.5mm ACRYLIC; NOTES :; APVD BY :

Benoit Frigon
www.frigon.info

FILE : clkv3-dwg-20_rgb-lamp-window-cover
