bfrigon/alarm-clock-v3/drawings/mechanical/clkv3-dwg-21_front-panel-window.pdf

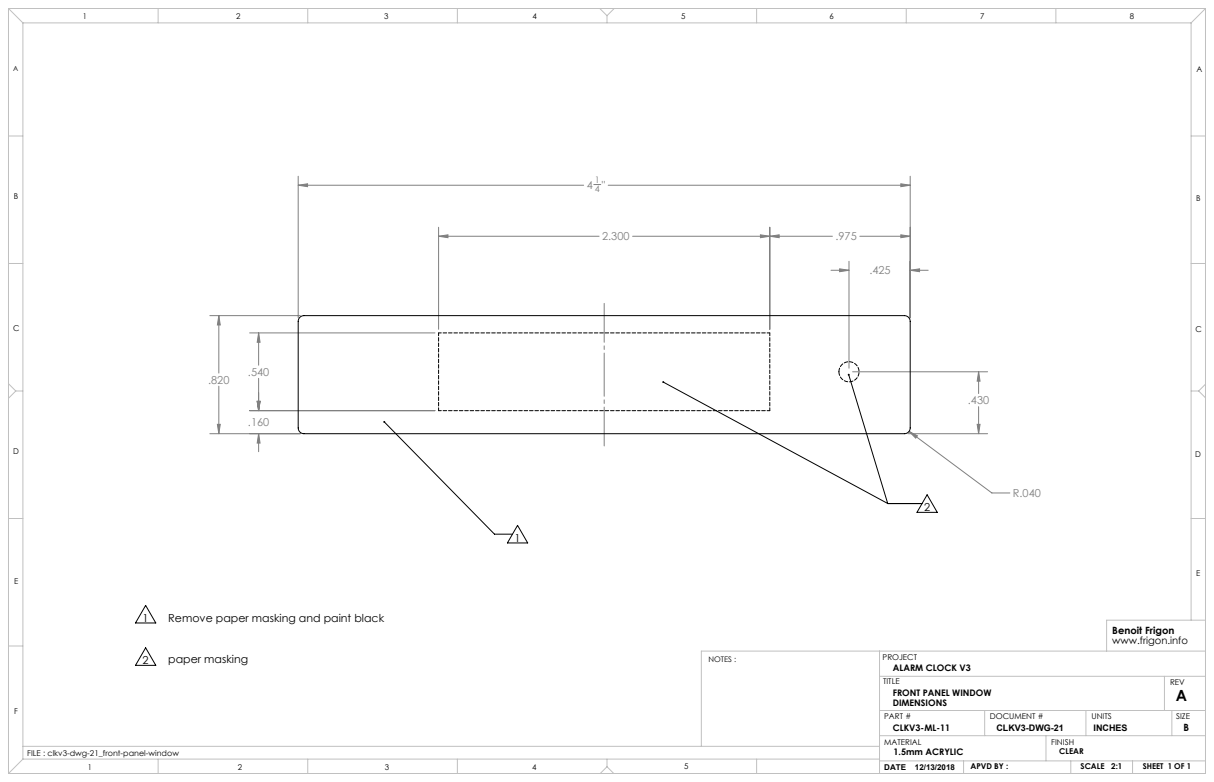
[picture p128: page 1]
paper masking; SHEET 1 OF 1; ALARM CLOCK V3; FRONT PANEL WINDOW; PART #; DOCUMENT #; UNITS; DATE 12/13/2018; SCALE 2:1; 1.5mm ACRYLIC; NOTES :; APVD BY :

Remove paper masking and paint black

Benoit Frigon
www.frigon.info

FILE : clkv3-dwg-21_front-panel-window
