bfrigon/alarm-clock-v3/drawings/mechanical/clkv3-dwg-22_battery-holder.pdf

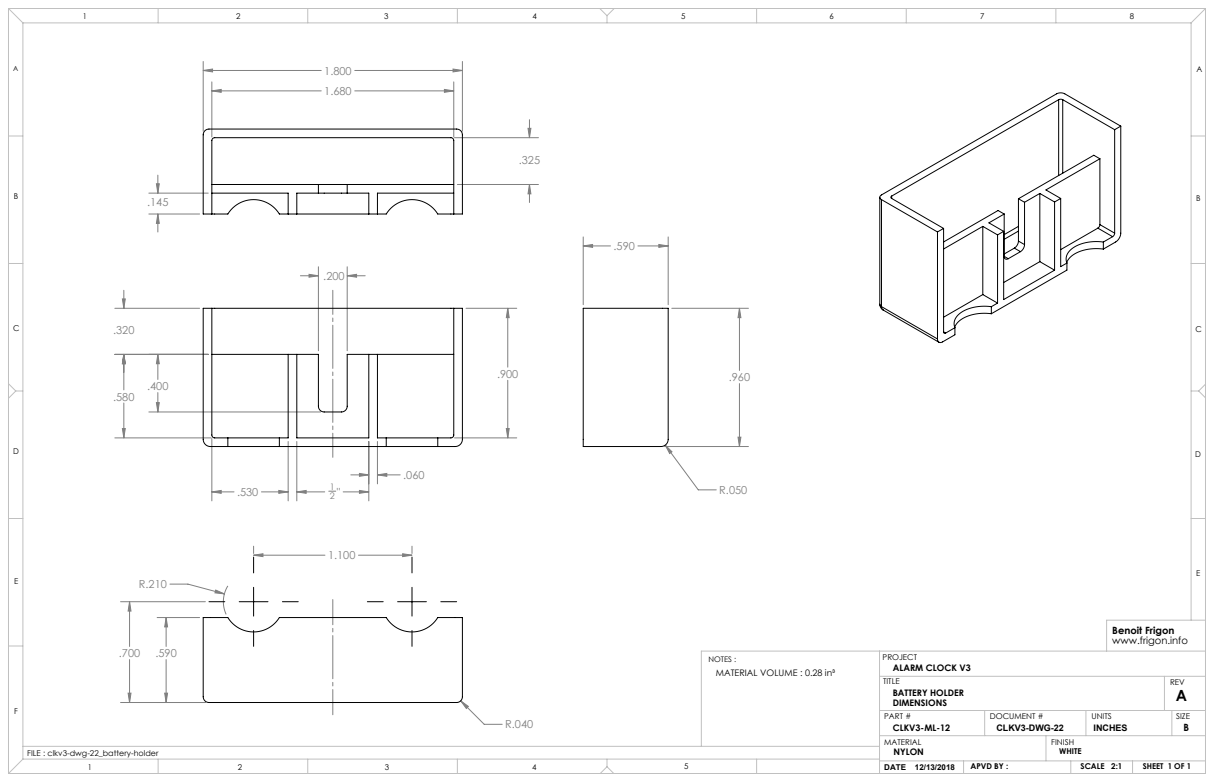
[picture p129: page 1]
SHEET 1 OF 1; ALARM CLOCK V3; BATTERY HOLDER; PART #; DOCUMENT #; UNITS; DATE 12/13/2018; SCALE 2:1; APVD BY :

Benoit Frigon
www.frigon.info

NOTES :
MATERIAL VOLUME : 0.28 in³

FILE : clkv3-dwg-22_battery-holder
