bfrigon/alarm-clock-v3/drawings/mechanical/clkv3-dwg-30_assy-display-frame-front.pdf

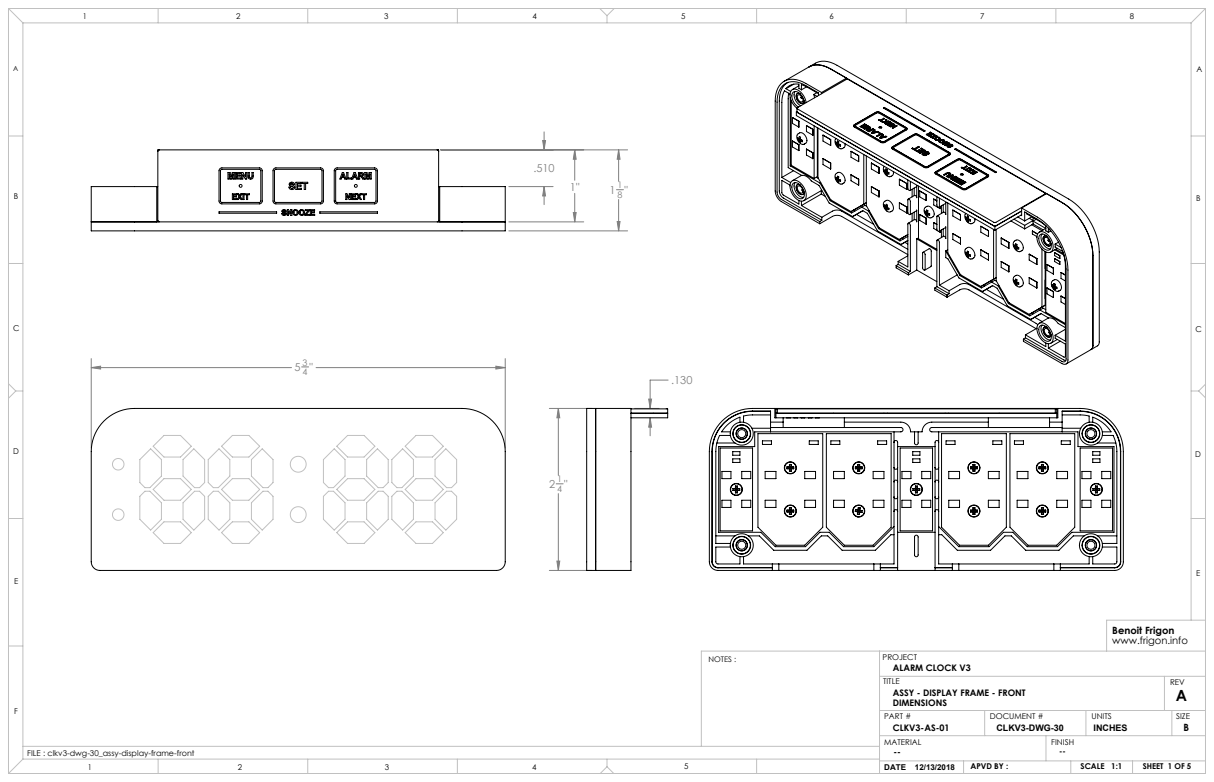
[picture p130: page 1]
SHEET 1 OF 5; ALARM CLOCK V3; ASSY - DISPLAY FRAME - FRONT; PART #; DOCUMENT #; UNITS; DATE 12/13/2018; SCALE 1:1; NOTES :; APVD BY :

Benoit Frigon
www.frigon.info

FILE : clkv3-dwg-30_assy-display-frame-front

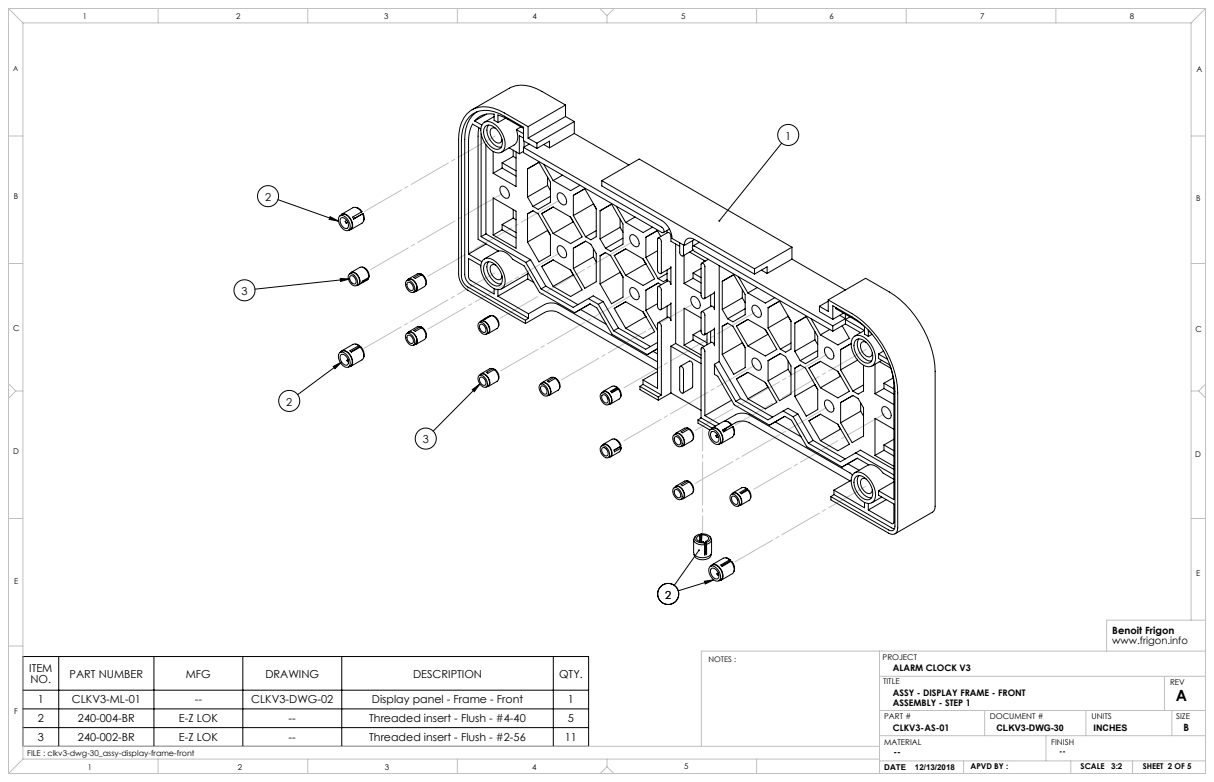
[picture p131: page 2]
SHEET 2 OF 5; DOCUMENT #; UNITS; SCALE 3:2; NOTES :

Benoit Frigon
www.frigon.info

PROJECT
ALARM CLOCK V3
TITLE
ASSY - DISPLAY FRAME - FRONT
ASSEMBLY - STEP 1
PART #

ITEM NO. | PART NUMBER | MFG | DRAWING | DESCRIPTION | QTY.

1 | CLKV3-ML-01 | -- | CLKV3-DWG-02 | Display panel - Frame - Front | 1
2 | 240-004-BR | E-Z LOK | -- | Threaded insert - Flush - #4-40 | 5
3 | 240-002-BR | E-Z LOK | -- | Threaded insert - Flush - #2-56 | 11

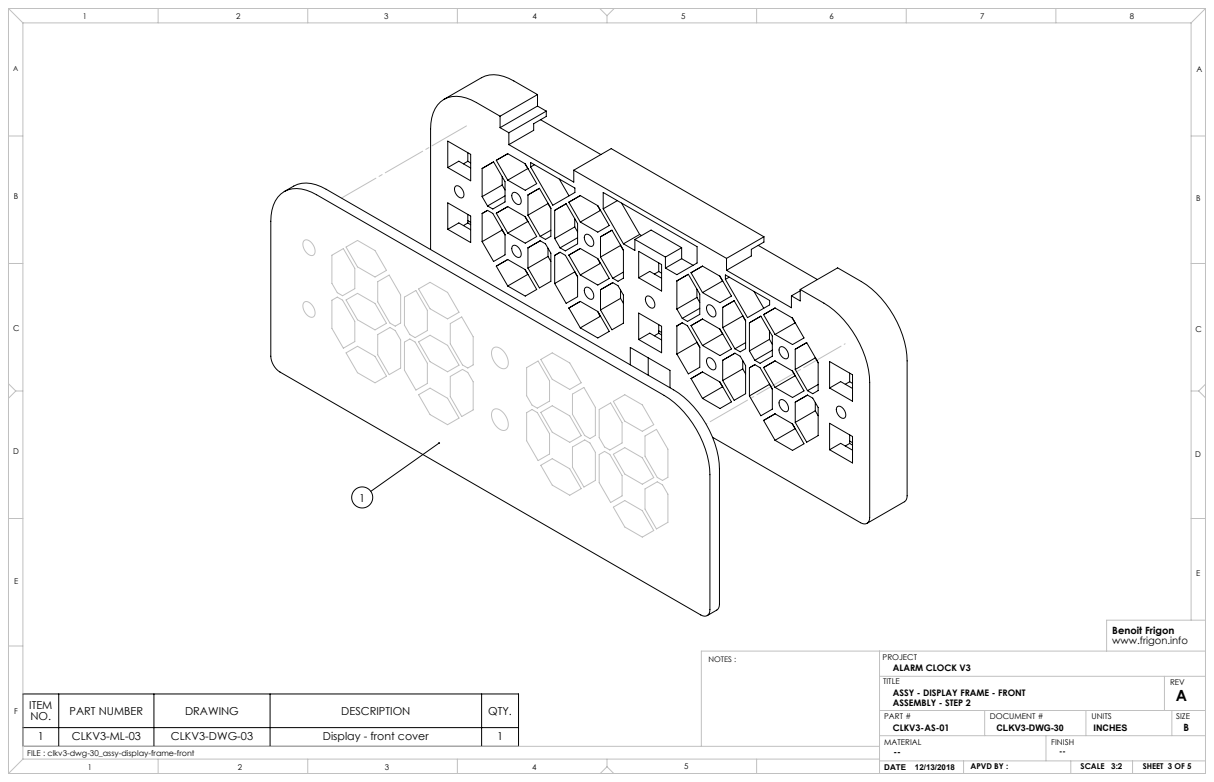
[picture p132: page 3]
SHEET 3 OF 5; DOCUMENT #; UNITS; NOTES :

Benoit Frigon
www.frigon.info

PROJECT
ALARM CLOCK V3
TITLE
ASSY - DISPLAY FRAME - FRONT
ASSEMBLY - STEP 2
PART #

ITEM NO. | PART NUMBER | DRAWING | DESCRIPTION | QTY.

1 | CLKV3-ML-03 | CLKV3-DWG-03 | Display - front cover | 1

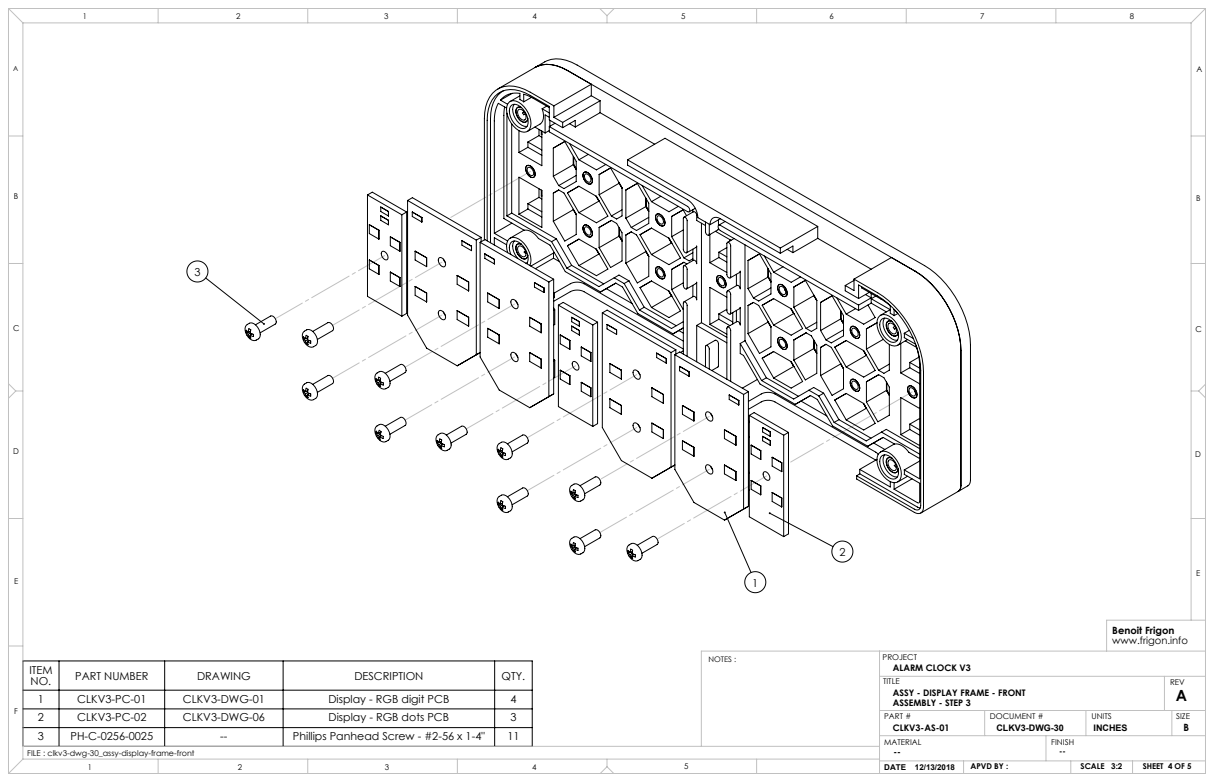
[picture p133: page 4]
SHEET 4 OF 5; DOCUMENT #; UNITS; NOTES :

Benoit Frigon
www.frigon.info

PROJECT
ALARM CLOCK V3
TITLE
ASSY - DISPLAY FRAME - FRONT
ASSEMBLY - STEP 3
PART #

ITEM NO. | PART NUMBER | DRAWING | DESCRIPTION | QTY.
1 | CLKV3-PC-01 | CLKV3-DWG-01 | Display - RGB digit PCB | 4
2 | CLKV3-PC-02 | CLKV3-DWG-06 | Display - RGB dots PCB | 3
3 | PH-C-0256-0025 | -- | Phillips Panhead Screw - #2-56 x 1-4" | 11

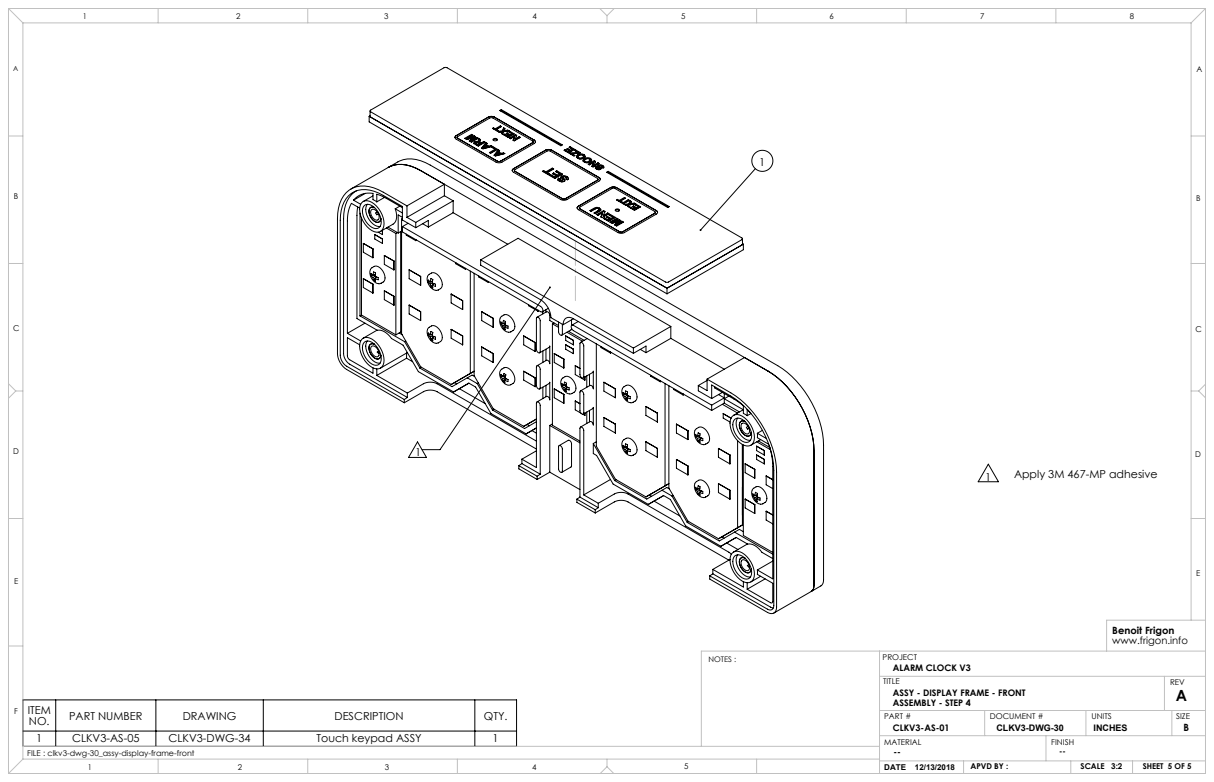
[picture p134: page 5]
Apply 3M 467-MP adhesive; SHEET 5 OF 5; DOCUMENT #; UNITS; NOTES :

Benoit Frigon
www.frigon.info

PROJECT
ALARM CLOCK V3
TITLE
ASSY - DISPLAY FRAME - FRONT
ASSEMBLY - STEP 4
PART #

ITEM NO. | PART NUMBER | DRAWING | DESCRIPTION | QTY.
1 | CLKV3-AS-05 | CLKV3-DWG-34 | Touch keypad ASSY | 1
