bfrigon/alarm-clock-v3/drawings/mechanical/clkv3-dwg-31_assy-display-frame-back.pdf

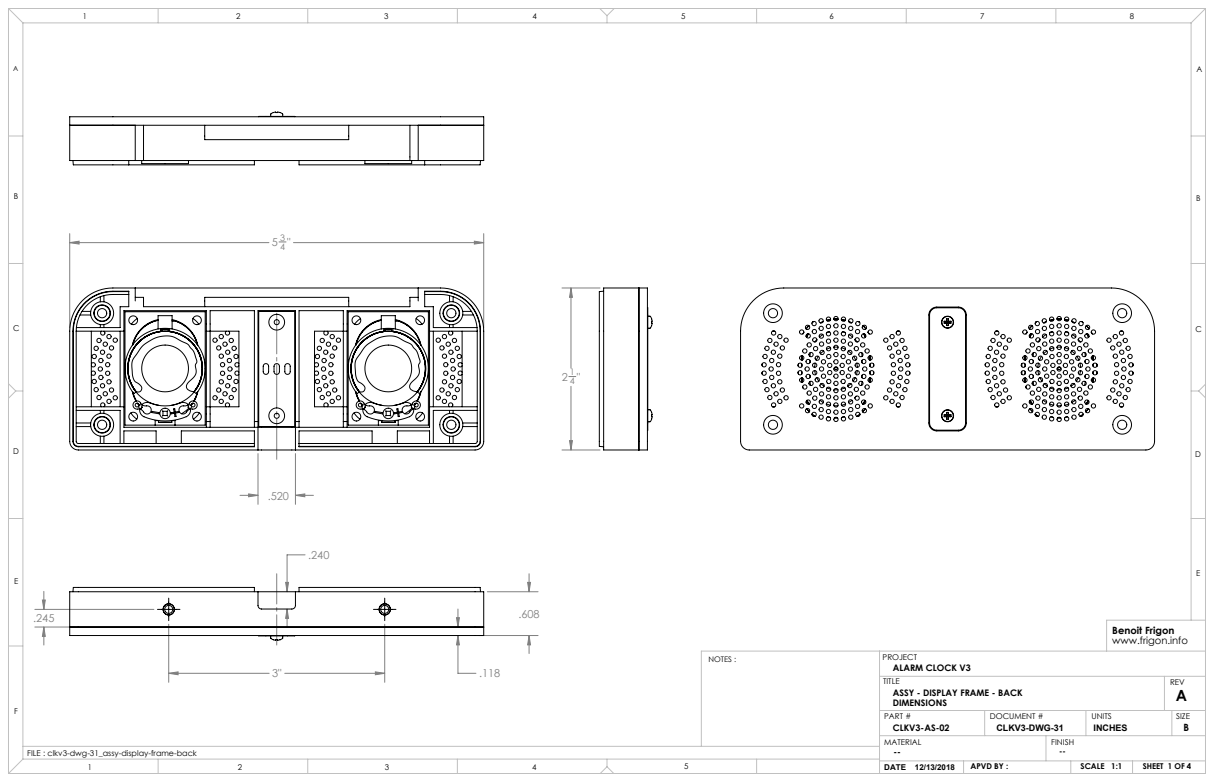
[picture p135: page 1]
SHEET 1 OF 4; ALARM CLOCK V3; ASSY - DISPLAY FRAME - BACK; PART #; DOCUMENT #; UNITS; DATE 12/13/2018; SCALE 1:1; NOTES :; APVD BY :

Benoit Frigon
www.frigon.info

FILE : clkv3-dwg-31_assy-display-frame-back

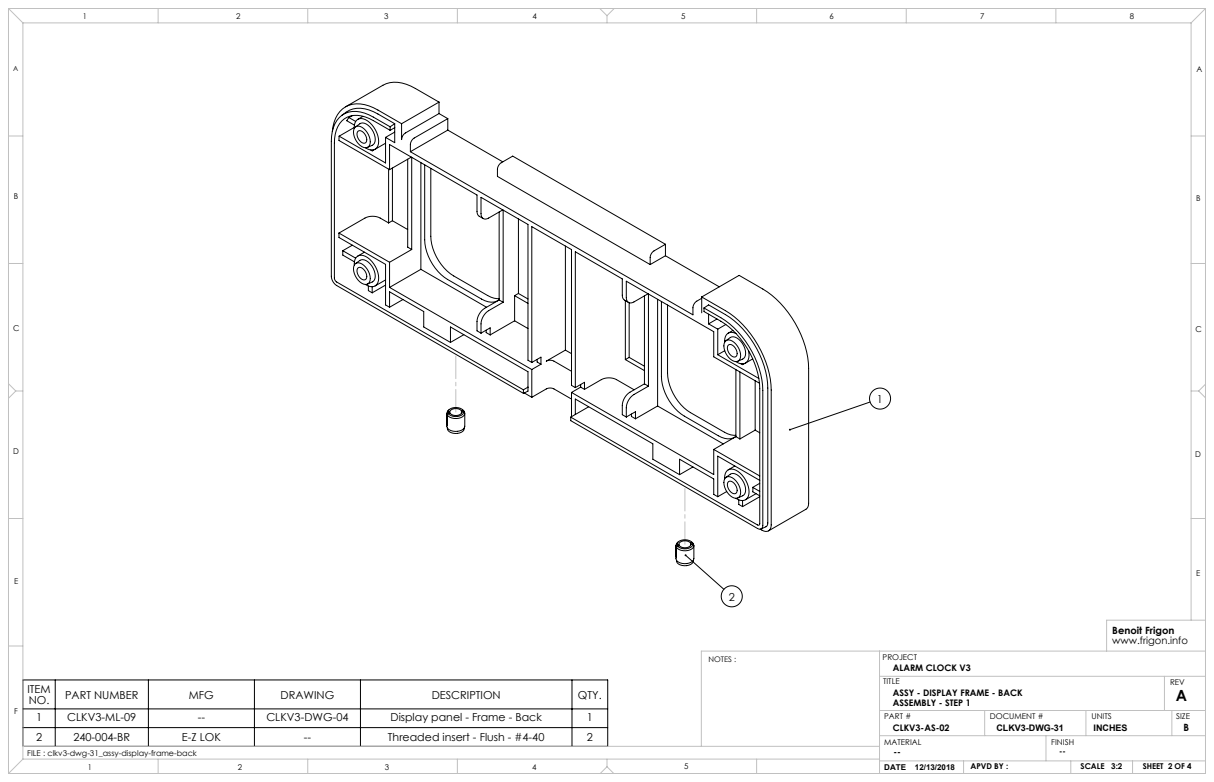
[picture p136: page 2]
SHEET 2 OF 4; DOCUMENT #; UNITS; SCALE 3:2; NOTES :

Benoit Frigon
www.frigon.info

PROJECT
ALARM CLOCK V3
TITLE
ASSY - DISPLAY FRAME - BACK
ASSEMBLY - STEP 1
PART #

ITEM NO. | PART NUMBER | MFG | DRAWING | DESCRIPTION | QTY.
1 | CLKV3-ML-09 | -- | CLKV3-DWG-04 | Display panel - Frame - Back | 1
2 | 240-004-BR | E-Z LOK | -- | Threaded insert - Flush - #4-40 | 2

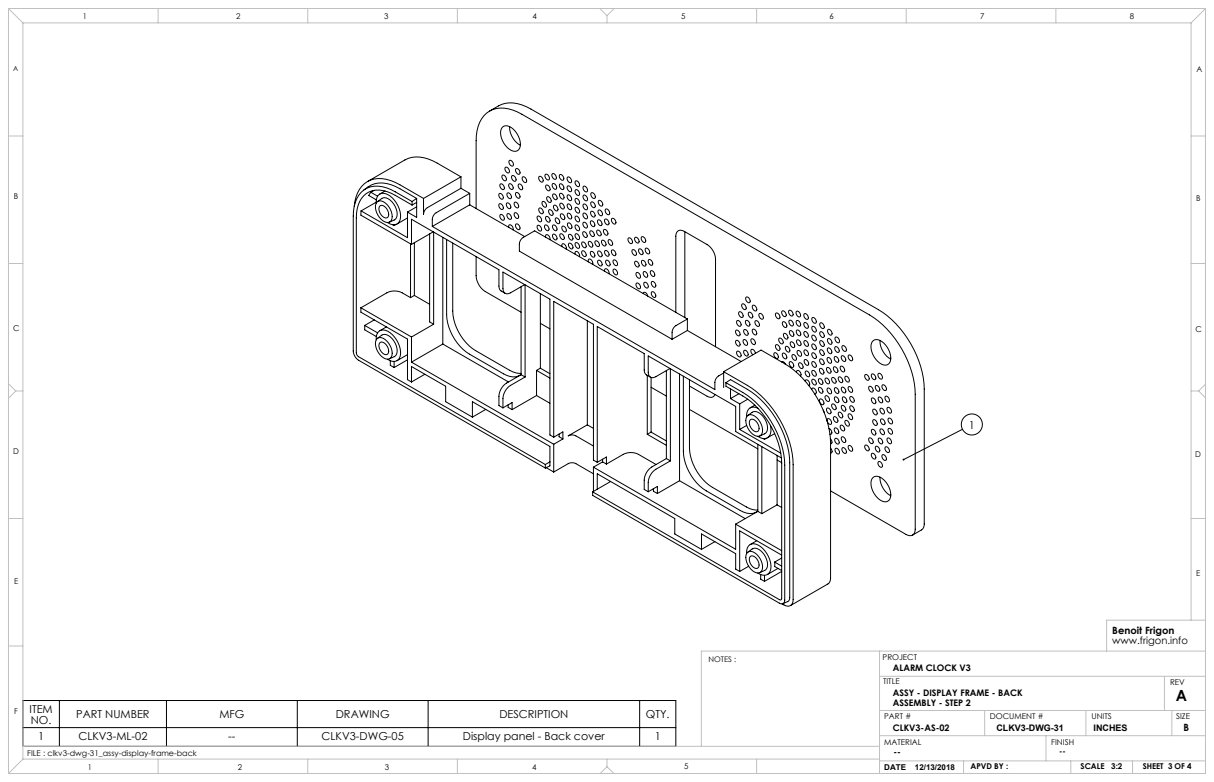
[picture p137: page 3]
SHEET 3 OF 4; DOCUMENT #; UNITS; NOTES :

Benoit Frigon
www.frigon.info

PROJECT
ALARM CLOCK V3
TITLE
ASSY - DISPLAY FRAME - BACK
ASSEMBLY - STEP 2
PART #

ITEM NO. | PART NUMBER | MFG | DRAWING | DESCRIPTION | QTY.
1 | CLKV3-ML-02 | -- | CLKV3-DWG-05 | Display panel - Back cover | 1

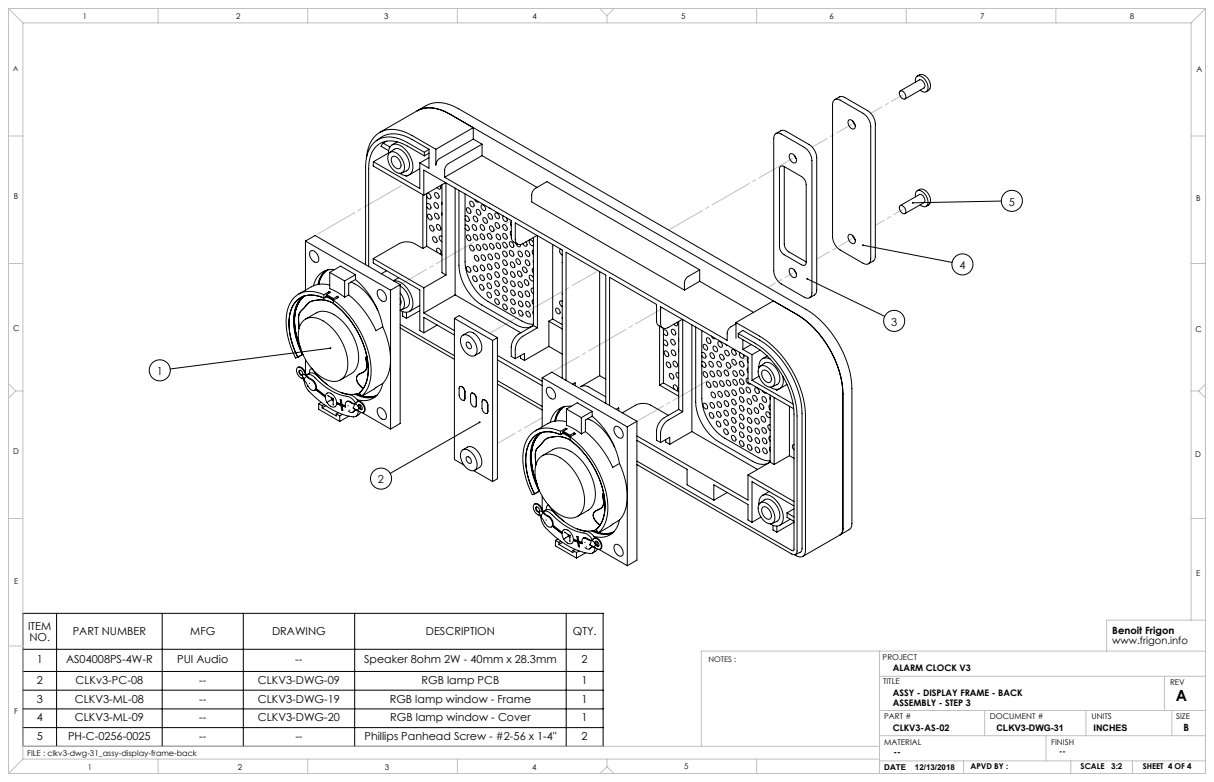
[picture p138: page 4]
SHEET 4 OF 4; DOCUMENT #; UNITS; NOTES :

ITEM NO. | PART NUMBER | MFG | DRAWING | DESCRIPTION | QTY.

Benoit Frigon
www.frigon.info

1 | AS04008PS-4W-R | PUI Audio | -- | Speaker 8ohm 2W - 40mm x 28.3mm | 2
2 | CLKv3-PC-08 | -- | CLKV3-DWG-09 | RGB lamp PCB | 1
3 | CLKV3-ML-08 | -- | CLKV3-DWG-19 | RGB lamp window - Frame | 1
4 | CLKV3-ML-09 | -- | CLKV3-DWG-20 | RGB lamp window - Cover | 1
5 | PH-C-0256-0025 | -- | -- | Phillips Panhead Screw - #2-56 x 1-4" | 2

PROJECT
ALARM CLOCK V3
TITLE
ASSY - DISPLAY FRAME - BACK
ASSEMBLY - STEP 3
PART #
