bfrigon/alarm-clock-v3/drawings/mechanical/clkv3-dwg-33_assy-motherboard.pdf

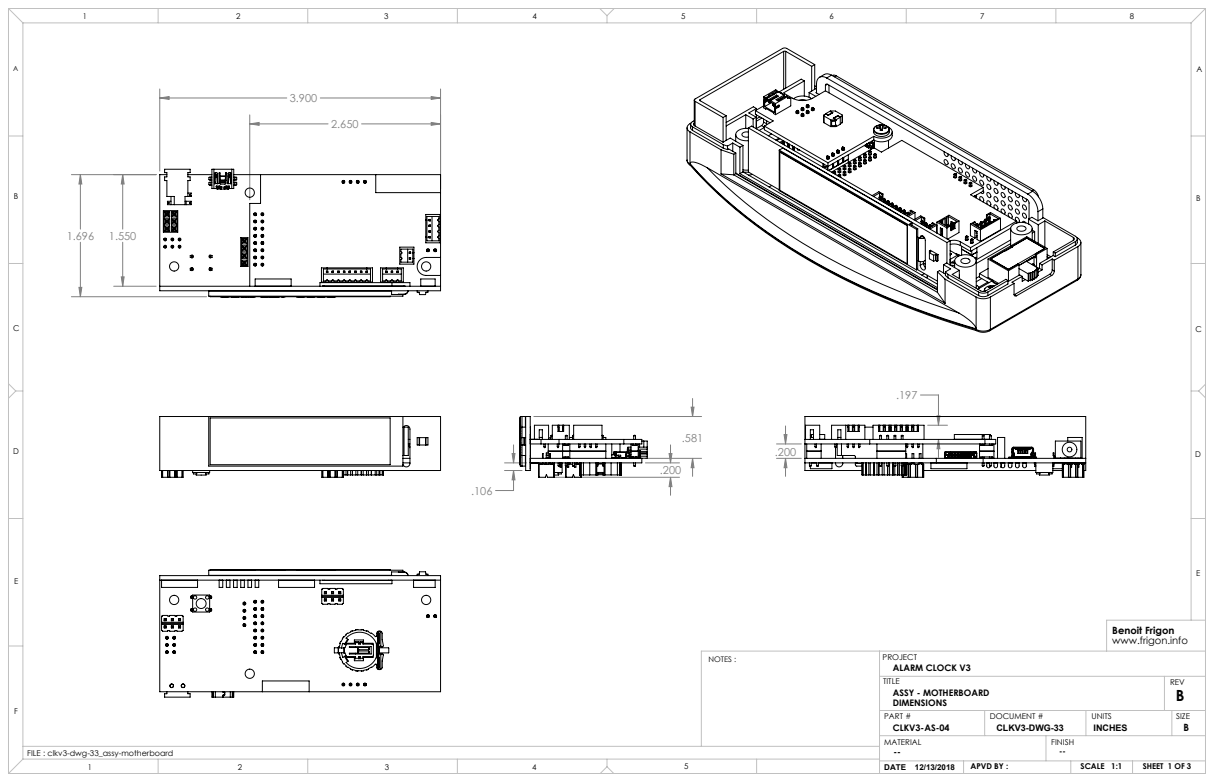
[picture p139: page 1]
SHEET 1 OF 3; ALARM CLOCK V3; ASSY - MOTHERBOARD; PART #; DOCUMENT #; UNITS; DATE 12/13/2018; SCALE 1:1; NOTES :; APVD BY :

Benoit Frigon
www.frigon.info

FILE : clkv3-dwg-33_assy-motherboard

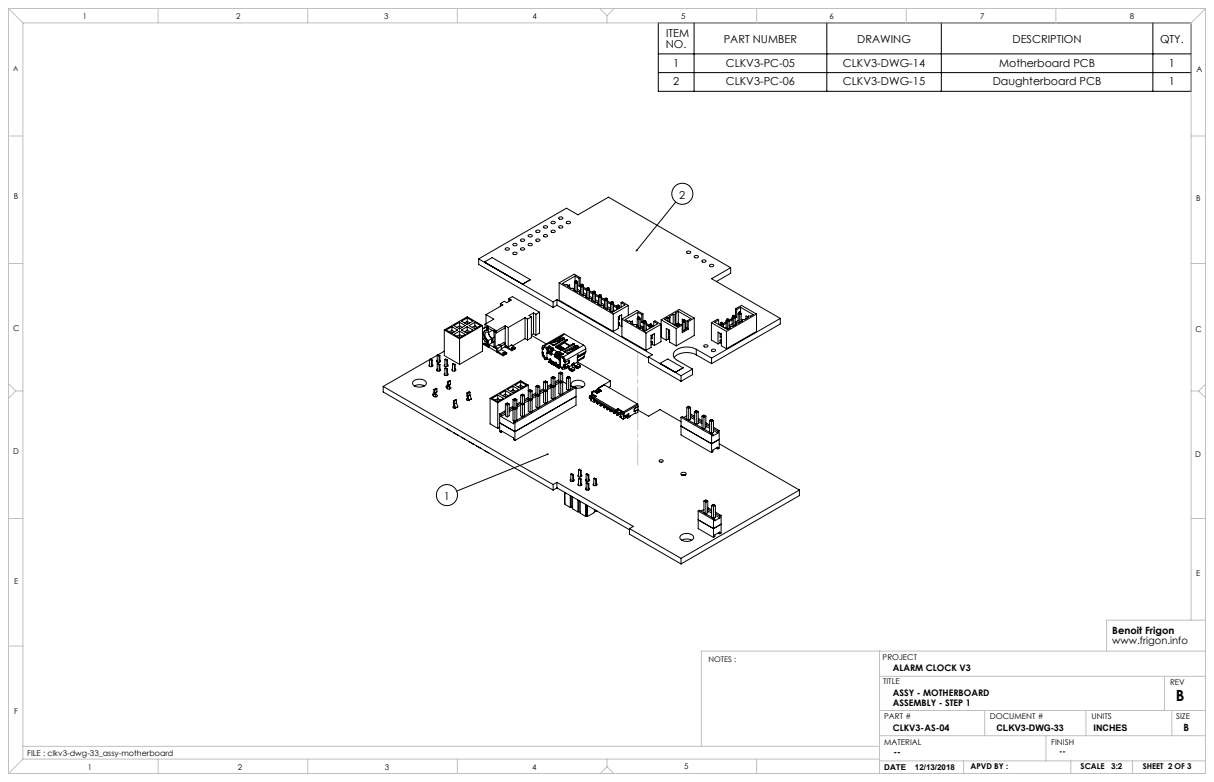
[picture p140: page 2]
SHEET 2 OF 3; ALARM CLOCK V3; ASSY - MOTHERBOARD; PART #; DOCUMENT #; UNITS; SCALE 3:2; NOTES :; ASSEMBLY - STEP 1

ITEM NO. | PART NUMBER | DRAWING | DESCRIPTION | QTY.

1 | CLKV3-PC-05 | CLKV3-DWG-14 | Motherboard PCB | 1
2 | CLKV3-PC-06 | CLKV3-DWG-15 | Daughterboard PCB | 1

Benoit Frigon
www.frigon.info

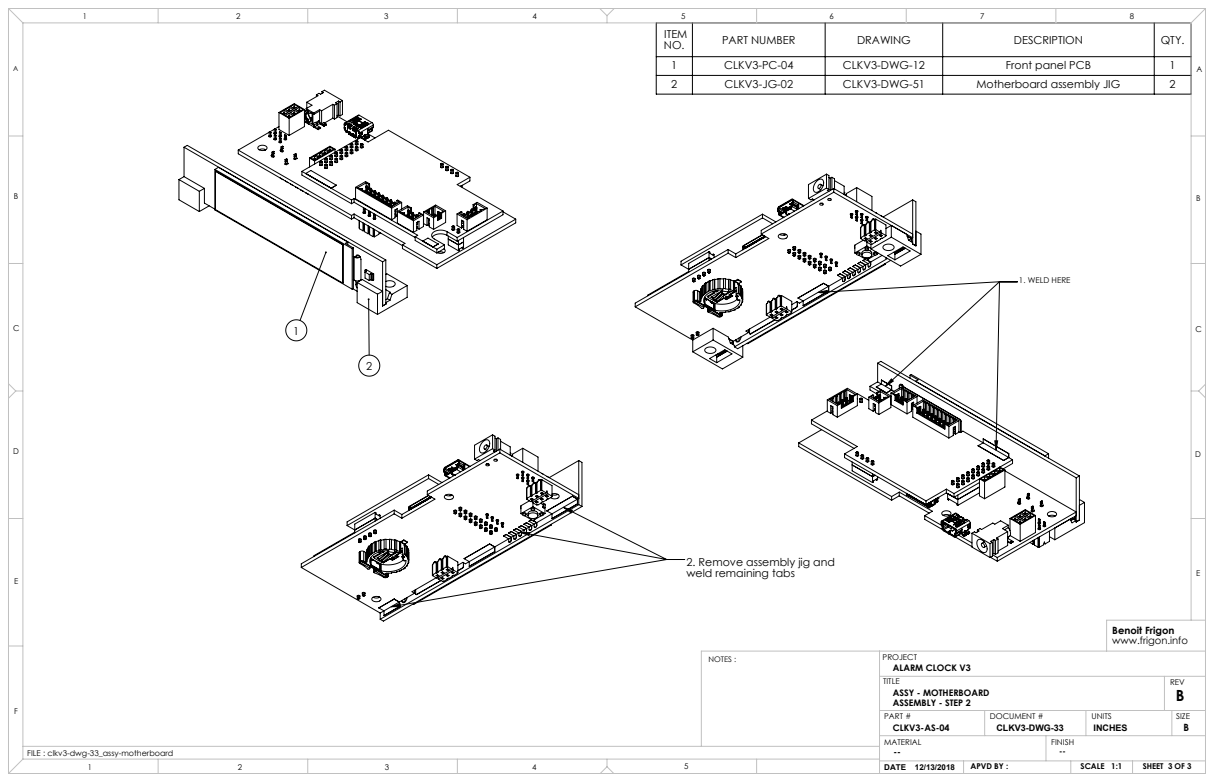
[picture p141: page 3]
1. WELD HERE; SHEET 3 OF 3; ALARM CLOCK V3; ASSY - MOTHERBOARD; PART #; DOCUMENT #; UNITS; SCALE 1:1; NOTES :; ASSEMBLY - STEP 2

ITEM NO. | PART NUMBER | DRAWING | DESCRIPTION | QTY.

1 | CLKV3-PC-04 | CLKV3-DWG-12 | Front panel PCB | 1
2 | CLKV3-JG-02 | CLKV3-DWG-51 | Motherboard assembly JIG | 2

2. Remove assembly jig and
weld remaining tabs

Benoit Frigon
www.frigon.info
