bfrigon/alarm-clock-v3/drawings/mechanical/clkv3-dwg-50_dev-jig.pdf

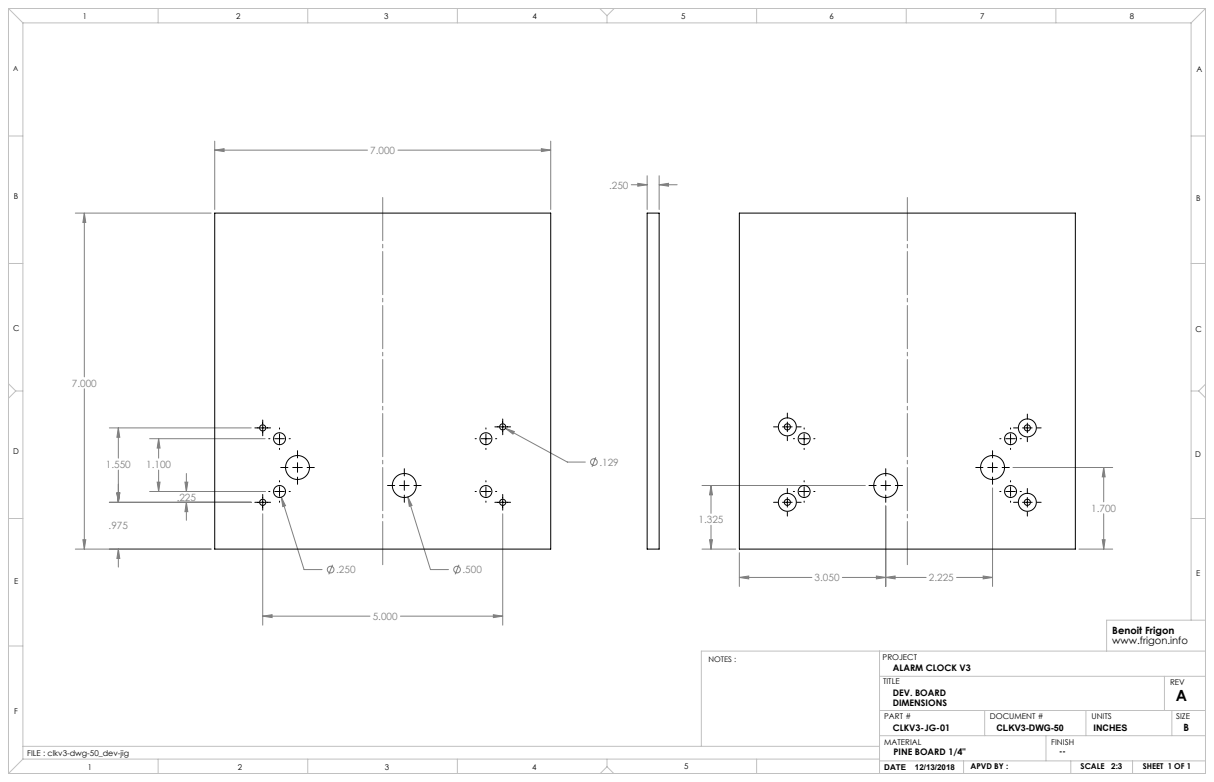
[picture p142: page 1]
SHEET 1 OF 1; ALARM CLOCK V3; DEV. BOARD; PART #; DOCUMENT #; UNITS; DATE 12/13/2018; SCALE 2:3; PINE BOARD 1/4"; NOTES :; APVD BY :

Benoit Frigon
www.frigon.info

FILE : clkv3-dwg-50_dev-jig
