bfrigon/alarm-clock-v3/drawings/mechanical/clkv3-dwg-51_motherboard-assy-jig.pdf

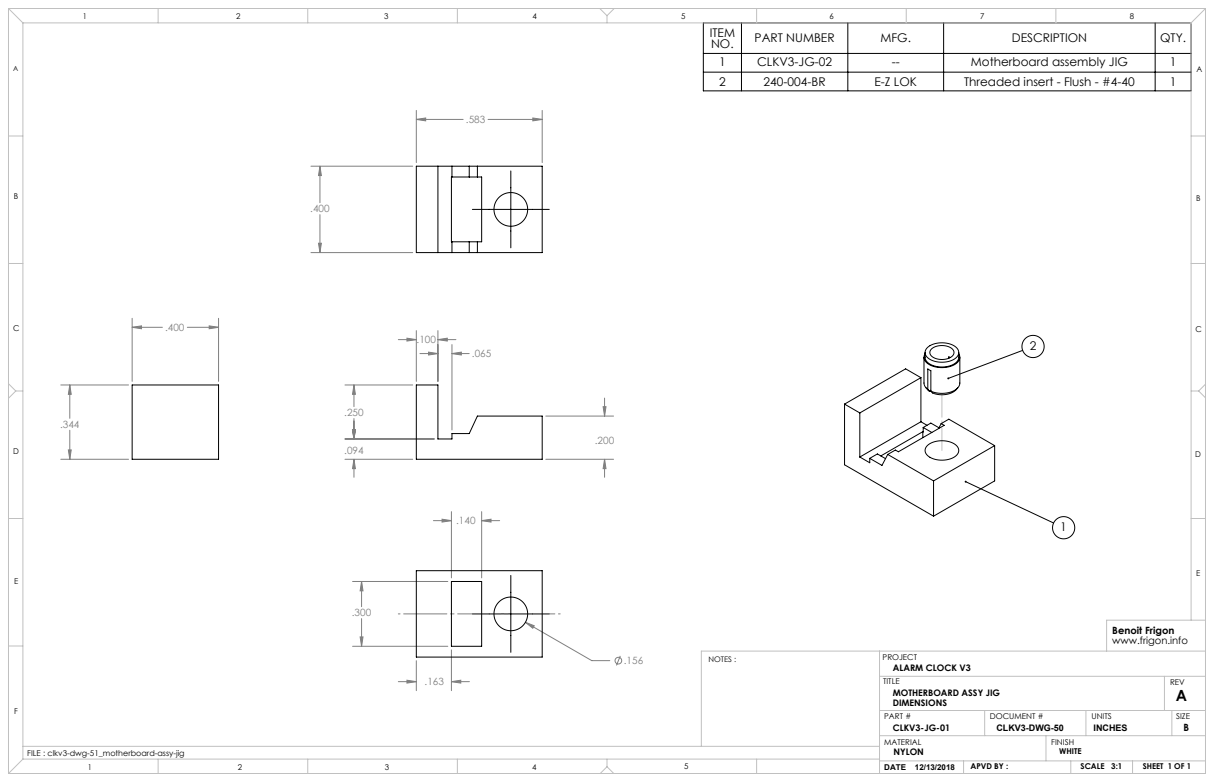
[picture p143: page 1]
SHEET 1 OF 1; ALARM CLOCK V3; MOTHERBOARD ASSY JIG; PART #; DOCUMENT #; UNITS; DATE 12/13/2018; SCALE 3:1; NOTES :; APVD BY :

ITEM NO. | PART NUMBER | MFG. | DESCRIPTION | QTY.
1 | CLKV3-JG-02 | -- | Motherboard assembly JIG | 1
2 | 240-004-BR | E-Z LOK | Threaded insert - Flush - #4-40 | 1

Benoit Frigon
www.frigon.info

FILE : clkv3-dwg-51_motherboard-assy-jig
