bfrigon/alarm-clock-v3/drawings/mechanical/clkv3-dwg.pdf

.650

.050

.096 THRU ALL; TOP; BOTTOM; SHEET 1 OF 2; ALARM CLOCK V3 TITLE DISPLAY - RGB DIGIT PCB; REV; PART # CLKV3-PC-01; DOCUMENT #; UNITS; INCHES; SIZE B; DATE 12/13/2018; CLKV3-DWG-01; SCALE 3:1; PROJECT; MATERIAL PCB FR4 - 1.6mm; FINISH --; NOTES :; DIMENSIONS; APVD BY :

Benoit Frigon
www.frigon.info

FILE : clkv3-dwg-01_rgb-digits-pcb

.600
.067

DOUT; DIN; GND; SHEET 2 OF 2; REV; DOCUMENT #; UNITS; SIZE; CLKV3-DWG-01; SCALE 3:1; NOTES :

Benoit Frigon
www.frigon.info

PROJECT
ALARM CLOCK V3
TITLE
DISPLAY - RGB DIGIT PCB
COMPONENTS POSITION
PART #
CLKV3-PC-01
PCB FR4 - 1.6mm

ITEM NO. | PART NUMBER | MFG. | DESCRIPTION | QTY.

1 | CLKV3-PC-01 | -- | Display - RGB digit PCB | 1
2 | IN-PI554FCH | Inolux | RGB LED with integrated driver | 7

FILE : clkv3-dwg-01_rgb-digits-pcb

.450
.275

.089 THRU ALL; TOP; BOTTOM; SHEET 1 OF 2; REV; DOCUMENT #; UNITS; SIZE; CLKV3-DWG-06; SCALE 3:1; NOTES :

Benoit Frigon
www.frigon.info

PROJECT
ALARM CLOCK V3
TITLE
DISPLAY - RGB DOTS PCB
DIMENSIONS
PART #
CLKV3-PC-02
PCB FR4 - 1.6mm

FILE : clkv3-dwg-06_rgb-dots-pcb

.225
.067

GND; DATA OUT; DATA IN; SHEET 2 OF 2; REV; DOCUMENT #; UNITS; SIZE; CLKV3-DWG-06; SCALE 3:1; NOTES :

Benoit Frigon
www.frigon.info

PROJECT
ALARM CLOCK V3
TITLE
DISPLAY - RGB DOTS PCB
COMPONENTS POSITION
PART #
CLKV3-PC-02
PCB FR4 - 1.6mm

ITEM NO. | PART NUMBER | MFG | DESCRIPTION | QTY.

1 | CLKV3-PC-02 | -- | Display - RGB Dots PCB | 1
2 | IN-PI554FCH | Inolux | RGB LED with integrated driver | 2

FILE : clkv3-dwg-06_rgb-dots-pcb

5 ³
4.850

SECTION A-A; DETAIL B SCALE 6 : 1; SECTION D-D; DETAIL C SCALE 6 : 1; DETAIL E SCALE 4 : 1; SHEET 1 OF 2; ALARM CLOCK V3 TITLE DISPLAY - FRAME - FRONT; REV; PART # CLKV3-ML-01; DOCUMENT #; UNITS; SIZE; CLKV3-DWG-02; SCALE 1:1; PROJECT; NYLON; BLACK; DIMENSIONS

Benoit Frigon
www.frigon.info

NOTES :
MATERIAL VOLUME : 1.94 in³

FILE : clkv3-dwg-02_display-frame-front

.300
H

DETAIL F SCALE 2 : 1; DETAIL G SCALE 4 : 1; DETAIL H SCALE 4 : 1; SHEET 2 OF 2; ALARM CLOCK V3 TITLE DISPLAY - FRAME - FRONT; REV; PART # CLKV3-ML-01; DOCUMENT #; UNITS; SIZE; CLKV3-DWG-02; SCALE 1:1; PROJECT; NYLON; BLACK; DETAILS

Benoit Frigon
www.frigon.info

NOTES :
MATERIAL VOLUME : 1.94 in³

FILE : clkv3-dwg-02_display-frame-front

R.600

.950 | .800 | 3

Engraving; SHEET 1 OF 1; ALARM CLOCK V3 TITLE DISPLAY - FRONT COVER; REV; PART # CLKV3-ML-03; DOCUMENT #; UNITS; SIZE; CLKV3-DWG-03; SCALE 2:1; PROJECT; 3mm ACRYLIC; MIRROR - BRONZE; NOTES :; DIMENSIONS

Benoit Frigon
www.frigon.info

FILE : clkv3-dwg-03_display-front-cover

3.900

.800 .700 | .700

DETAIL SCALE 6 : 1; SHEET 1 OF 1; ALARM CLOCK V3 TITLE TOUCH KEYPAD PCB; REV; PART # CLKV3-PC-03; DOCUMENT #; UNITS; SIZE; CLKV3-DWG-07; SCALE 2:1; PROJECT; PCB FR4 - 1.6mm; NOTES :; DIMENSIONS

Benoit Frigon
www.frigon.info

FILE : clkv3-dwg-07_touch-keypad-pcb

3.900

.600 | .700 | .600

SHEET 1 OF 1; ALARM CLOCK V3 TITLE TOUCH KEYPAD OVERLAY; REV; PART # CLKV3-ML-04; DOCUMENT #; UNITS; SIZE; CLKV3-DWG-08; SCALE 3:1; PROJECT; 1.5mm ACRYLIC; BLACK; NOTES :; DIMENSIONS

Benoit Frigon
www.frigon.info

FILE : clkv3-dwg-08_touch-keypad-overlay

3.860

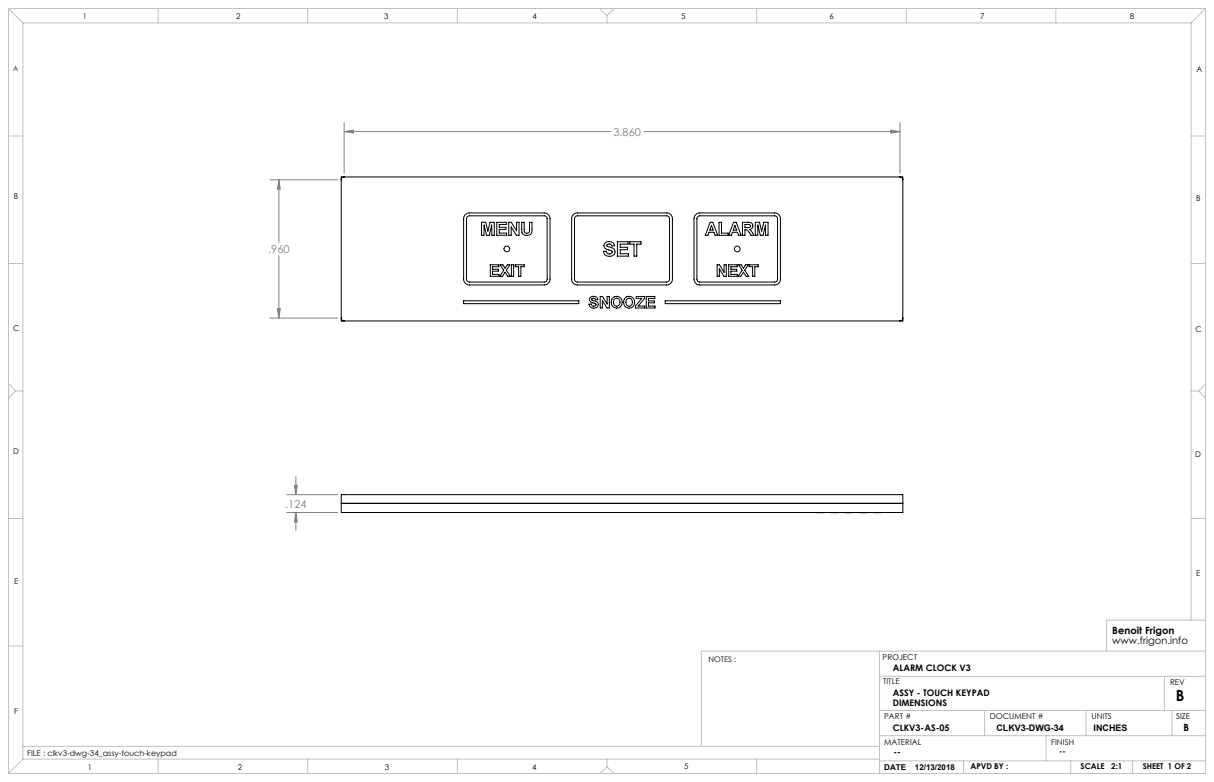
[picture p144: page 10]
SHEET 1 OF 2; ALARM CLOCK V3 TITLE ASSY - TOUCH KEYPAD; REV; PART # CLKV3-AS-05; DOCUMENT #; UNITS; SIZE; CLKV3-DWG-34; SCALE 2:1; PROJECT; NOTES :; DIMENSIONS

Benoit Frigon
www.frigon.info

FILE : clkv3-dwg-34_assy-touch-keypad

1

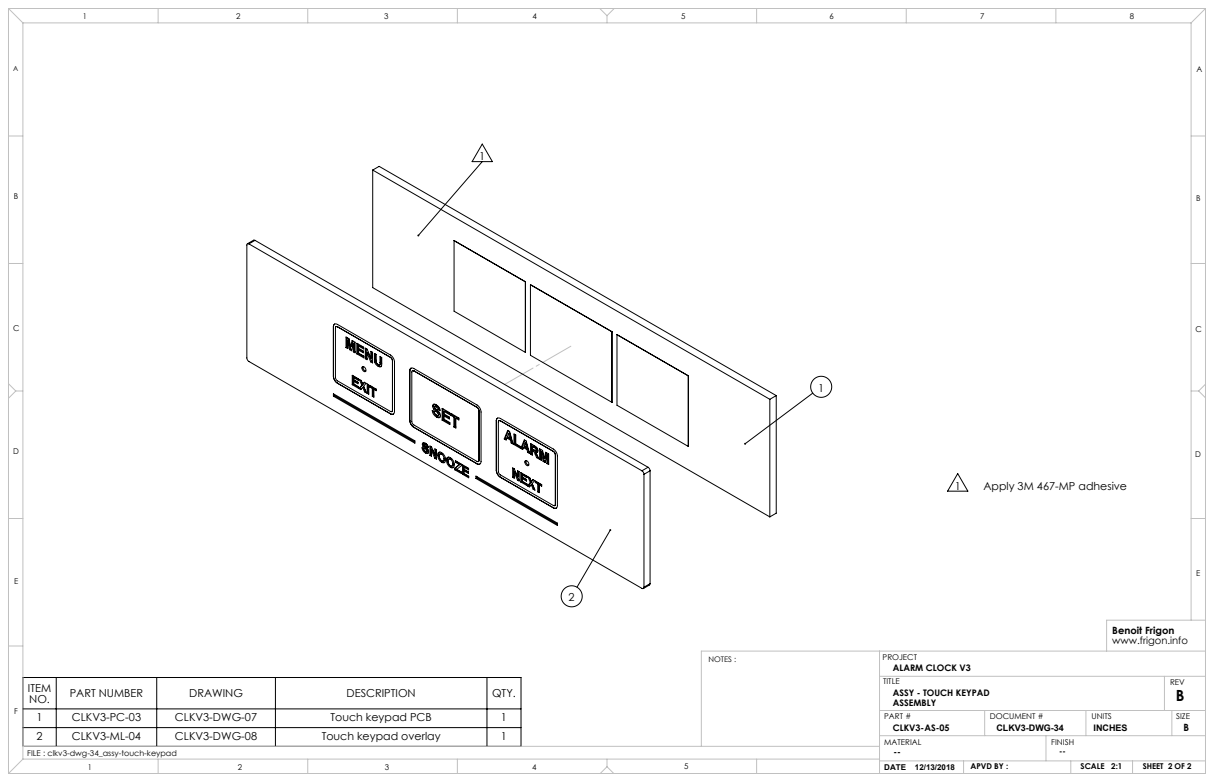
[picture p145: page 11]
Apply 3M 467-MP adhesive; SHEET 2 OF 2; ALARM CLOCK V3 TITLE ASSY - TOUCH KEYPAD; REV; PART # CLKV3-AS-05; DOCUMENT #; UNITS; SIZE; CLKV3-DWG-34; SCALE 2:1; PROJECT; NOTES :; ASSEMBLY

Benoit Frigon
www.frigon.info

ITEM NO. | PART NUMBER | DRAWING | DESCRIPTION | QTY.

1 | CLKV3-PC-03 | CLKV3-DWG-07 | Touch keypad PCB | 1
2 | CLKV3-ML-04 | CLKV3-DWG-08 | Touch keypad overlay | 1

FILE : clkv3-dwg-34_assy-touch-keypad

1 ¹
8 " 1"

SHEET 1 OF 5; REV; DOCUMENT #; UNITS; SIZE; CLKV3-DWG-30; SCALE 1:1; NOTES :

Benoit Frigon
www.frigon.info

PROJECT
ALARM CLOCK V3
TITLE
ASSY - DISPLAY FRAME - FRONT
DIMENSIONS
PART #
CLKV3-AS-01

FILE : clkv3-dwg-30_assy-display-frame-front

1

2

SHEET 2 OF 5; REV; DOCUMENT #; UNITS; SIZE; CLKV3-DWG-30; SCALE 3:2; NOTES :

Benoit Frigon
www.frigon.info

PROJECT
ALARM CLOCK V3
TITLE
ASSY - DISPLAY FRAME - FRONT
ASSEMBLY - STEP 1
PART #
CLKV3-AS-01

ITEM NO. | PART NUMBER | MFG | DRAWING | DESCRIPTION | QTY.

1 | CLKV3-ML-01 | -- | CLKV3-DWG-02 | Display panel - Frame - Front | 1
2 | 240-004-BR | E-Z LOK | -- | Threaded insert - Flush - #4-40 | 5
3 | 240-002-BR | E-Z LOK | -- | Threaded insert - Flush - #2-56 | 11

FILE : clkv3-dwg-30_assy-display-frame-front

SHEET 3 OF 5; REV; DOCUMENT #; UNITS; SIZE; CLKV3-DWG-30; SCALE 3:2; NOTES :

Benoit Frigon
www.frigon.info

PROJECT
ALARM CLOCK V3
TITLE
ASSY - DISPLAY FRAME - FRONT
ASSEMBLY - STEP 2
PART #
CLKV3-AS-01

ITEM NO. | PART NUMBER | DRAWING | DESCRIPTION | QTY.

1 | CLKV3-ML-03 | CLKV3-DWG-03 | Display - front cover | 1

FILE : clkv3-dwg-30_assy-display-frame-front

SHEET 4 OF 5; REV; DOCUMENT #; UNITS; SIZE; CLKV3-DWG-30; SCALE 3:2; NOTES :

Benoit Frigon
www.frigon.info

PROJECT
ALARM CLOCK V3
TITLE
ASSY - DISPLAY FRAME - FRONT
ASSEMBLY - STEP 3
PART #
CLKV3-AS-01

ITEM NO. | PART NUMBER | DRAWING | DESCRIPTION | QTY.
1 | CLKV3-PC-01 | CLKV3-DWG-01 | Display - RGB digit PCB | 4
2 | CLKV3-PC-02 | CLKV3-DWG-06 | Display - RGB dots PCB | 3
3 | PH-C-0256-0025 | -- | Phillips Panhead Screw - #2-56 x 1-4" | 11

FILE : clkv3-dwg-30_assy-display-frame-front

1

Apply 3M 467-MP adhesive; SHEET 5 OF 5; REV; DOCUMENT #; UNITS; SIZE; CLKV3-DWG-30; SCALE 3:2; NOTES :

Benoit Frigon
www.frigon.info

PROJECT
ALARM CLOCK V3
TITLE
ASSY - DISPLAY FRAME - FRONT
ASSEMBLY - STEP 4
PART #
CLKV3-AS-01

ITEM NO. | PART NUMBER | DRAWING | DESCRIPTION | QTY.
1 | CLKV3-AS-05 | CLKV3-DWG-34 | Touch keypad ASSY | 1

FILE : clkv3-dwg-30_assy-display-frame-front

5 ³

.350

SECTION A-A; DETAIL B; SCALE 4 : 1; SHEET 1 OF 1; ALARM CLOCK V3 TITLE DISPLAY - FRAME - BACK; REV; PART # CLKV3-ML-09; DOCUMENT #; UNITS; SIZE; CLKV3-DWG-04; SCALE 1:1; PROJECT; NYLON; BLACK; DIMENSIONS

Benoit Frigon
www.frigon.info

NOTES :
MATERIAL VOLUME : 1.53 in³

FILE : clkv3-dwg-04_display-frame-back

4.850

5 ³

SHEET 1 OF 1; ALARM CLOCK V3 TITLE DISPLAY - BACK COVER; REV; PART # CLKV3-ML-02; DOCUMENT #; UNITS; SIZE; CLKV3-DWG-05; SCALE 2:1; PROJECT; 3mm ACRYLIC; BLACK; NOTES :; DIMENSIONS

Benoit Frigon
www.frigon.info

FILE : clkv3-dwg-05_display-back-cover

.500

TOP; BOTTOM; SHEET 1 OF 2; ALARM CLOCK V3 TITLE RGB LAMP PCB; REV; PART # CLKV3-PC-08; DOCUMENT #; UNITS; SIZE; CLKV3-DWG-09; SCALE 3:1; PROJECT; PCB FR4 - 1.6mm; NOTES :; DIMENSIONS

Benoit Frigon
www.frigon.info

FILE : clkv3-dwg-09_rgb-lamp-pcb

.062

.067

SHEET 2 OF 2; REV; DOCUMENT #; UNITS; SIZE; CLKV3-DWG-09; SCALE 3:1; NOTES :

Benoit Frigon
www.frigon.info

PROJECT
ALARM CLOCK V3
TITLE
RGB LAMP PCB
COMPONENTS POSITION
PART #
CLKV3-PC-08
PCB FR4 - 1.6mm

ITEM NO. | PART NUMBER | MFG | DESCRIPTION | QTY.

1 | CLKV3-PC-08 | -- | RGB Lamp PCB | 1
2 | IN-PI554FCH | Inolux | RGB LED with integrated driver | 3
3 | 4871 | Keystone Electronics | Round standoff #2-56 steel 1/16" | 2

FILE : clkv3-dwg-09_rgb-lamp-pcb

.350
R.100

SHEET 1 OF 1; REV; DOCUMENT #; UNITS; SIZE; CLKV3-DWG-19; SCALE 3:1; BLACK; NOTES :

Benoit Frigon
www.frigon.info

PROJECT
ALARM CLOCK V3
TITLE
RGB LAMP WINDOW - FRAME
DIMENSIONS
PART #
CLKV3-ML-08
1.5mm ACRYLIC

FILE : clkv3-dwg-19_rgb-lamp-window-frame

SHEET 1 OF 1; REV; DOCUMENT #; UNITS; SIZE; CLKV3-DWG-20; SCALE 3:1; CLEAR; NOTES :

Benoit Frigon
www.frigon.info

PROJECT
ALARM CLOCK V3
TITLE
RGB LAMP WINDOW - COVER
DIMENSIONS
PART #
CLKV3-ML-09
1.5mm ACRYLIC

FILE : clkv3-dwg-20_rgb-lamp-window-cover

SHEET 1 OF 4; REV; DOCUMENT #; UNITS; SIZE; CLKV3-DWG-31; SCALE 1:1; NOTES :

Benoit Frigon
www.frigon.info

PROJECT
ALARM CLOCK V3
TITLE
ASSY - DISPLAY FRAME - BACK
DIMENSIONS
PART #
CLKV3-AS-02

FILE : clkv3-dwg-31_assy-display-frame-back

SHEET 2 OF 4; REV; DOCUMENT #; UNITS; SIZE; CLKV3-DWG-31; SCALE 3:2; NOTES :

Benoit Frigon
www.frigon.info

PROJECT
ALARM CLOCK V3
TITLE
ASSY - DISPLAY FRAME - BACK
ASSEMBLY - STEP 1
PART #
CLKV3-AS-02

ITEM NO. | PART NUMBER | MFG | DRAWING | DESCRIPTION | QTY.
1 | CLKV3-ML-09 | -- | CLKV3-DWG-04 | Display panel - Frame - Back | 1
2 | 240-004-BR | E-Z LOK | -- | Threaded insert - Flush - #4-40 | 2

FILE : clkv3-dwg-31_assy-display-frame-back

SHEET 3 OF 4; REV; DOCUMENT #; UNITS; SIZE; CLKV3-DWG-31; SCALE 3:2; NOTES :

Benoit Frigon
www.frigon.info

PROJECT
ALARM CLOCK V3
TITLE
ASSY - DISPLAY FRAME - BACK
ASSEMBLY - STEP 2
PART #
CLKV3-AS-02

ITEM NO. | PART NUMBER | MFG | DRAWING | DESCRIPTION | QTY.
1 | CLKV3-ML-02 | -- | CLKV3-DWG-05 | Display panel - Back cover | 1

FILE : clkv3-dwg-31_assy-display-frame-back

SHEET 4 OF 4; REV; DOCUMENT #; UNITS; SIZE; CLKV3-DWG-31; SCALE 3:2; NOTES :

ITEM NO. | PART NUMBER | MFG | DRAWING | DESCRIPTION | QTY.

Benoit Frigon
www.frigon.info

1 | AS04008PS-4W-R | PUI Audio | -- | Speaker 8ohm 2W - 40mm x 28.3mm | 2
2 | CLKv3-PC-08 | -- | CLKV3-DWG-09 | RGB lamp PCB | 1
3 | CLKV3-ML-08 | -- | CLKV3-DWG-19 | RGB lamp window - Frame | 1
4 | CLKV3-ML-09 | -- | CLKV3-DWG-20 | RGB lamp window - Cover | 1
5 | PH-C-0256-0025 | -- | -- | Phillips Panhead Screw - #2-56 x 1-4" | 2

PROJECT
ALARM CLOCK V3
TITLE
ASSY - DISPLAY FRAME - BACK
ASSEMBLY - STEP 3
PART #
CLKV3-AS-02

FILE : clkv3-dwg-31_assy-display-frame-back

5 ³

1.243

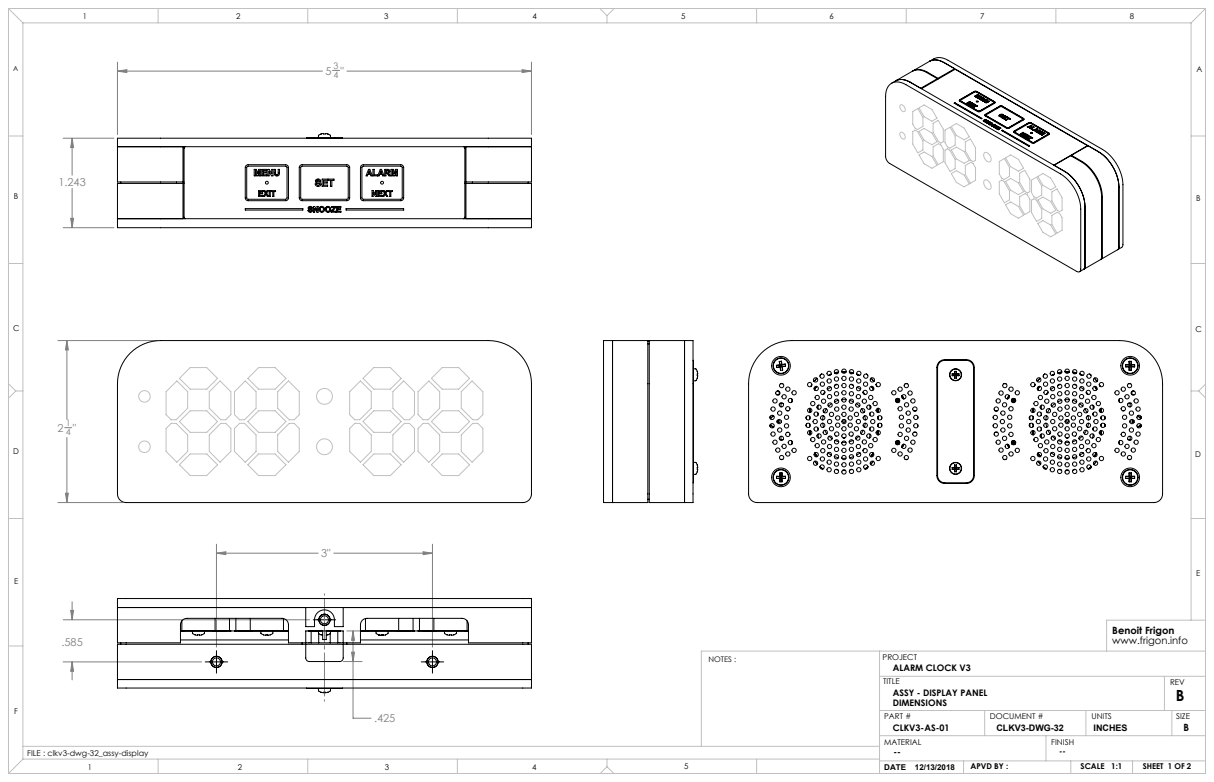
[picture p146: page 27]
SHEET 1 OF 2; ALARM CLOCK V3 TITLE ASSY - DISPLAY PANEL; REV; PART # CLKV3-AS-01; DOCUMENT #; UNITS; SIZE; CLKV3-DWG-32; SCALE 1:1; PROJECT; NOTES :; DIMENSIONS

Benoit Frigon
www.frigon.info

FILE : clkv3-dwg-32_assy-display

ITEM NO. | PART NUMBER | DRAWING | DESCRIPTION | QTY.
1 | CLKV3-AS-01 | CLKV3-DWG-30 | ASSY - Display panel - Front | 1

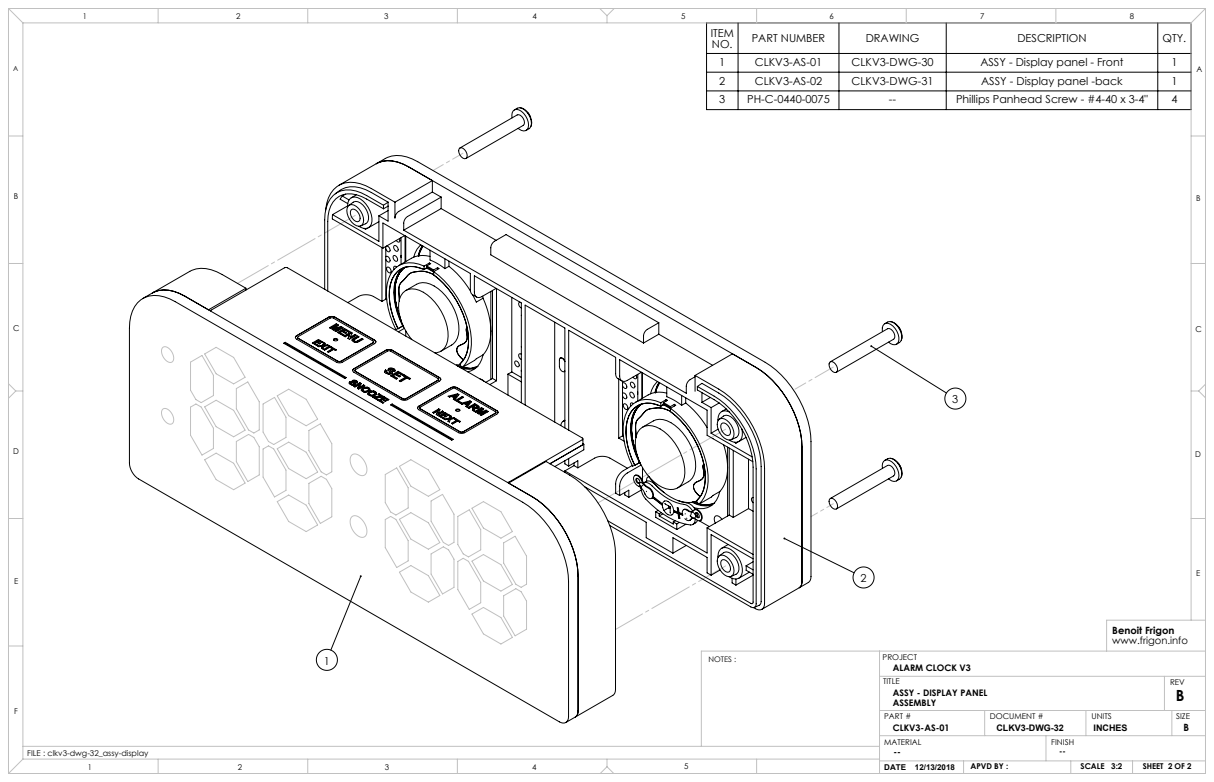
[picture p147: page 28]
SHEET 2 OF 2; ALARM CLOCK V3 TITLE ASSY - DISPLAY PANEL; REV; PART # CLKV3-AS-01; DOCUMENT #; UNITS; SIZE; CLKV3-DWG-32; SCALE 3:2; PROJECT; NOTES :; ASSEMBLY

2 | CLKV3-AS-02 | CLKV3-DWG-31 | ASSY - Display panel -back | 1
3 | PH-C-0440-0075 | -- | Phillips Panhead Screw - #4-40 x 3-4" | 4

Benoit Frigon
www.frigon.info

FILE : clkv3-dwg-32_assy-display

2"

.090

.129 THRU ALL; DETAIL A SCALE 4 : 1; DETAIL B SCALE 4 : 1; SHEET 1 OF 1; ALARM CLOCK V3 TITLE ENCLOSURE - LOWER SECTION; REV; PART # CLKV3-ML-05; DOCUMENT #; UNITS; SIZE; CLKV3-DWG-10; SCALE 5:6; PROJECT; NYLON; BLACK; DIMENSIONS

Benoit Frigon
www.frigon.info

NOTES :
MATERIAL VOLUME : 2.31 in³

FILE : clkv3-dwg-10_enclosure-lower-section

5.900

2"

SECTION A-A; DETAIL B SCALE 4 : 1; DETAIL C SCALE 6 : 1; SHEET 1 OF 2; ALARM CLOCK V3 TITLE ENCLOSURE - UPPER SECTION; REV; PART # CLKV3-ML-06; DOCUMENT #; UNITS; SIZE; CLKV3-DWG-11; SCALE 5:6; PROJECT; NYLON; BLACK; DIMENSIONS

Benoit Frigon
www.frigon.info

NOTES :
MATERIAL VOLUME : 1.58 in³

FILE : clkv3-dwg-11_enclosure-upper-section

5.720

.010

SECTION D-D; DETAIL E SCALE 16 : 1; SHEET 2 OF 2; ALARM CLOCK V3 TITLE ENCLOSURE - UPPER SECTION; REV; PART # CLKV3-ML-06; DOCUMENT #; UNITS; SIZE; CLKV3-DWG-11; SCALE 1:1; PROJECT; NYLON; BLACK; CLEARANCE

Benoit Frigon
www.frigon.info

NOTES :
MATERIAL VOLUME : 1.58 in³

FILE : clkv3-dwg-11_enclosure-upper-section

.400

SHEET 1 OF 1; ALARM CLOCK V3 TITLE RTC BATTERY DOOR; REV; PART # CLKV3-ML-07; DOCUMENT #; UNITS; SIZE; CLKV3-DWG-18; SCALE 3:1; PROJECT; NYLON; BLACK; DIMENSIONS

Benoit Frigon
www.frigon.info

NOTES :
MATERIAL VOLUME : 0.07 in³

FILE : clkv3-dwg-18_rtc-battery-door

.600

.210

.080 THRU ALL; SHEET 1 OF 1; ALARM CLOCK V3 TITLE ENCLOSURE - BACK PANEL; REV; PART # CLKV3-ML-10; DOCUMENT #; UNITS; SIZE; CLKV3-DWG-13; SCALE 4:3; PROJECT; NYLON; BLACK; DIMENSIONS

Benoit Frigon
www.frigon.info

NOTES :
MATERIAL VOLUME : 0.31 in³

FILE : clkv3-dwg-13_enclosure-back-panel

4 ¹

paper masking; SHEET 1 OF 1; ALARM CLOCK V3 TITLE FRONT PANEL WINDOW; REV; PART # CLKV3-ML-11; DOCUMENT #; UNITS; SIZE; CLKV3-DWG-21; SCALE 2:1; PROJECT; 1.5mm ACRYLIC; CLEAR; NOTES :; DIMENSIONS

Remove paper masking and paint black

Benoit Frigon
www.frigon.info

FILE : clkv3-dwg-21_front-panel-window

1.300

SHEET 1 OF 2; ALARM CLOCK V3 TITLE ALARM SWITCH PCB; REV; PART # CLKV3-PC-09; DOCUMENT #; UNITS; SIZE; CLKV3-DWG-17; SCALE 4:1; PROJECT; PCB FR4 - 1.6mm; NOTES :; DIMENSIONS

Benoit Frigon
www.frigon.info

FILE : clkv3-dwg-17_alarm-switch-pcb

.650

ITEM NO. | PART NUMBER | MFG | DESCRIPTION | QTY.

SHEET 2 OF 2; REV; DOCUMENT #; UNITS; SIZE; CLKV3-DWG-17; SCALE 3:1; NOTES :

1 | CLKV3-PC-09 | -- | Alarm switch PCB | 1
2 | L102011ML04Q | C&K Components | Slide switch SPDT - T/H - R/A | 1

Benoit Frigon
www.frigon.info

PROJECT
ALARM CLOCK V3
TITLE
ALARM SWITCH PCB
COMPONENTS POSITION
PART #
CLKV3-PC-09
PCB FR4 - 1.6mm

FILE : clkv3-dwg-17_alarm-switch-pcb

3.900

1.425 | .650

SHEET 1 OF 2; ALARM CLOCK V3 TITLE MOTHERBOARD PCB; REV; PART # CLKV3-PC-05; DOCUMENT #; UNITS; SIZE; CLKV3-DWG-14; SCALE 3:2; PROJECT; PCB FR4 - 1.6mm; NOTES :; DIMENSIONS

Benoit Frigon
www.frigon.info

FILE : clkv3-dwg-14_motherboard-pcb

.150

1.175

SHEET 2 OF 2; ALARM CLOCK V3 TITLE MOTHERBOARD PCB; REV; PART # CLKV3-PC-05; DOCUMENT #; UNITS; SIZE; CLKV3-DWG-14; SCALE 3:2; PROJECT; PCB FR4 - 1.6mm; NOTES :; COMPONENTS POSITION

ITEM NO. | PART NUMBER | MFG | DESCRIPTION | QTY.

1 | CLKV3-PC-05 | -- | Motherboard PCB | 1
2 | PJ1-021-SMT | CUI inc. | DC barrel Jack | 1
3 | UX60SC-MB-5ST | Hirose | USB Connector - Type B | 1
4 | 475710001 | Molex | Micro SD connector | 1
5 | DW-08-07-T-D-200 | Samtec | Header .100" - 2x8 - stack .200" | 1
6 | DW-04-07-TM-S-200 | Samtec | Header .100" - 1x4 - stack .200" | 1
7 | CES-103-01-T-D | Samtec | Header female .100" - 2x3 | 2
8 | DW-02-07-T-S-200 | Samtec | Header .100" - 1x2 - stack .200" | 1
9 | BCS-103-L-D-TE | Samtec | Header female .100" - 2x3 - .290" height | 1
10 | BCS-104-L-S-TE | Samtec | Header female .100" - 1x4 - .290" height | 1
11 | B3F-1000 | Omron | Momentary SPST switch | 1
12 | S8411-45R | Harwin inc. | CR1220 battery holder | 1

Benoit Frigon
www.frigon.info

FILE : clkv3-dwg-14_motherboard-pcb

.150 | 1.600 | .900

SHEET 1 OF 2; ALARM CLOCK V3 TITLE DAUGHTERBOARD PCB; REV; PART # CLKV3-PC-06; DOCUMENT #; UNITS; SIZE; CLKV3-DWG-15; SCALE 3:1; PROJECT; PCB FR4 - 1.6mm; NOTES :; DIMENSIONS

Benoit Frigon
www.frigon.info

FILE : clkv3-dwg-15_daughterboard-pcb

ITEM NO. | PART NUMBER | MFG | DESCRIPTION | QTY.
1 | CLKV3-PC-06 | -- | Daughterboard PCB | 1

SHEET 2 OF 2; ALARM CLOCK V3 TITLE DAUGHTERBOARD PCB; REV; PART # CLKV3-PC-06; DOCUMENT #; UNITS; SIZE; CLKV3-DWG-15; SCALE 2:1; PROJECT; PCB FR4 - 1.6mm; NOTES :; COMPONENTS POSITION

2 | DF3A-8P-2DSA | Hirose | Header 2mm - 8 pos - Vertical | 1
3 | DF3A-3P-2DSA | Hirose | Header 2mm - 3 pos - Vertical | 1
4 | DF3A-4P-2DSA | Hirose | Header 2mm - 4 pos - Vertical | 1
5 | DF3A-2P-2DSA | Hirose | Header 2mm - 2 pos - Vertical | 1

Benoit Frigon
www.frigon.info

FILE : clkv3-dwg-15_daughterboard-pcb

1.600
.129

SHEET 1 OF 3; ALARM CLOCK V3 TITLE PSU PCB; REV; PART # CLKV3-PC-07; DOCUMENT #; UNITS; SIZE; CLKV3-DWG-16; SCALE 3:1; PROJECT; PCB FR4 - 1.6mm; NOTES :; DIMENSIONS

Benoit Frigon
www.frigon.info

FILE : clkv3-dwg-16_psu-pcb

.075

.225

BOTTOM; TOP; SHEET 2 OF 3; ALARM CLOCK V3 TITLE PSU PCB; REV; PART # CLKV3-PC-07; DOCUMENT #; UNITS; SIZE; CLKV3-DWG-16; SCALE 3:1; PROJECT; PCB FR4 - 1.6mm; NOTES :; COMPONENTS POSITION

ITEM NO. | PART NUMBER | MFG | DESCRIPTION | QTY.

1 | CLKV3-PC-07 | -- | PSU PCB | 1
2 | TSW-104-07-F-S | Samtec | Header male .100" - 1x4 | 1
3 | TSW-103-07-F-D | Samtec | Header male .100" - 2x3 | 1
4 | S2B-PH-K | JST | Connector 2mm pitch, 2 pos, R/A | 1

Benoit Frigon
www.frigon.info

FILE : clkv3-dwg-16_psu-pcb

.394 Stack height; .291 Max. clerance; SECTION A-A; SHEET 3 OF 3; ALARM CLOCK V3 TITLE PSU PCB; REV; PART # CLKV3-PC-07; DOCUMENT #; UNITS; SIZE; CLKV3-DWG-16; SCALE 3:2; PROJECT; PCB FR4 - 1.6mm; NOTES :; CLEARANCE

Benoit Frigon
www.frigon.info

FILE : clkv3-dwg-16_psu-pcb

.325

1.680

SHEET 1 OF 1; ALARM CLOCK V3 TITLE BATTERY HOLDER; REV; PART # CLKV3-ML-12; DOCUMENT #; UNITS; SIZE; CLKV3-DWG-22; SCALE 2:1; PROJECT; NYLON; WHITE; DIMENSIONS

Benoit Frigon
www.frigon.info

NOTES :
MATERIAL VOLUME : 0.28 in³

FILE : clkv3-dwg-22_battery-holder

3.900

.475

SHEET 1 OF 2; ALARM CLOCK V3 TITLE FRONT PANEL PCB; REV; PART # CLKV3-PC-04; DOCUMENT #; UNITS; SIZE; CLKV3-DWG-12; SCALE 2:1; PROJECT; PCB FR4 - 1.6mm; NOTES :; DIMENSIONS

Benoit Frigon
www.frigon.info

FILE : clkv3-dwg-12_front-panel-pcb

SHEET 2 OF 2; REV; DOCUMENT #; UNITS; SIZE; CLKV3-DWG-12; SCALE 2:1; NOTES :

Benoit Frigon
www.frigon.info

PROJECT
ALARM CLOCK V3
TITLE
FRONT PANEL PCB
COMPONENTS POSITION
PART #
CLKV3-PC-04
PCB FR4 - 1.6mm

ITEM NO. | PART NUMBER | MFG | DESCRIPTION | QTY.
1 | CLKV3-PC-04 | -- | Front panel PCB | 1
2 | ER-OLED1602-4W | EastRising | 16x2 Character OLED display | 1
3 | TSL2561T | AMS-TAOS USA Inc. | IC Light to digital converter | 1

FILE : clkv3-dwg-12_front-panel-pcb

3.900
2.650

SHEET 1 OF 3; ALARM CLOCK V3 TITLE ASSY - MOTHERBOARD; REV; PART # CLKV3-AS-04; DOCUMENT #; UNITS; SIZE; CLKV3-DWG-33; SCALE 1:1; PROJECT; NOTES :; DIMENSIONS

Benoit Frigon
www.frigon.info

FILE : clkv3-dwg-33_assy-motherboard

2

ITEM NO. | PART NUMBER | DRAWING | DESCRIPTION | QTY.

SHEET 2 OF 3; ALARM CLOCK V3 TITLE ASSY - MOTHERBOARD; REV; PART # CLKV3-AS-04; DOCUMENT #; UNITS; SIZE; CLKV3-DWG-33; SCALE 3:2; PROJECT; NOTES :; ASSEMBLY - STEP 1

1 | CLKV3-PC-05 | CLKV3-DWG-14 | Motherboard PCB | 1
2 | CLKV3-PC-06 | CLKV3-DWG-15 | Daughterboard PCB | 1

Benoit Frigon
www.frigon.info

FILE : clkv3-dwg-33_assy-motherboard

ITEM NO. | PART NUMBER | DRAWING | DESCRIPTION | QTY.
1 | CLKV3-PC-04 | CLKV3-DWG-12 | Front panel PCB | 1

1. WELD HERE; SHEET 3 OF 3; ALARM CLOCK V3 TITLE ASSY - MOTHERBOARD; REV; PART # CLKV3-AS-04; DOCUMENT #; UNITS; SIZE; CLKV3-DWG-33; SCALE 1:1; PROJECT; NOTES :; ASSEMBLY - STEP 2

2 | CLKV3-JG-02 | CLKV3-DWG-51 | Motherboard assembly JIG | 2

2. Remove assembly jig and
weld remaining tabs

Benoit Frigon
www.frigon.info

FILE : clkv3-dwg-33_assy-motherboard

5.900

SHEET 1 OF 9; ALARM CLOCK V3 TITLE FINAL ASSEMBLY; REV; PART # CLKV3; DOCUMENT #; UNITS; SIZE; CLKV3-DWG-35; SCALE 2:3; PROJECT; NOTES :; DIMENSIONS

Benoit Frigon
www.frigon.info

FILE : clkv3-dwg-35_final-assembly

ITEM NO. | PART NUMBER | MFG. | DRAWING | DESCRIPTION | QTY.
1 | 240-004-BR | E-Z LOK | -- | Threaded insert - Flush - #4-40 | 5

SHEET 2 OF 9; ALARM CLOCK V3 TITLE FINAL ASSEMBLY; REV; PART # CLKV3; DOCUMENT #; UNITS; SIZE; CLKV3-DWG-35; SCALE 3:2; PROJECT; NOTES :; STEP 1

2 | CLKV3-ML-05 | -- | CLKV3-DWG-10 | Enclosure - Lower section | 1

Benoit Frigon
www.frigon.info

FILE : clkv3-dwg-35_final-assembly

1

2

SHEET 3 OF 9; ALARM CLOCK V3 TITLE FINAL ASSEMBLY; REV; PART # CLKV3; DOCUMENT #; UNITS; SIZE; CLKV3-DWG-35; SCALE 3:2; PROJECT; NOTES :; STEP 2

ITEM NO. | PART NUMBER | DRAWING | DESCRIPTION | QTY.

1 | CLKV3-ML-10 | CLKV3-DWG-13 | Enclosure - Back panel | 1
2 | CLKV3-AS-04 | CLKV3-DWG-33 | ASSY - Motherboard | 1
3 | CLKV3-PC-09 | CLKV3-DWG-17 | Alarm switch PCB | 1
4 | PH-C-0440-0025 | -- | Phillips Panhead Screw - #4-40 x 1-4" | 4

Benoit Frigon
www.frigon.info

FILE : clkv3-dwg-35_final-assembly

2 | 1
ITEM NO. | PART NUMBER | DRAWING | MFG. | DESCRIPTION | QTY.

SHEET 4 OF 9; ALARM CLOCK V3 TITLE FINAL ASSEMBLY; REV; PART # CLKV3; DOCUMENT #; UNITS; SIZE; CLKV3-DWG-35; SCALE 3:2; PROJECT; NOTES :; STEP 3

1 | PH-C-0440-0063 | -- | -- | Phillips Panhead Screw - #4-40 x 5-8" | 1
2 | CLKV3-PC-07 | CLKV3-DWG-16 | -- | Power supply PCB | 1
3 | CLKV3-ML-12 | CLKV3-DWG-22 | -- | Battery holder | 1
4 | R30-6201014 | -- | Harwin | 10mm M3 spacer | 1

Benoit Frigon
www.frigon.info

FILE : clkv3-dwg-35_final-assembly

1

ITEM NO. | PART NUMBER | DRAWING | DESCRIPTION | QTY.

SHEET 5 OF 9; ALARM CLOCK V3 TITLE FINAL ASSEMBLY; REV; PART # CLKV3; DOCUMENT #; UNITS; SIZE; CLKV3-DWG-35; SCALE 3:2; PROJECT; NOTES :; STEP 4

1 | CLKV3-ML-11 | CLKV3-DWG-21 | Front panel window | 1

Benoit Frigon
www.frigon.info

FILE : clkv3-dwg-35_final-assembly

ITEM NO. | PART NUMBER | MFG. | DRAWING | DESCRIPTION | QTY.
1 | 240-004-BR | E-Z LOK | -- | Threaded insert - Flush - #4-40 | 4

SHEET 6 OF 9; ALARM CLOCK V3 TITLE FINAL ASSEMBLY; REV; PART # CLKV3; DOCUMENT #; UNITS; SIZE; CLKV3-DWG-35; SCALE 3:2; PROJECT; NOTES :; STEP 5

2 | CLKV3-ML-06 | -- | CLKV3-DWG-11 | Enclosure - Upper section | 1

Benoit Frigon
www.frigon.info

FILE : clkv3-dwg-35_final-assembly

2

ITEM NO. | PART NUMBER | DRAWING | DESCRIPTION | QTY.

SHEET 7 OF 9; ALARM CLOCK V3 TITLE FINAL ASSEMBLY; REV; PART # CLKV3; DOCUMENT #; UNITS; SIZE; CLKV3-DWG-35; SCALE 1:1; PROJECT; NOTES :; STEP 6

1 | PH-C-0440-0025 | -- | Phillips Panhead Screw - #4-40 x 1-4" | 3
2 | CLKV3-AS-03 | CLKV3-DWG-32 | ASSY - Display panel | 1

Benoit Frigon
www.frigon.info

FILE : clkv3-dwg-35_final-assembly

ITEM NO. | PART NUMBER | DESCRIPTION | QTY.
1 | PH-C-0440-0075 | Phillips Panhead Screw - #4-40 x 3-4" | 4

SHEET 8 OF 9; ALARM CLOCK V3 TITLE FINAL ASSEMBLY; REV; PART # CLKV3; DOCUMENT #; UNITS; SIZE; CLKV3-DWG-35; SCALE 1:1; PROJECT; NOTES :; STEP 7

Benoit Frigon
www.frigon.info

FILE : clkv3-dwg-35_final-assembly

ITEM NO. | PART NUMBER | MFG. | DRAWING | DESCRIPTION | QTY.
1 | CLKV3-ML-07 | -- | CLKV3-DWG-18 | RTC battery door | 1

SHEET 9 OF 9; ALARM CLOCK V3 TITLE FINAL ASSEMBLY; REV; PART # CLKV3; DOCUMENT #; UNITS; SIZE; CLKV3-DWG-35; SCALE 1:1; PROJECT; NOTES :; STEP 8

2 | SJ-5076 | 3M | | Bumper | 4

Benoit Frigon
www.frigon.info

FILE : clkv3-dwg-35_final-assembly
