bfrigon/alarm-clock-v3/drawings/schematics/clkv3-sch-07_psu.pdf

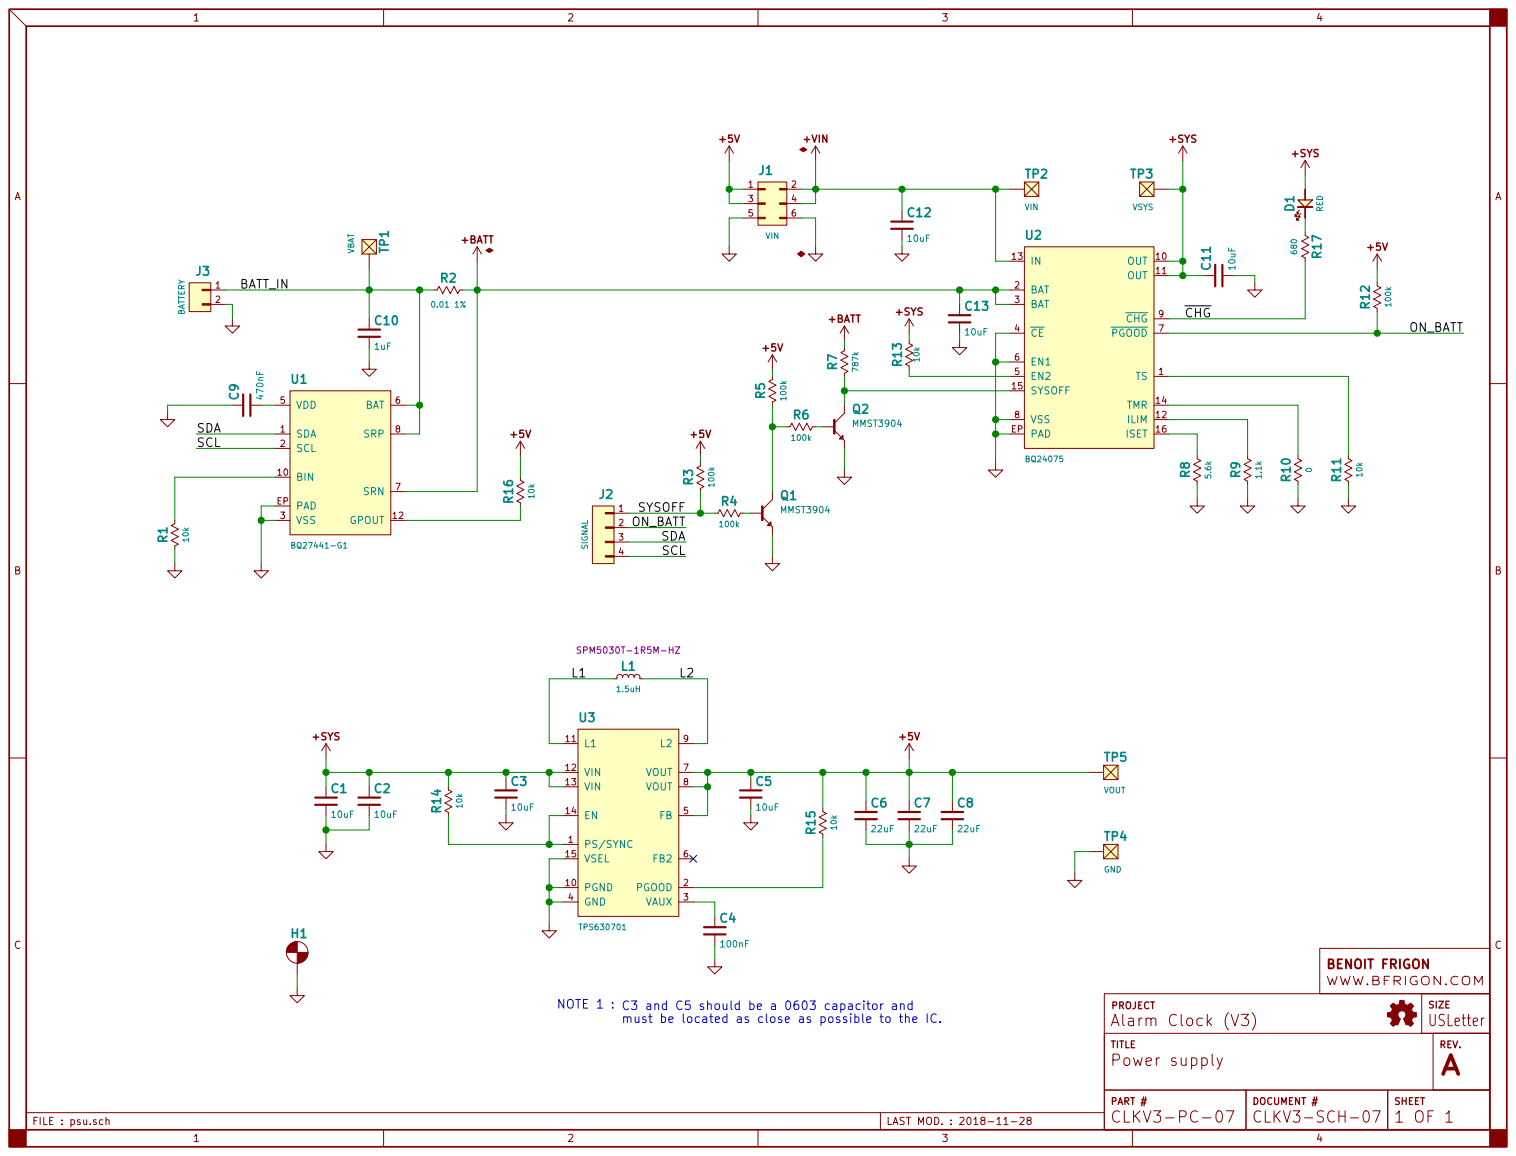
[picture p148: page 1]

REV. PROJECT Power supply
