bfrigon/alarm-clock-v3/drawings/schematics/clkv3-sch-05_motherboard.pdf

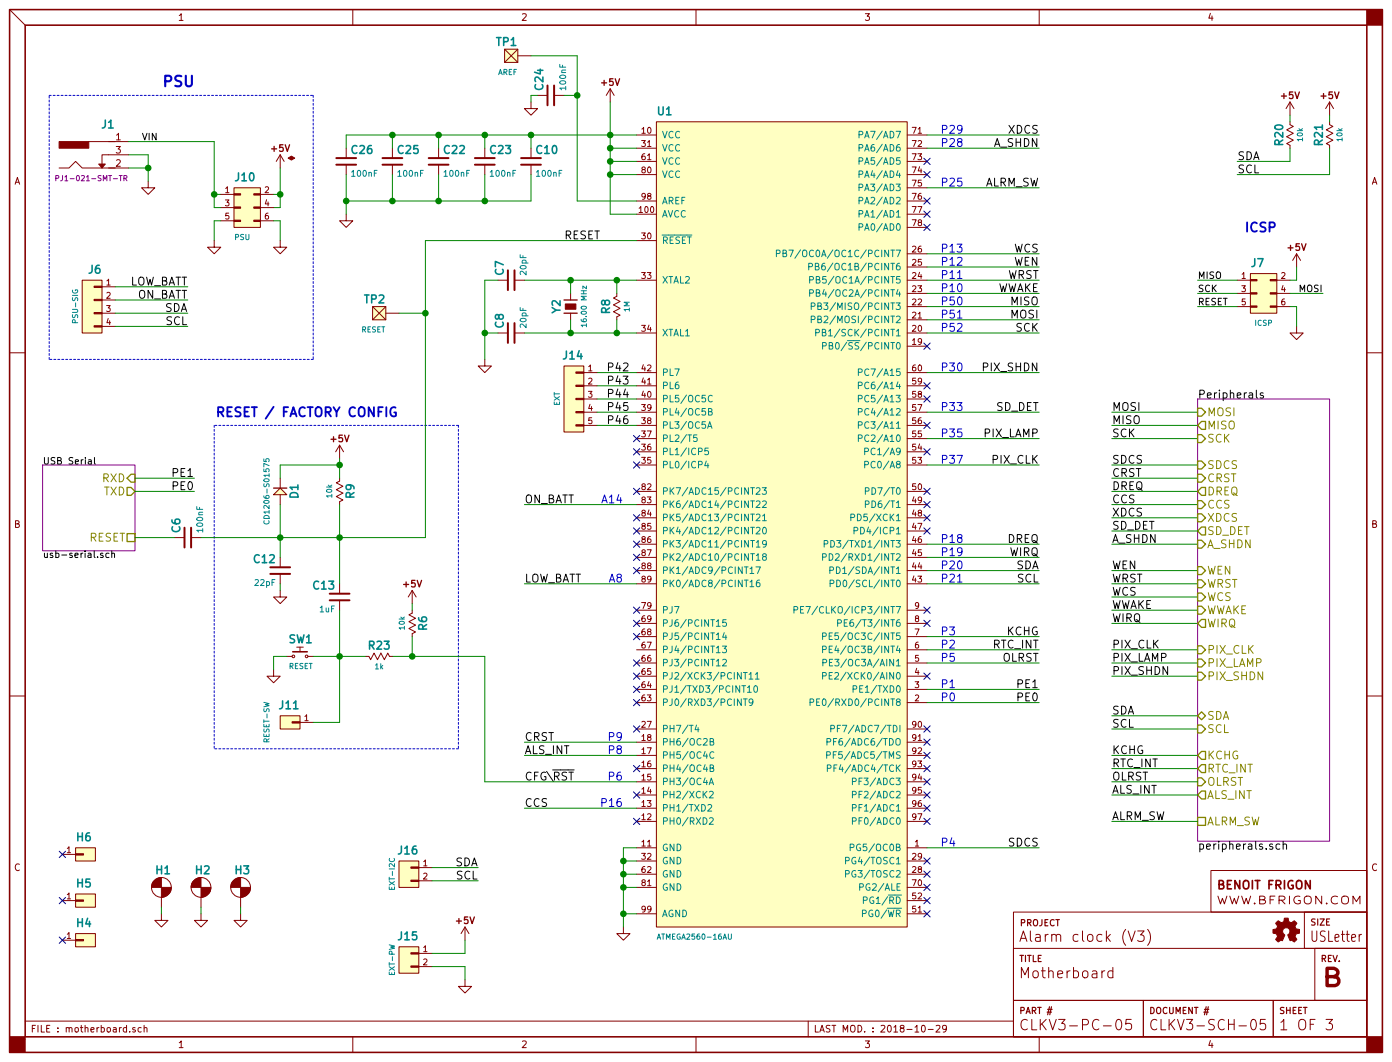
[picture p149: page 1]

+5VMOSI RESET SCK MISO MISO
WCS WWAKE

USB Serial usb-serial.sch RXD

TITLE WWW.BFRIGON.COM

PART # | | | B

DOCUMENT # CLKV3-PC-05 | SHEET CLKV3-SCH-05

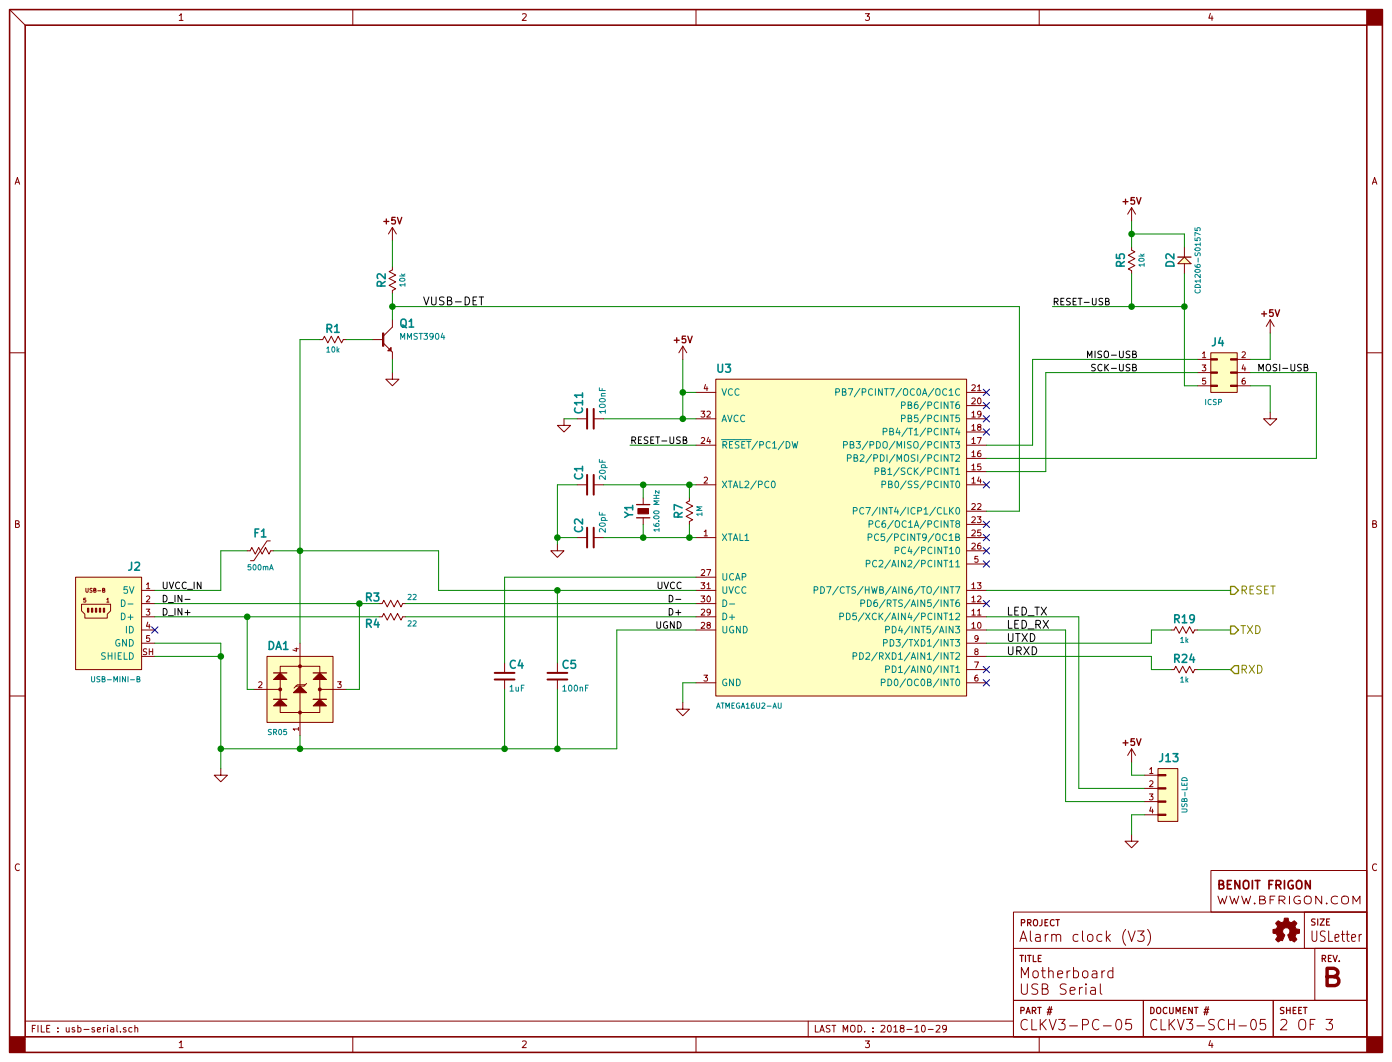
[picture p150: page 2]

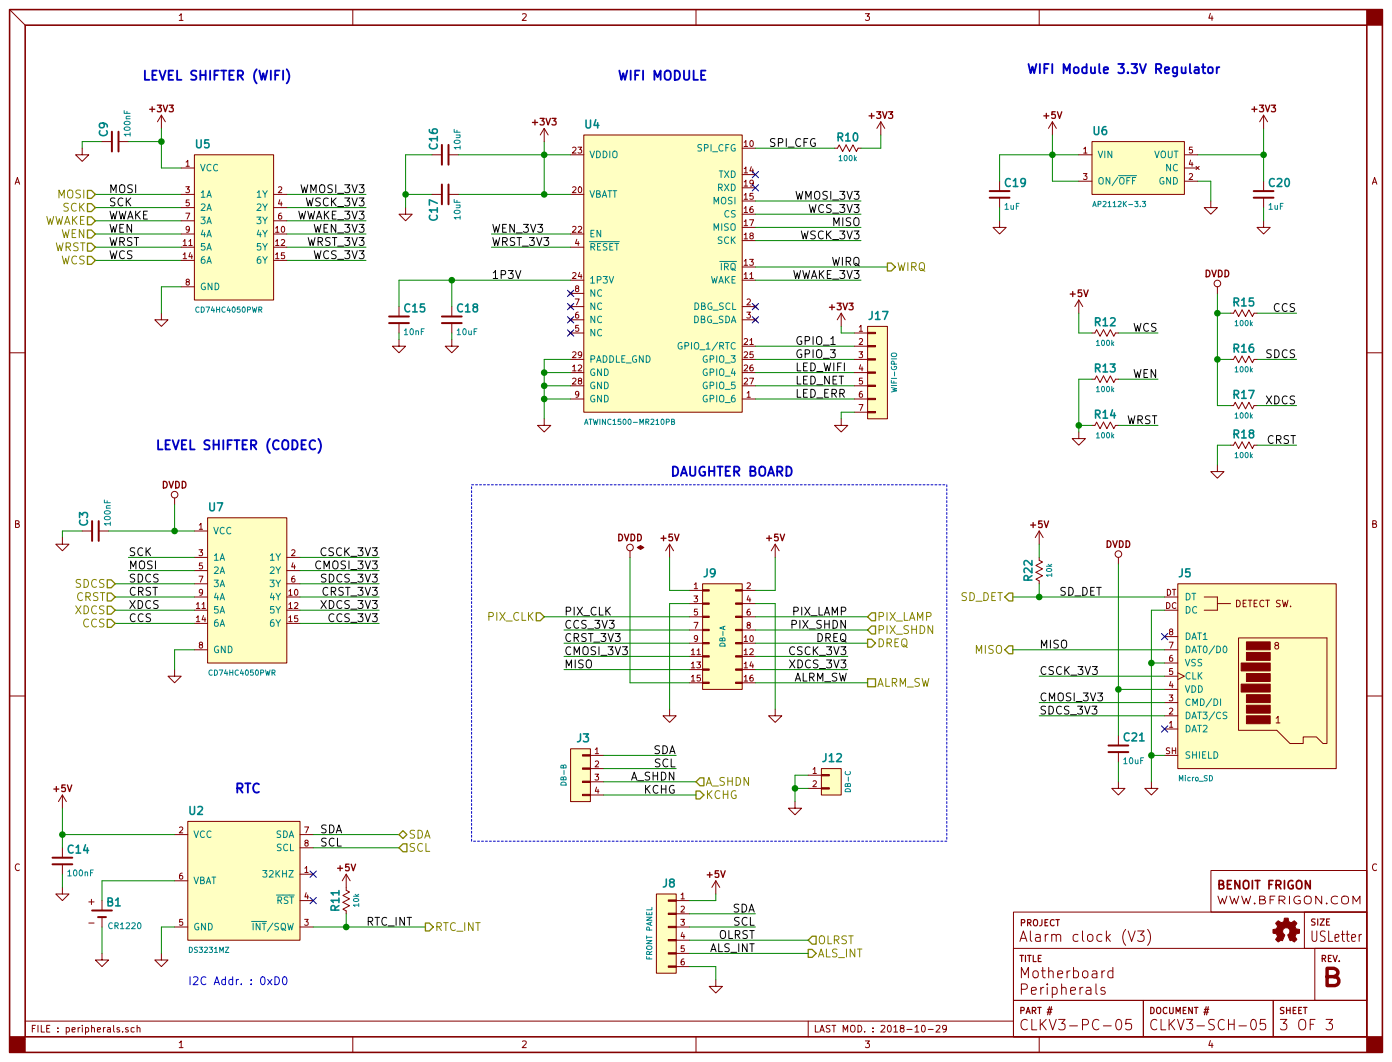
[picture p151: page 3]

MOSI
SCK WWAKE WEN WRST

GPIO_3 | 3
LED_WIFI | 4
LED_NET | 5
LED_ERR | 6

OLRST 4
