bfrigon/alarm-clock-v3/drawings/schematics/clkv3-sch-09_alarm-switch.pdf

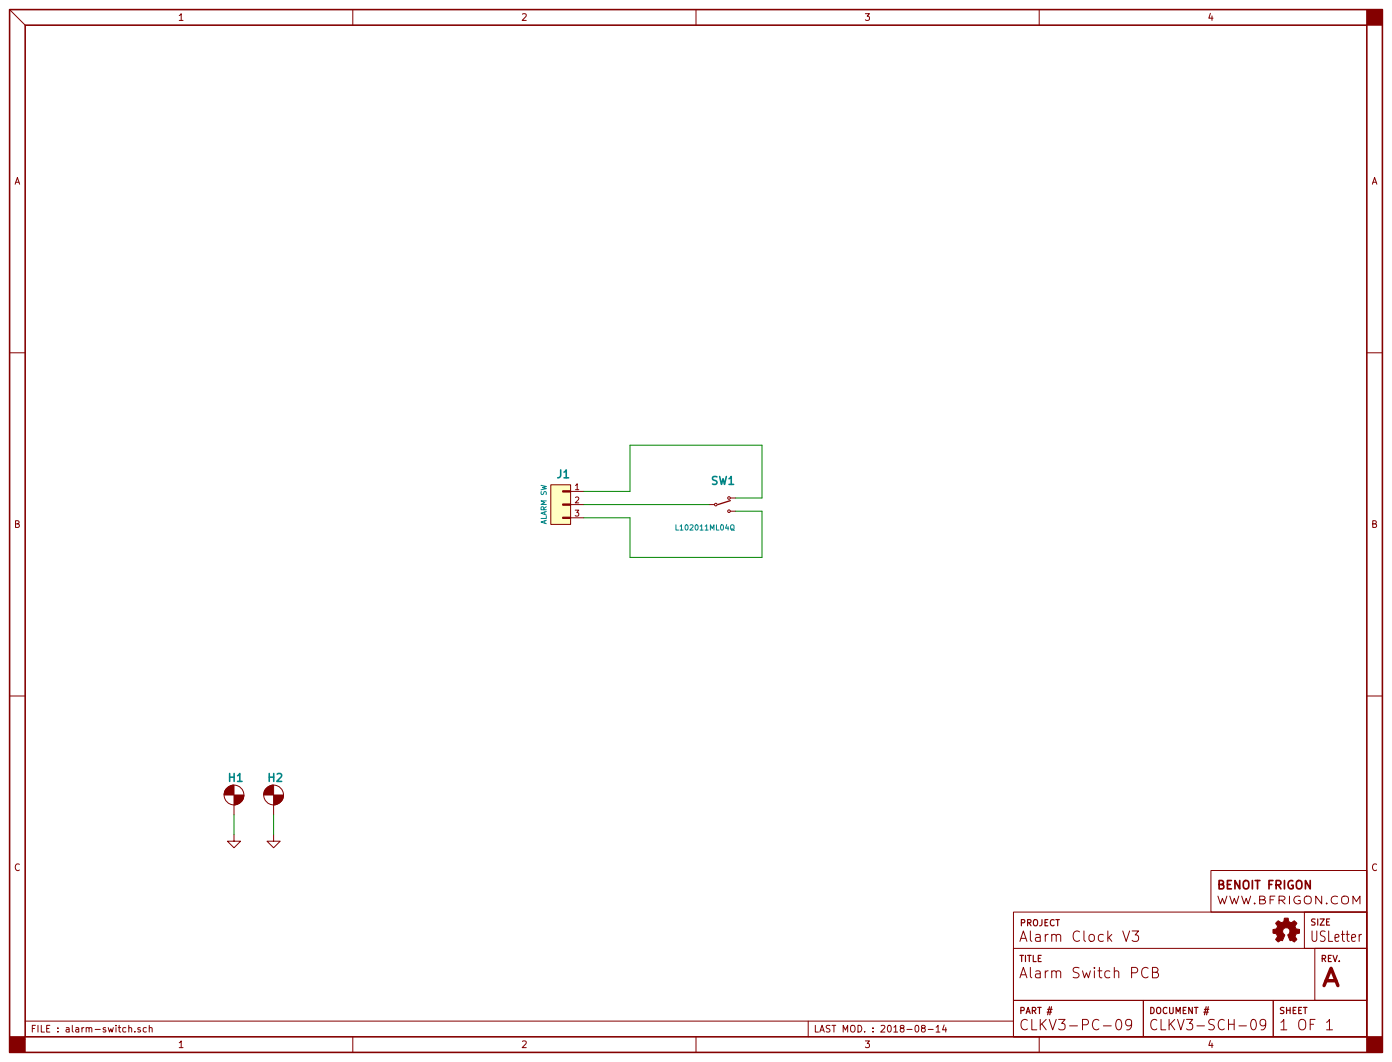
[picture p152: page 1]

REV. PROJECT Alarm Switch PCB
