bfrigon/alarm-clock-v3/fab-files/decals/sheets/decals.pdf

SD DC 5V | OFF | ON
SD DC 5V | OFF | ON

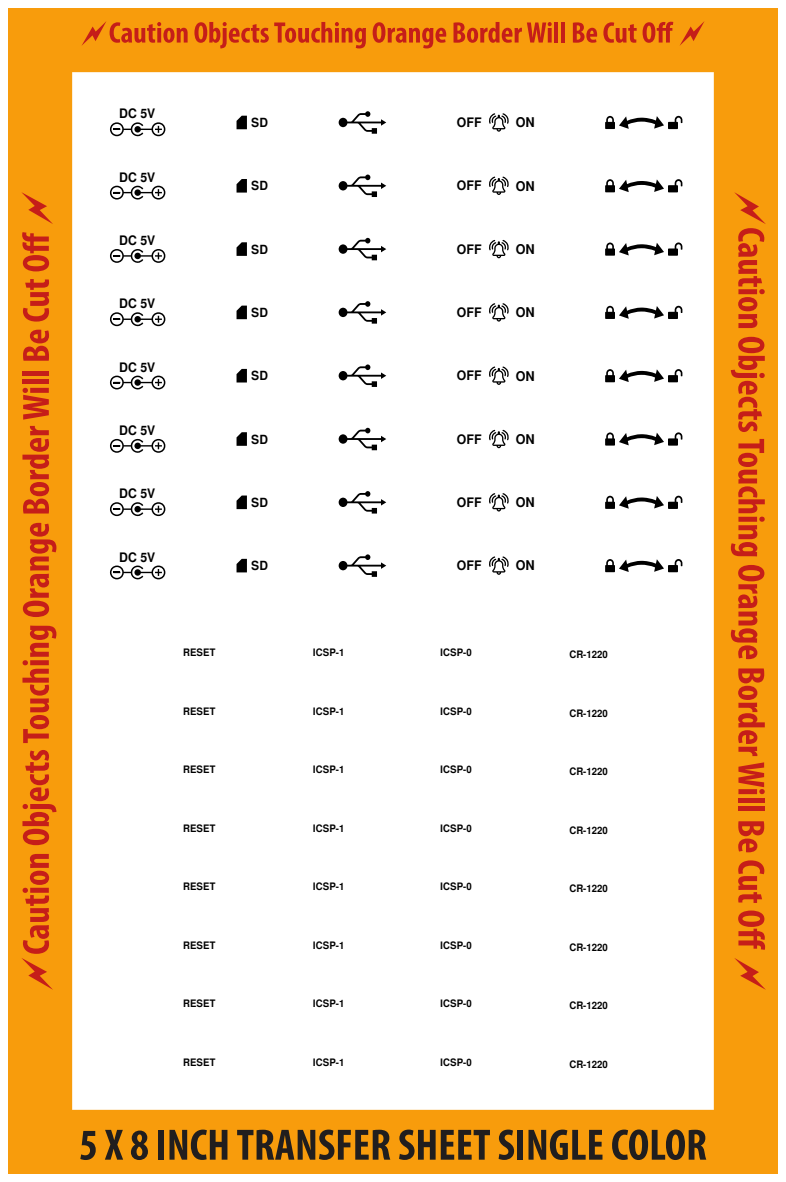
[picture p153: page 1]
RESET; ICSP-1; ICSP-0; OFF
