bfrigon/alarm-clock-v3/drawings/mechanical/clkv3-dwg-32_assy-display.pdf

SHEET 1 OF 2; ALARM CLOCK V3; ASSY - DISPLAY PANEL; PART #; DOCUMENT #; UNITS; DATE 12/13/2018; SCALE 1:1; NOTES :; APVD BY :

Benoit Frigon
www.frigon.info

FILE : clkv3-dwg-32_assy-display

SHEET 2 OF 2; ALARM CLOCK V3; ASSY - DISPLAY PANEL; PART #; DOCUMENT #; UNITS; DATE 12/13/2018; SCALE 3:2; NOTES :; APVD BY :

ITEM NO. | PART NUMBER | DRAWING | DESCRIPTION | QTY.

1 | CLKV3-AS-01 | CLKV3-DWG-30 | ASSY - Display panel - Front | 1
2 | CLKV3-AS-02 | CLKV3-DWG-31 | ASSY - Display panel -back | 1
3 | PH-C-0440-0075 | -- | Phillips Panhead Screw - #4-40 x 3-4" | 4

Benoit Frigon
www.frigon.info

FILE : clkv3-dwg-32_assy-display
