bfrigon/alarm-clock-v3/drawings/mechanical/clkv3-dwg-34_assy-touch-keypad.pdf

SHEET 1 OF 2; ALARM CLOCK V3; ASSY - TOUCH KEYPAD; PART #; DOCUMENT #; UNITS; DATE 12/13/2018; SCALE 2:1; NOTES :; APVD BY :

Benoit Frigon
www.frigon.info

FILE : clkv3-dwg-34_assy-touch-keypad

Apply 3M 467-MP adhesive; SHEET 2 OF 2; ALARM CLOCK V3; ASSY - TOUCH KEYPAD; PART #; DOCUMENT #; UNITS; DATE 12/13/2018; SCALE 2:1; NOTES :; APVD BY :

Benoit Frigon
www.frigon.info

ITEM NO. | PART NUMBER | DRAWING | DESCRIPTION | QTY.

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

FILE : clkv3-dwg-34_assy-touch-keypad
