bfrigon/alarm-clock-v3/drawings/schematics/clkv3-sch-03_touch-keypad.pdf

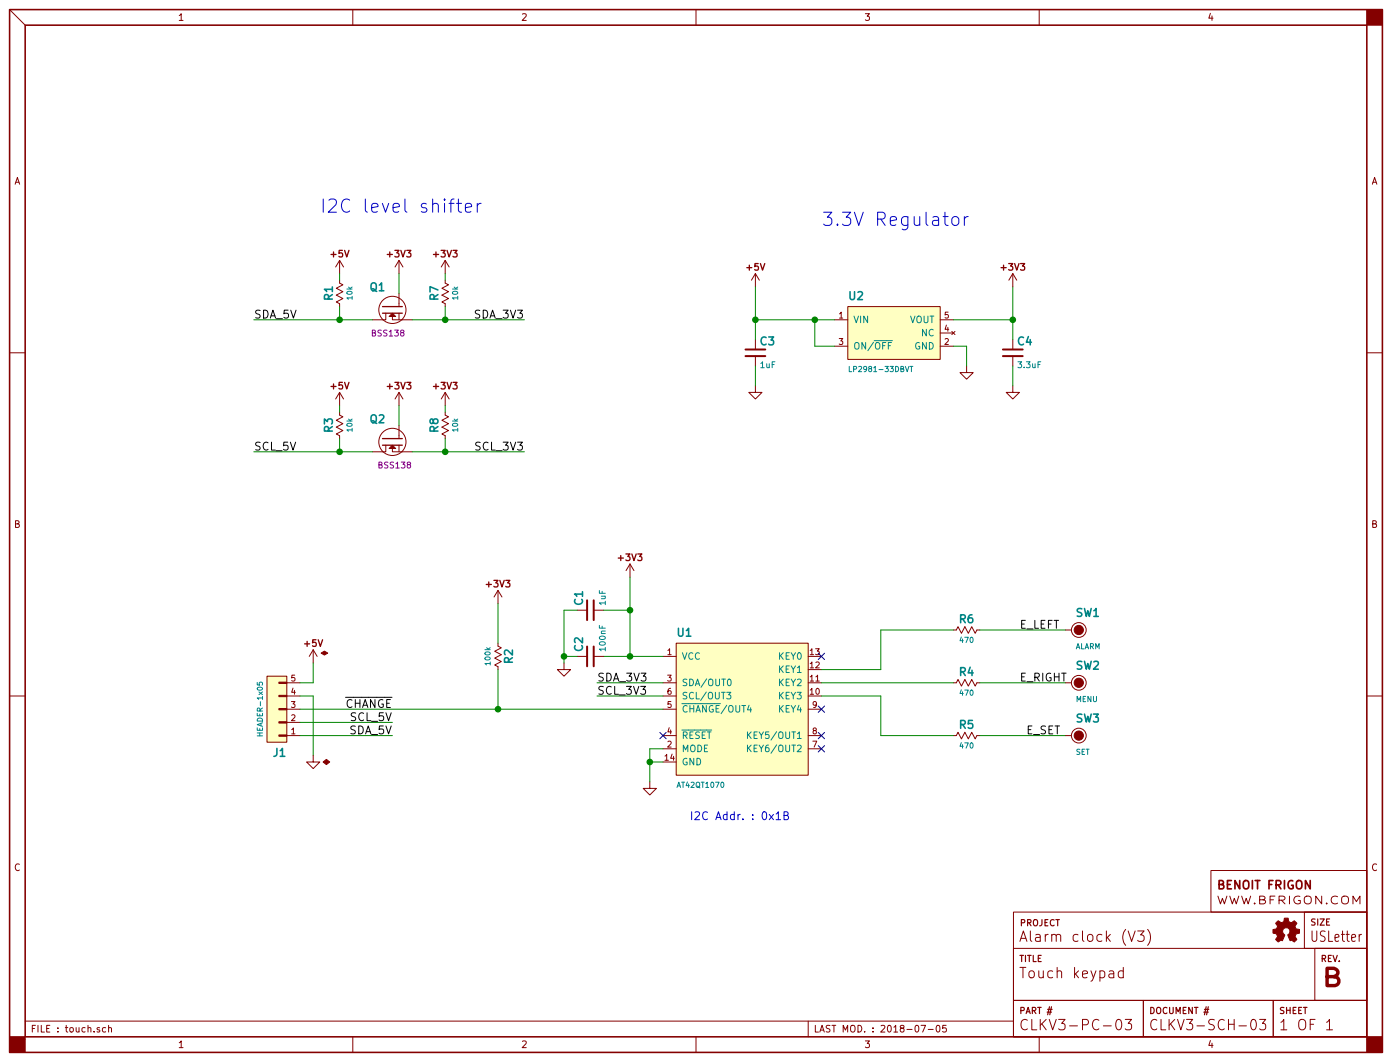
[picture p154: page 1]

TITLE WWW.BFRIGON.COM

REV. PROJECT Touch keypad

PART # | | | B

DOCUMENT # CLKV3-PC-03 | SHEET CLKV3-SCH-03
