bfrigon/alarm-clock-v3/drawings/schematics/clkv3-sch-04_front-panel.pdf

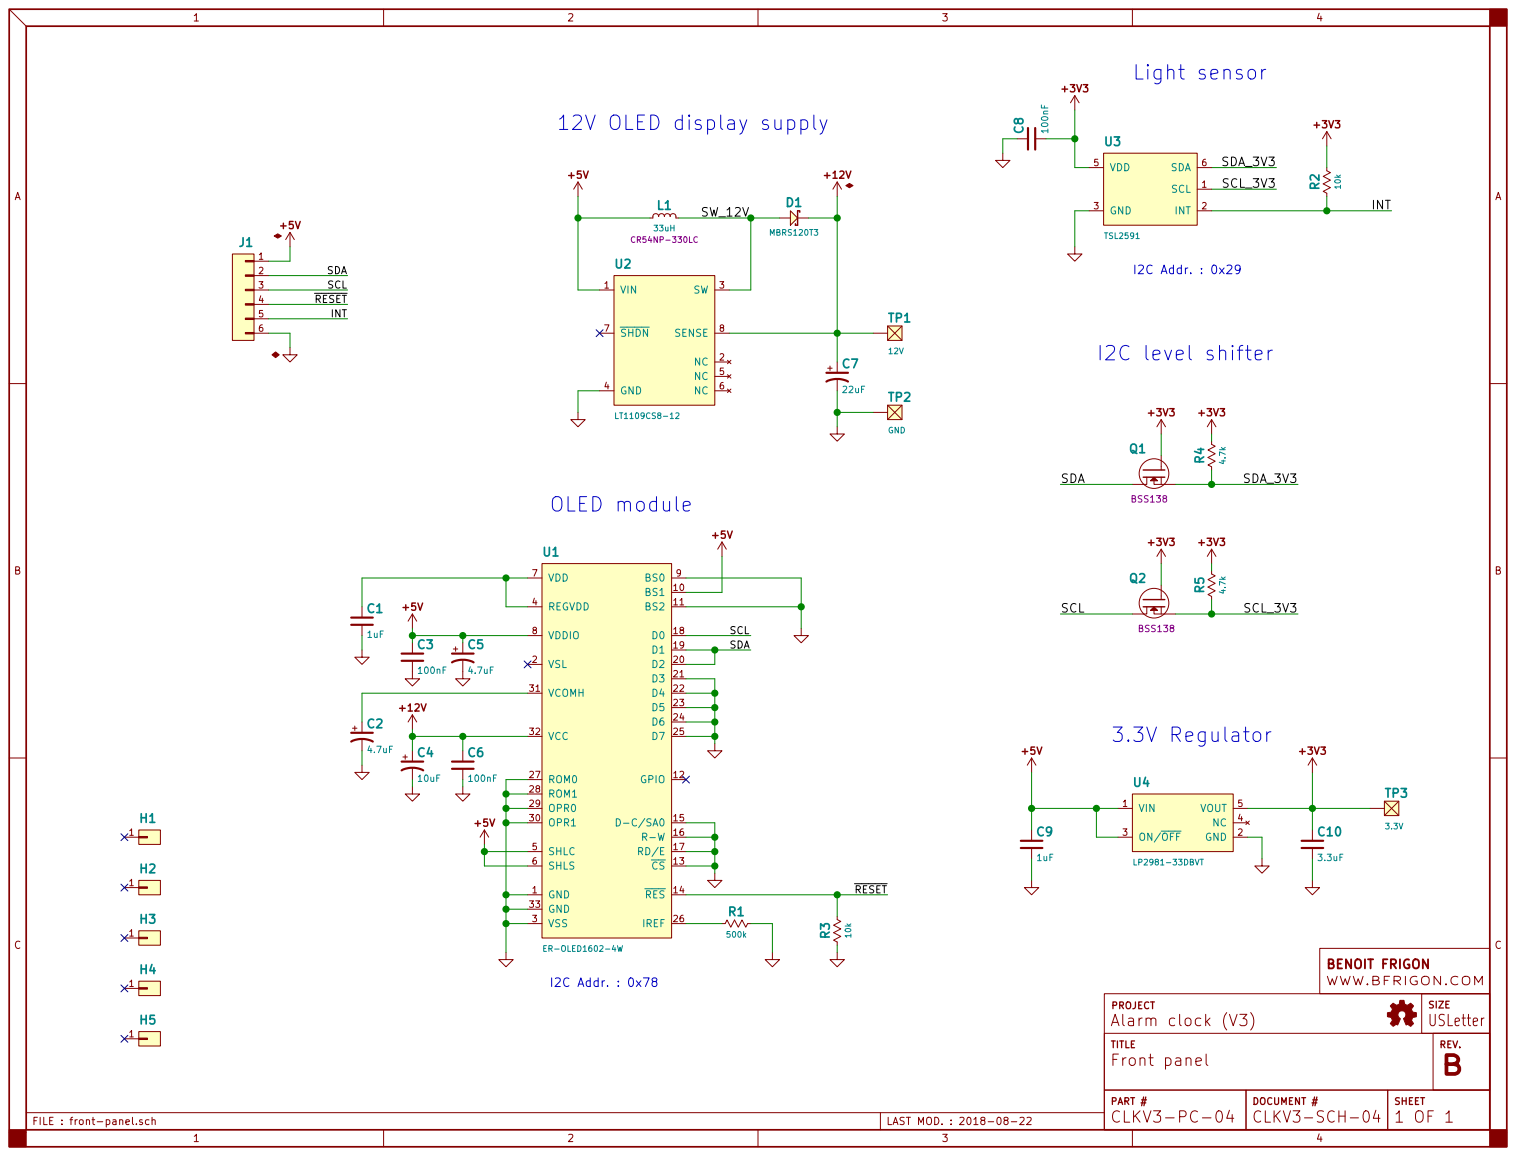
[picture p155: page 1]

PART # | | B

DOCUMENT # CLKV3-PC-04 | SHEET CLKV3-SCH-04
