bfrigon/alarm-clock-v3/drawings/schematics/clkv3-sch-06_daughterboard.pdf

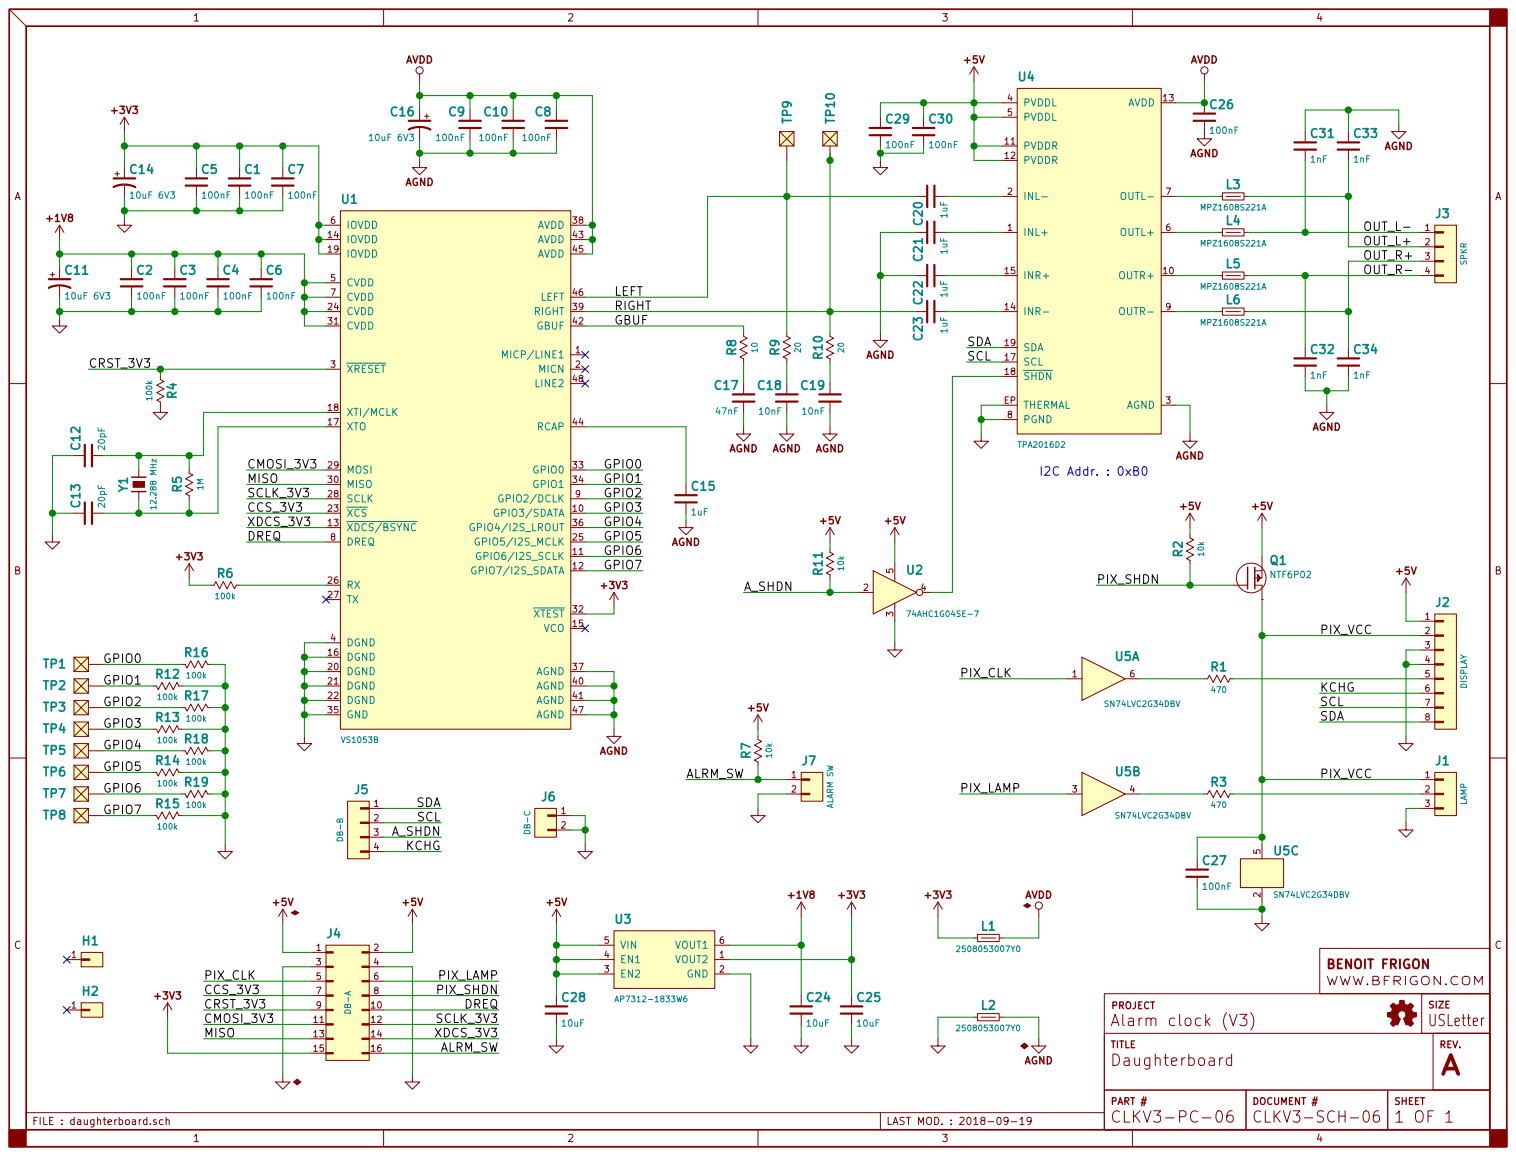
[picture p156: page 1]
