bfrigon/alarm-clock-v3/drawings/schematics/clkv3-sch-01_rgb-digits.pdf

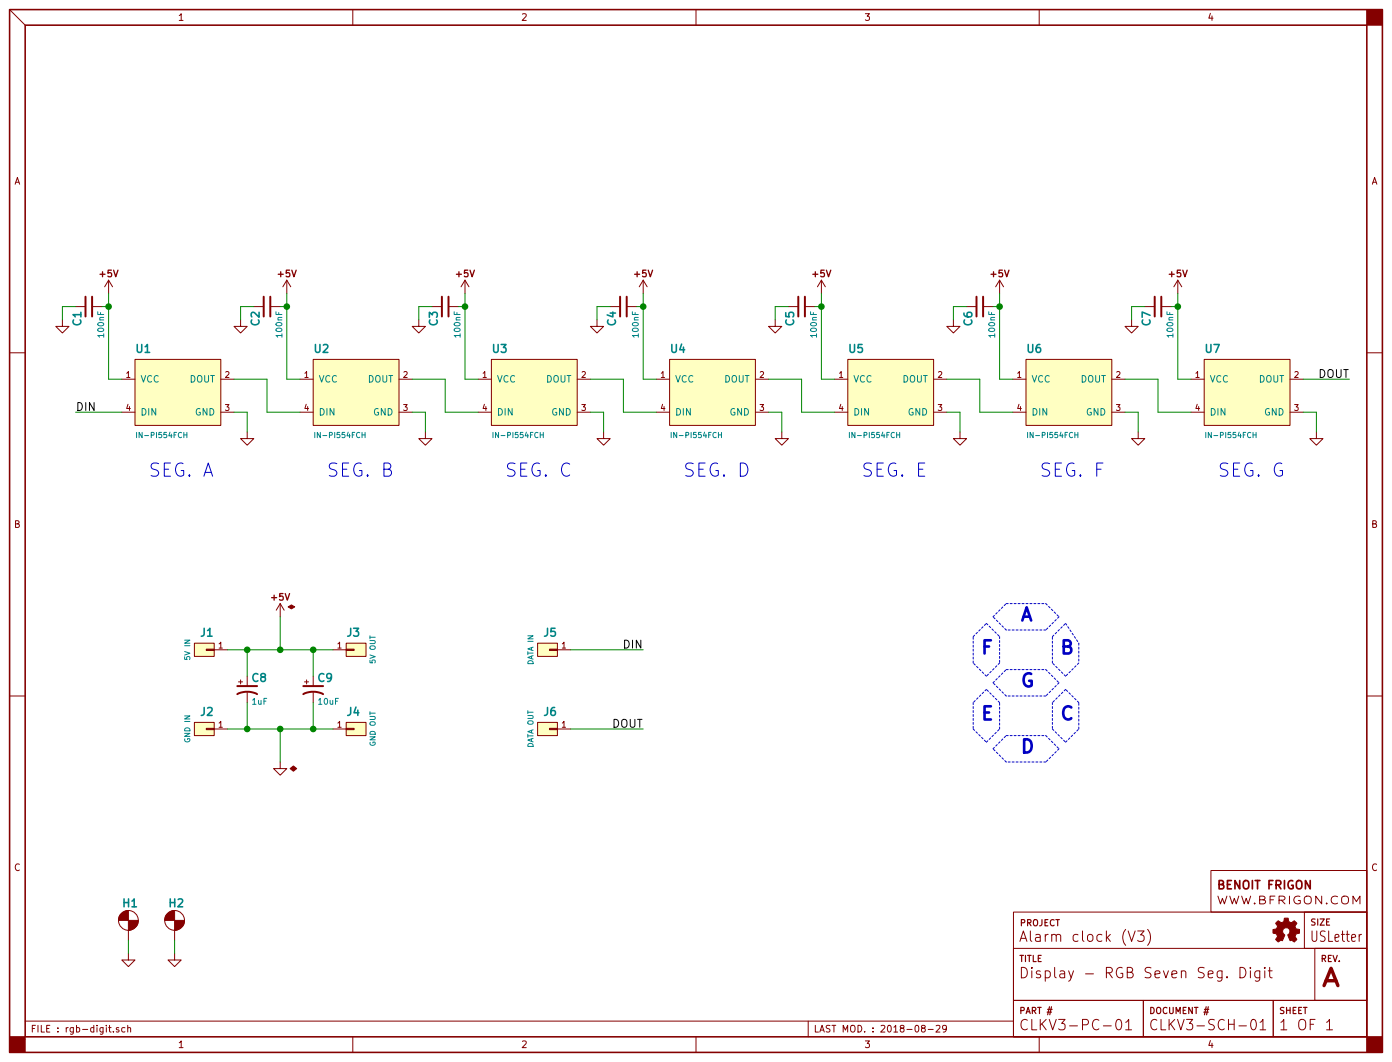
[picture p157: page 1]
