bfrigon/alarm-clock-v3/drawings/schematics/clkv3-sch-02_rgb-dots.pdf

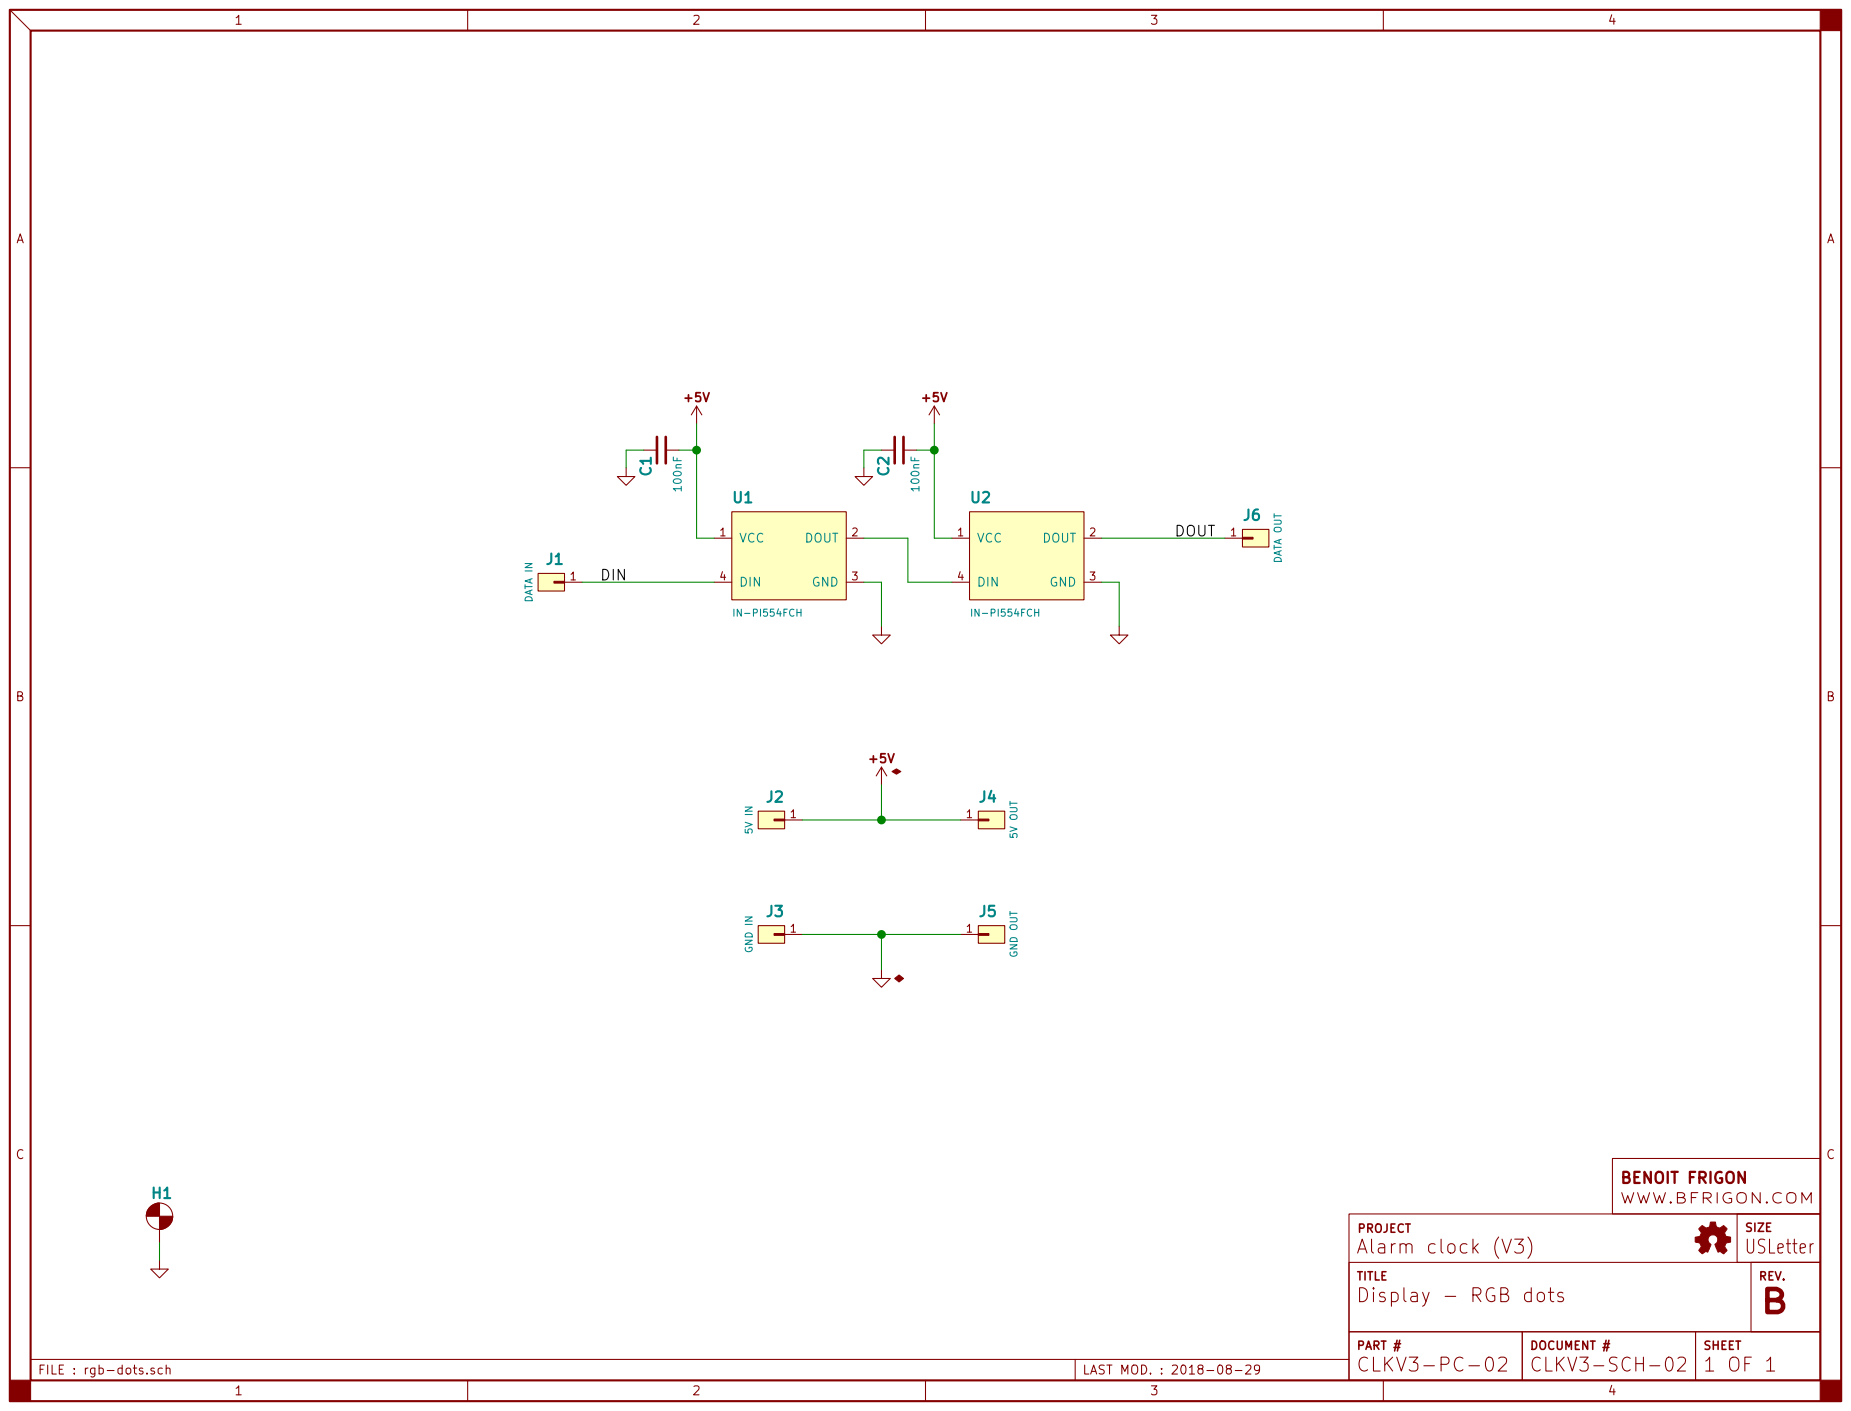
[picture p158: page 1]

1 J6 DATA OUT DOUT DIN

TITLE WWW.BFRIGON.COM

REV. PROJECT Display - RGB dots

PART # | | | B

DOCUMENT # CLKV3-PC-02 | SHEET CLKV3-SCH-02
