bfrigon/alarm-clock-v3/drawings/schematics/clkv3-sch-08_rgb-lamp.pdf

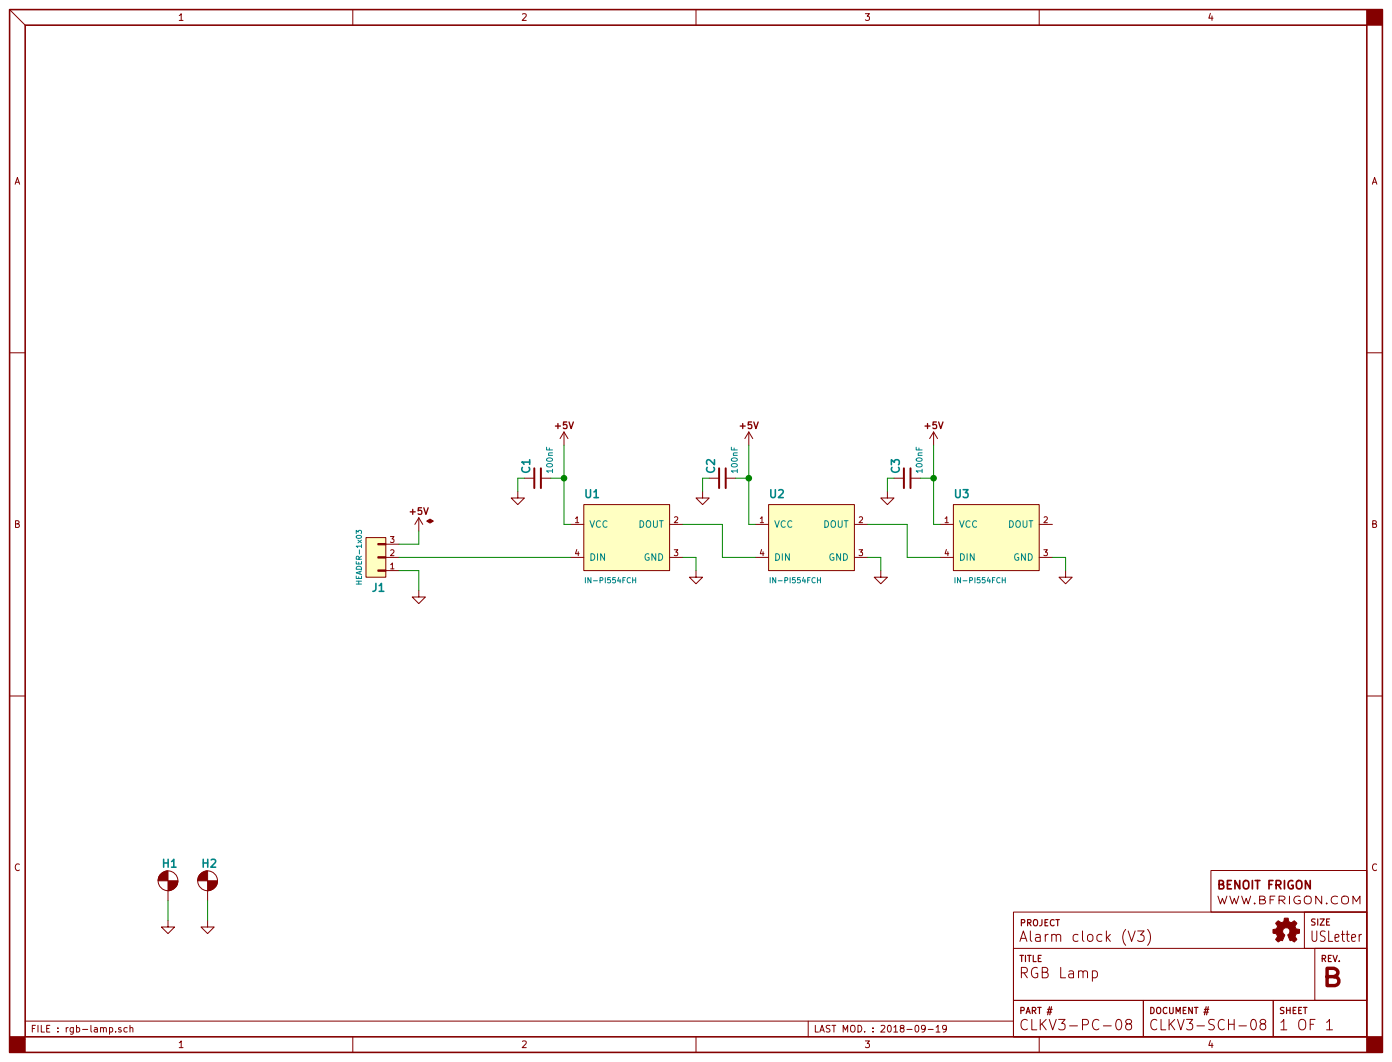
[picture p159: page 1]

TITLE WWW.BFRIGON.COM

REV. PROJECT RGB Lamp

PART # | | | B

DOCUMENT # CLKV3-PC-08 | SHEET CLKV3-SCH-08
