bfrigon/alarm-clock-v3/firmware/src/console/ansi_art.h

//******************************************************************************
//
// Project : Alarm Clock V3
// File    : src/console/ansi_art.h
// Author  : Benoit Frigon <www.bfrigon.com>
//
// For Juliette...
//
// -----------------------------------------------------------------------------
//
// This work is licensed under the Creative Commons Attribution-ShareAlike 4.0
// International License. To view a copy of this license, visit
//
// http://creativecommons.org/licenses/by-sa/4.0/
//
// or send a letter to Creative Commons,
// PO Box 1866, Mountain View, CA 94042, USA.
//
//******************************************************************************
#ifndef ANSI_ART_H
#define ANSI_ART_H

#include <avr/pgmspace.h>



const uint8_t PROGMEM juliette_bitmap[] = {
    0x00, 0x32, 0x20, 0x00, 0x00, 0x2E, 0x00, 0x20, 0x2E, 0x4A, 0x69, 0x20, 0x18, 0xC3, 0x00, 0x07, 0x20, 0x00, 0x00, 0x0A, 0x00, 
    0x31, 0x20, 0x00, 0x00, 0x2D, 0x52, 0xA9, 0x23, 0xC6, 0x36, 0x23, 0xD6, 0x98, 0x20, 0x08, 0x41, 0x00, 0x07, 0x20, 0x00, 0x00, 
    0x0A, 0x00, 0x0A, 0x20, 0x00, 0x00, 0x2E, 0x21, 0x04, 0x2B, 0x62, 0xEA, 0x3A, 0x52, 0x69, 0x3A, 0x42, 0x07, 0x3A, 0x29, 0x45, 
    0x2E, 0x18, 0xC3, 0x20, 0x08, 0x41, 0x00, 0x1E, 0x20, 0x00, 0x00, 0x3A, 0x31, 0xA6, 0x2A, 0xAD, 0x53, 0x40, 0xE7, 0x3A, 0x40, 
    0xF7, 0x9B, 0x23, 0x94, 0x90, 0x00, 0x08, 0x20, 0x00, 0x00, 0x0A, 0x00, 0x0A, 0x20, 0x00, 0x00, 0x2B, 0x94, 0x71, 0x25, 0xDE, 
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
    0x00, 0x20, 0x0A, 0x00, 0x09, 0x20, 0x00, 0x00, 0x20, 0x08, 0x41, 0x2A, 0xAC, 0xD2, 0x2A, 0xC4, 0xD2, 0x2A, 0xB4, 0x71, 0x2B, 
    0xAC, 0x50, 0x2B, 0xA4, 0x50, 0x2A, 0xAC, 0xD2, 0x2A, 0xB5, 0x33, 0x2A, 0xB5, 0x13, 0x2A, 0xA4, 0xD2, 0x2B, 0x9C, 0x70, 0x2B, 
    0x8B, 0xCE, 0x3D, 0x8B, 0x8D, 0x2B, 0x93, 0xEF, 0x3D, 0x7B, 0x0B, 0x3A, 0x41, 0x65, 0x20, 0x18, 0x61, 0x20, 0x18, 0x81, 0x2E, 
    0x31, 0x24, 0x3A, 0x41, 0xC6, 0x3A, 0x49, 0xE6, 0x2D, 0x62, 0xA9, 0x2D, 0x5A, 0x48, 0x00, 0x02, 0x2D, 0x5A, 0x68, 0x3A, 0x4A, 
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


#endif /* ANSI_ART_H */ 
